whutddk/MK64F-platform/doc/designDoc/1-1-MK-LQFP144/mmexport1516165831264.bmp

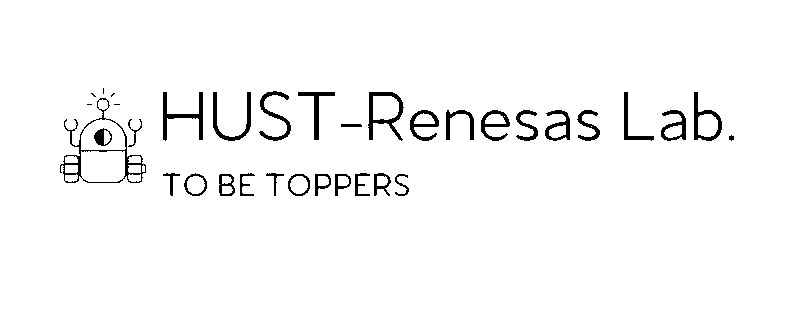
doc/designDoc/1-1-MK-LQFP144/mmexport1516165831264.bmp
