whutddk/MK64F-platform/outputFile/pre-release-version/0-4-Cmsis-dap32F103.pdf

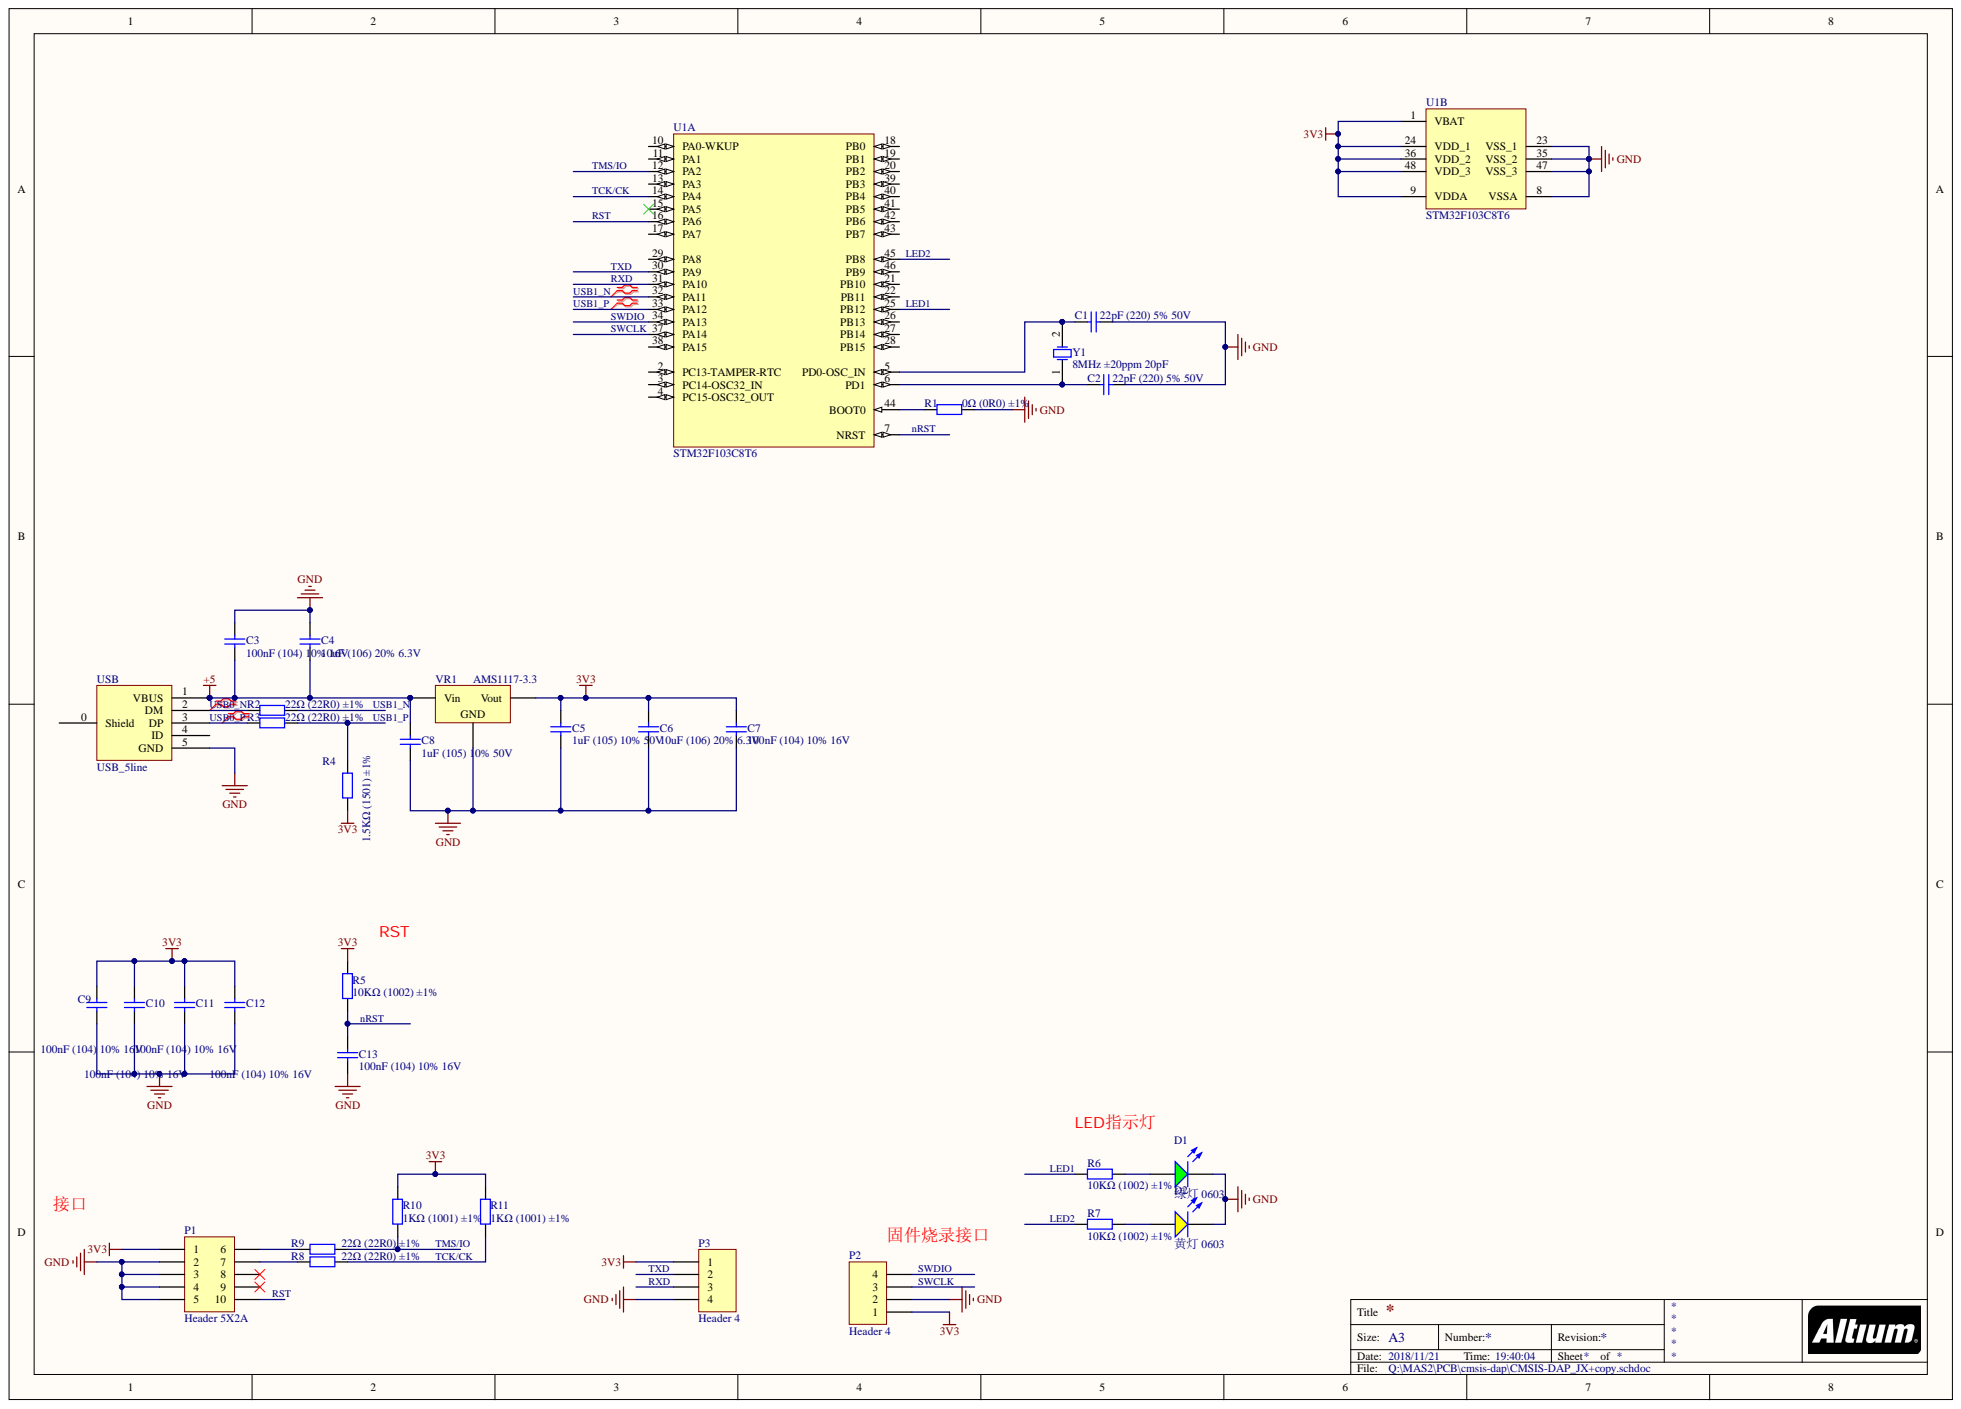
[picture p39: page 1]

* Title | * * * * *

Size: A3 | Number: * | Revision: *
Date: 2018/11/21 Time: 19:40:04 | | Sheet * of *

Q:\MAS2\PCB\cmsis-dap\CMSIS-DAP_JX+copy.schdoc

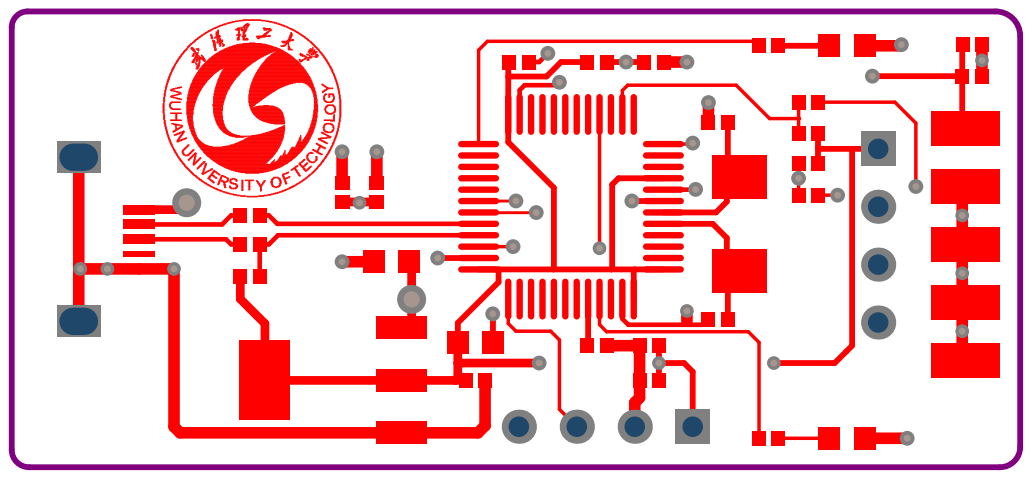
[picture p40: page 2]

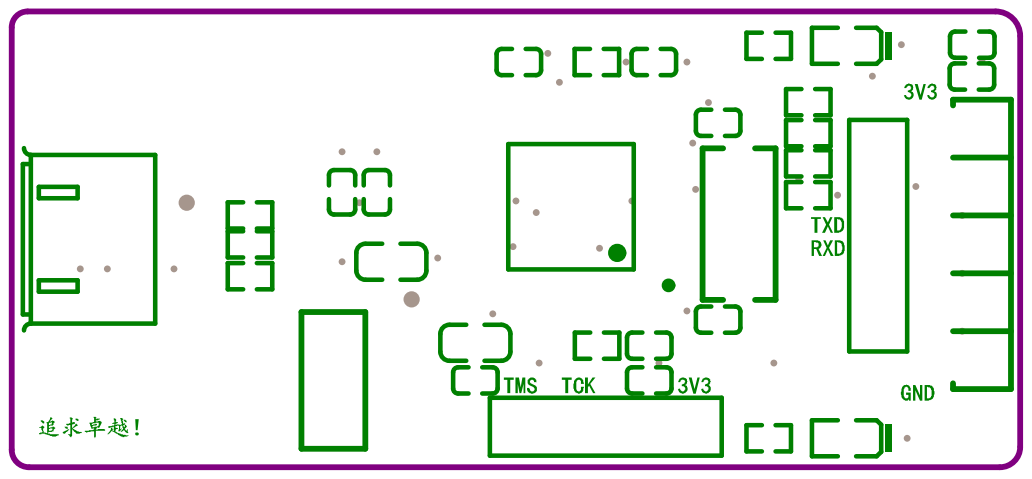
[picture p41: page 3]

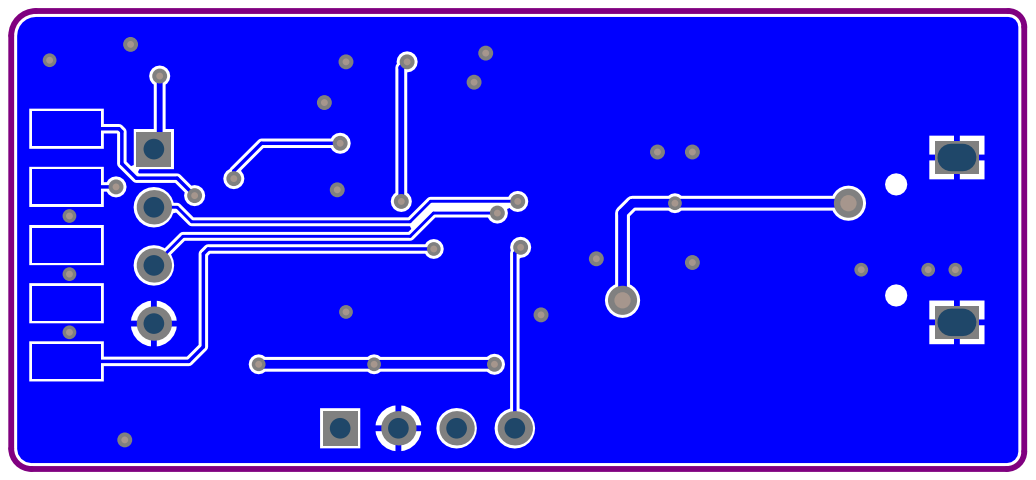
[picture p42: page 4]

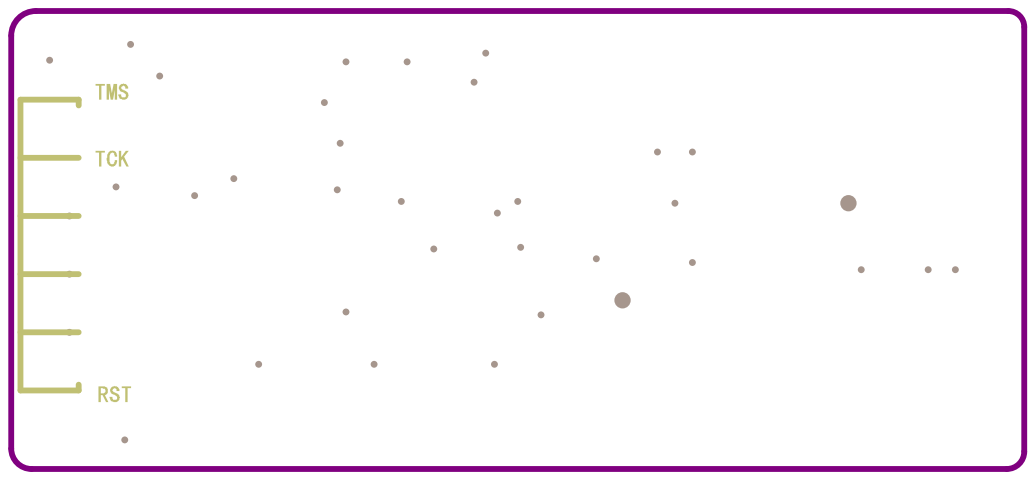
[picture p43: page 5]
