whutddk/MK64F-platform/doc/referDoc/STM32/XNUCLEO.pdf

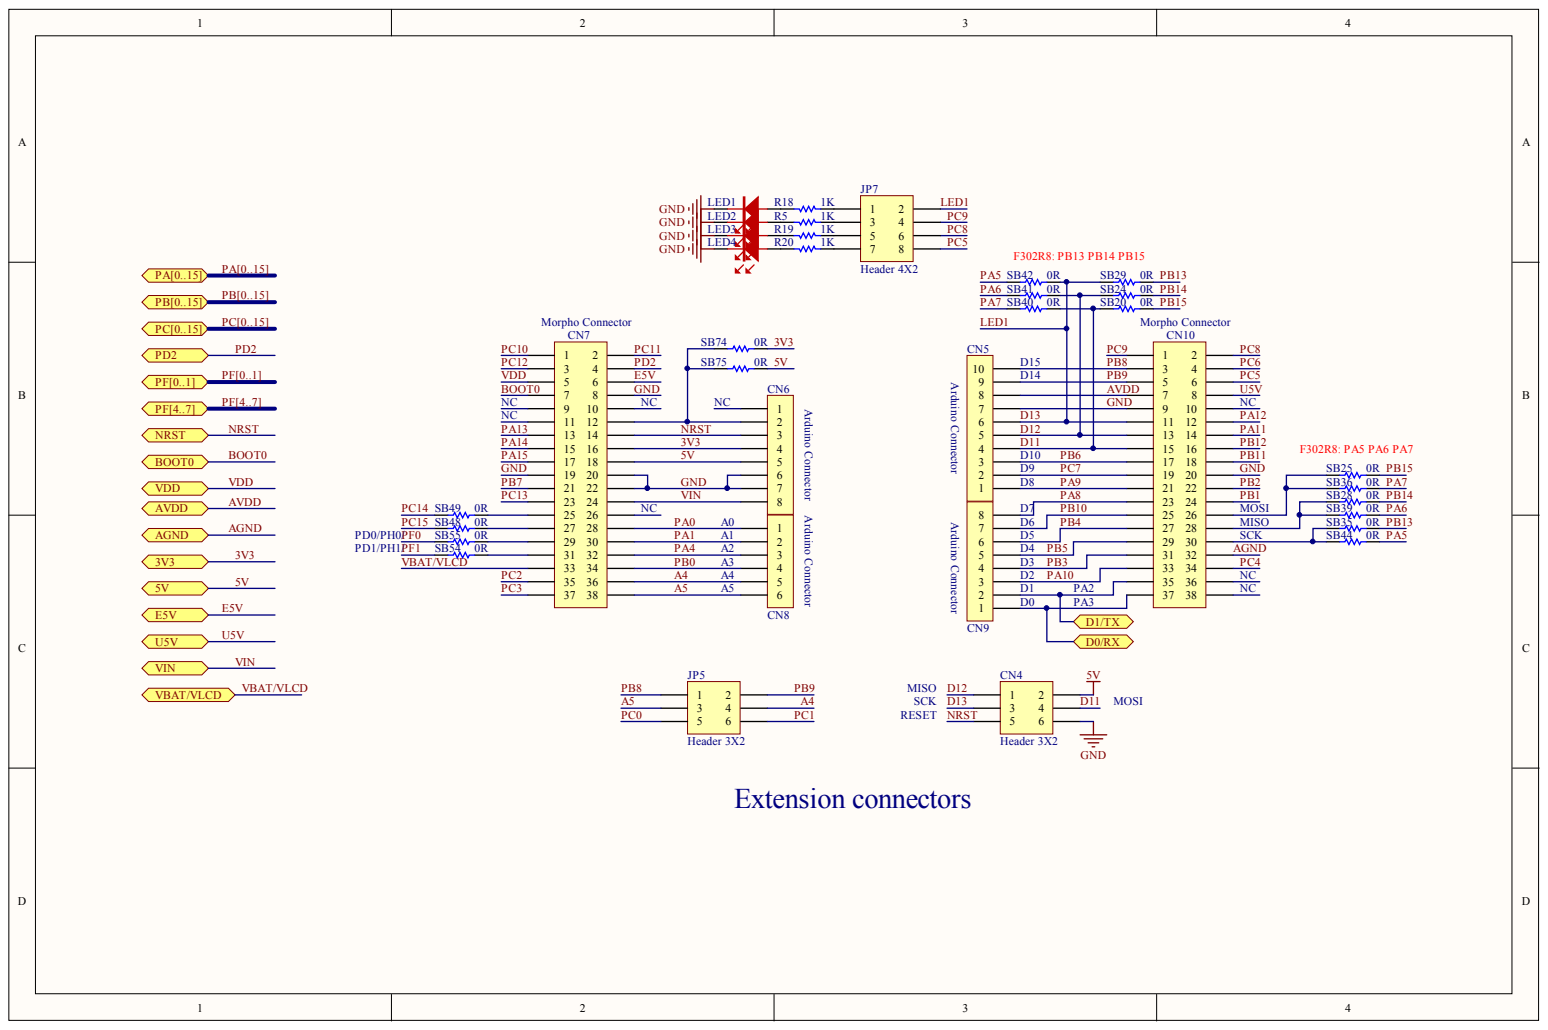
[picture p44: page 1]

Arduino Connector

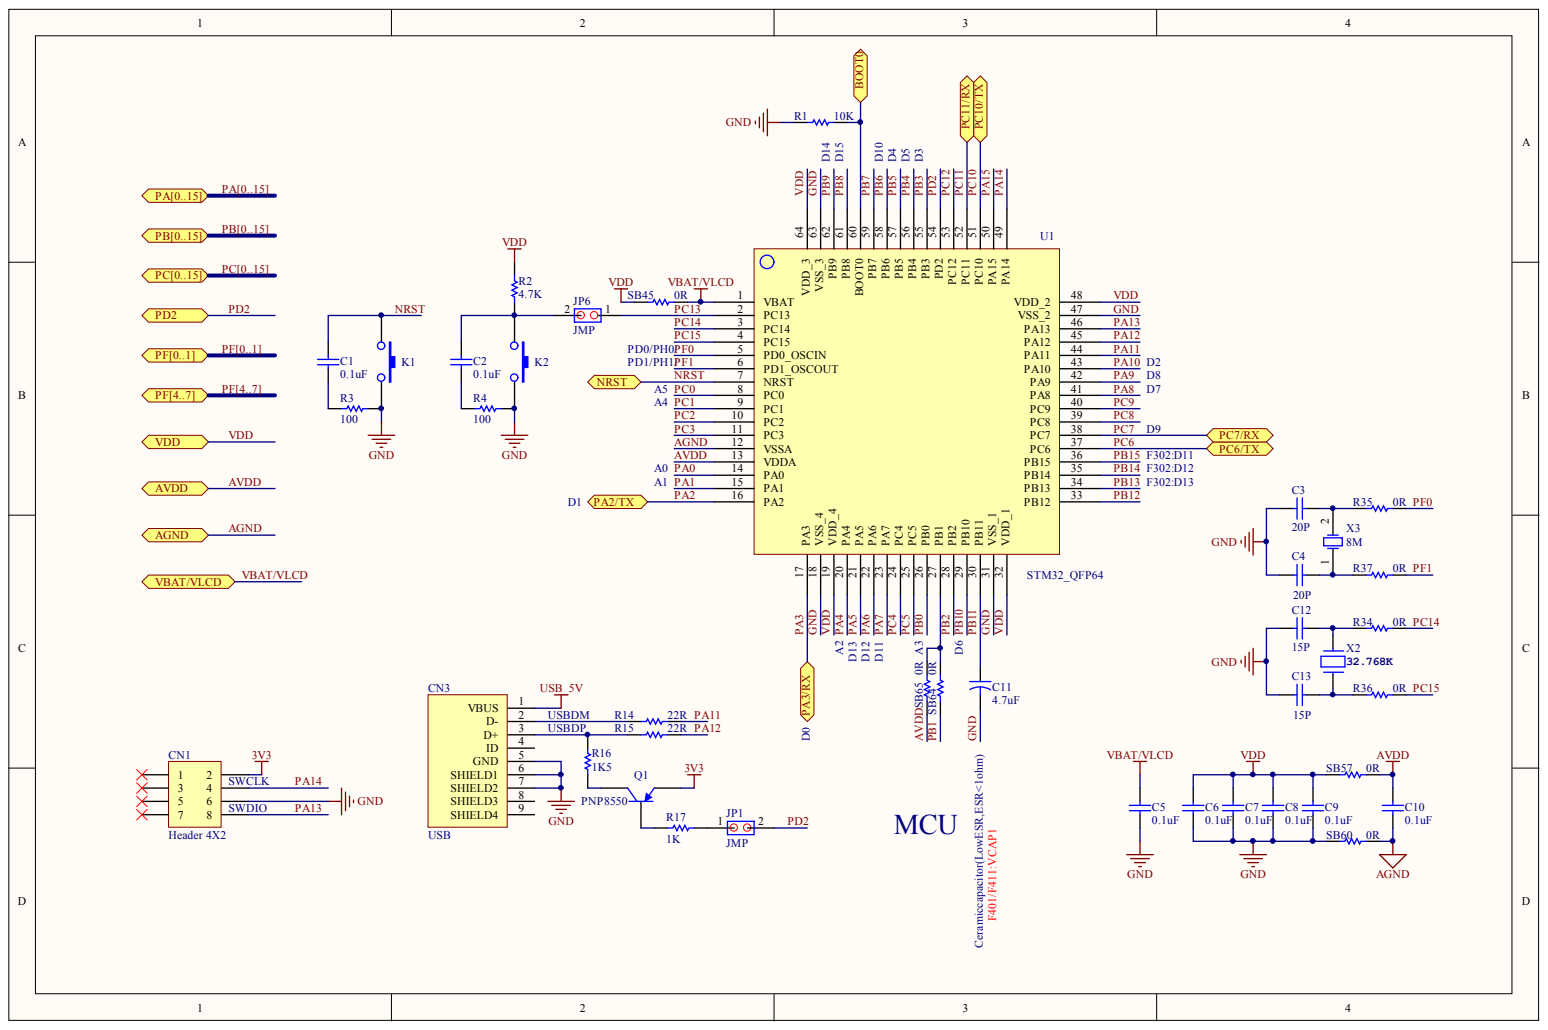
[picture p45: page 2]

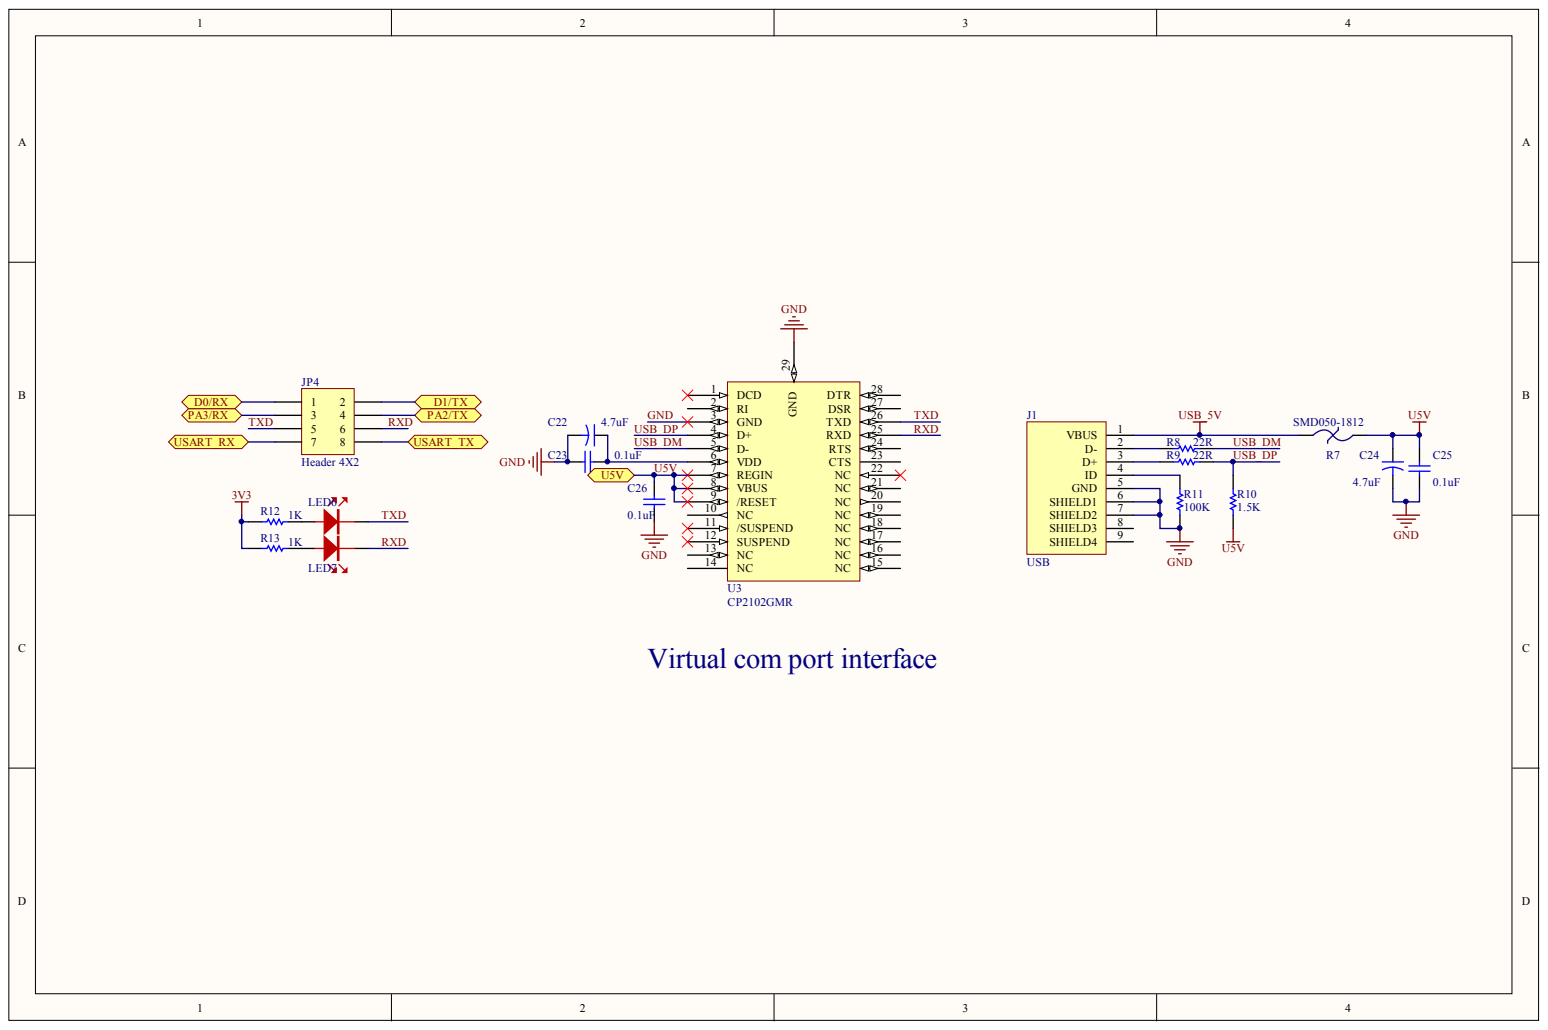
[picture p46: page 3]

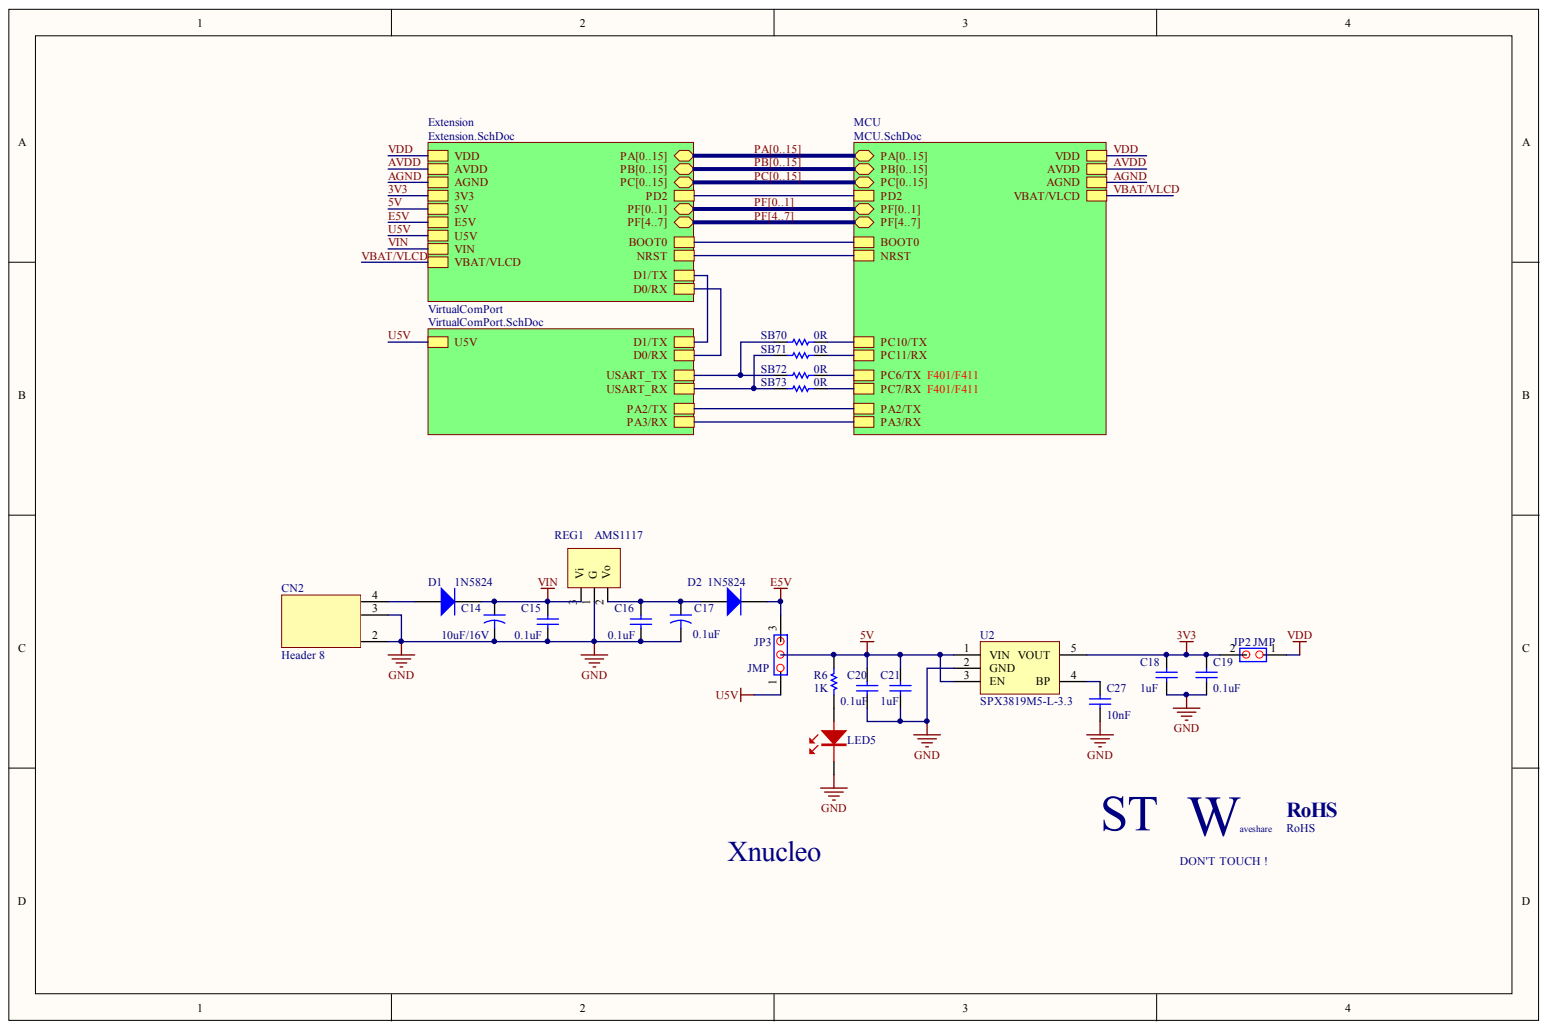
[picture p47: page 4]
