whutddk/MK64F-platform/doc/referDoc/MAPS-K64/07.MAPS-Dock.pdf

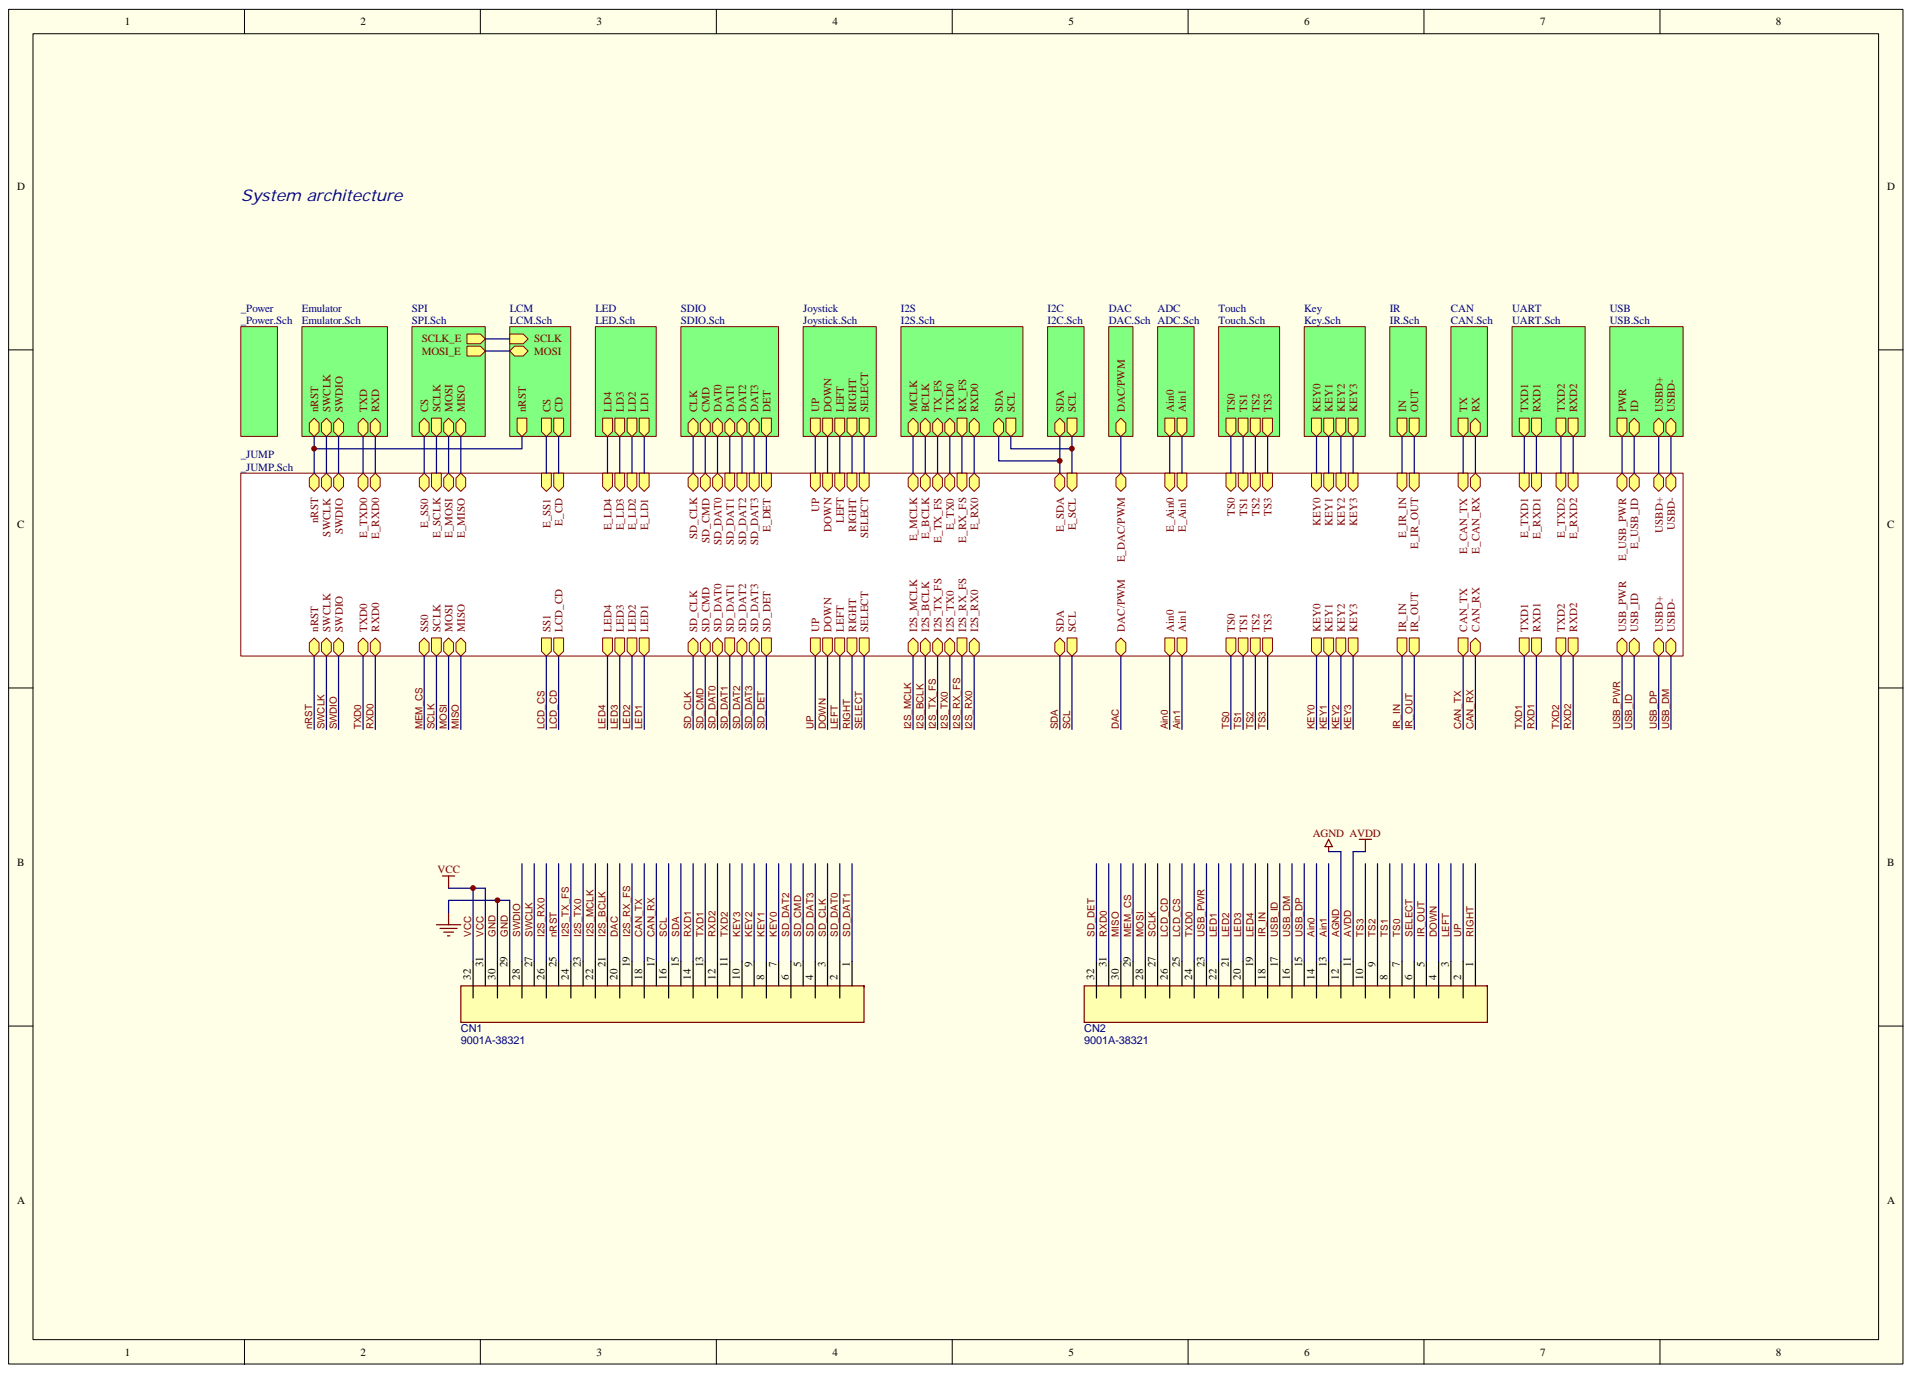
[picture p48: page 1]
SWCLK; SWDIO; TXD0; RXD0; MEM_CS; SCLK; MOSI; MISO; LCD_CS; LCD_CD; SD_CLK; SD_CMD; SD_DAT0; SD_DET; DOWN; LEFT; RIGHT; SELECT; I2S_MCLK; I2S_BCLK; DAC; IR_OUT; CAN_TX; CAN_RX; TXD1; RXD1; TXD2; RXD2; USB_PWR; USB_DP; USB_DM; E_MCLK; E_BCLK; E_TXD1 E_RXD1; E_TXD2; E_RXD2; E_MISO; E_SCLK E_MOSI; E_Ain1; E_CAN_TX; E_CAN_RX; E_IR_OUT; SD_DAT1; E_SDA E_SCL; E_DAC/PWM; E_TXD0; E_RXD0; E_USB_PWR; USBD+; USBD-; KEY2; SCLK MOSI; LED3; I2S_MCLK I2S_BCLK; SDA SCL; DAC/PWM; Ain1; KEY1; nRST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

USB USB.Sch

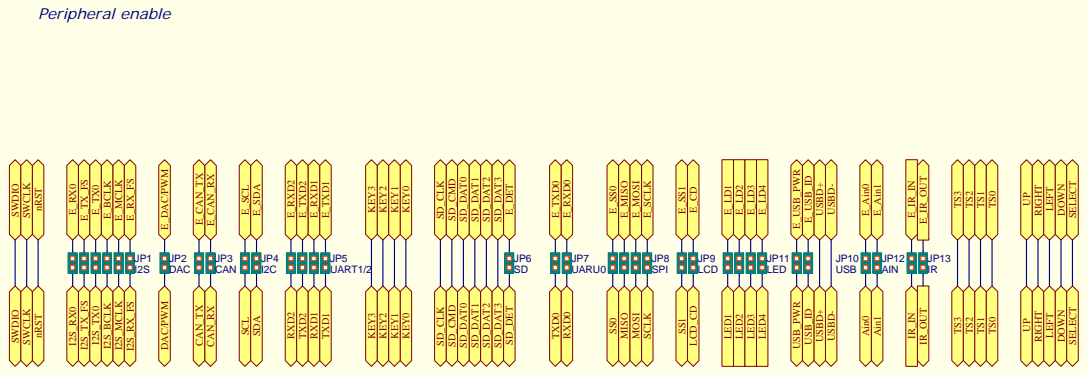
[picture p49: page 2]

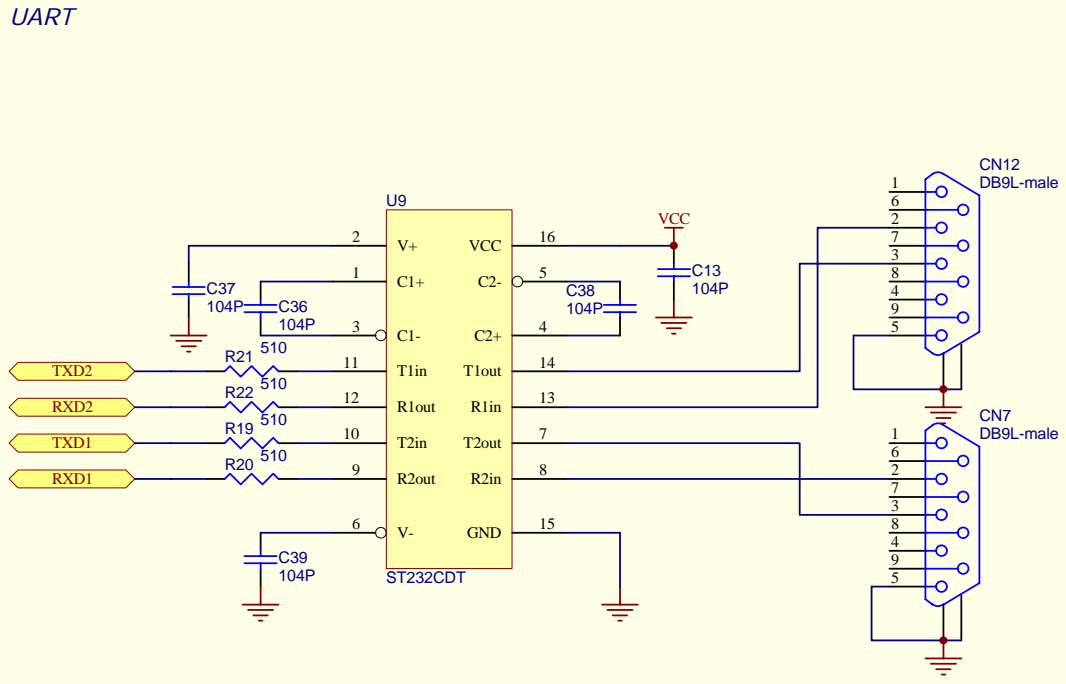
[picture p50: page 3]

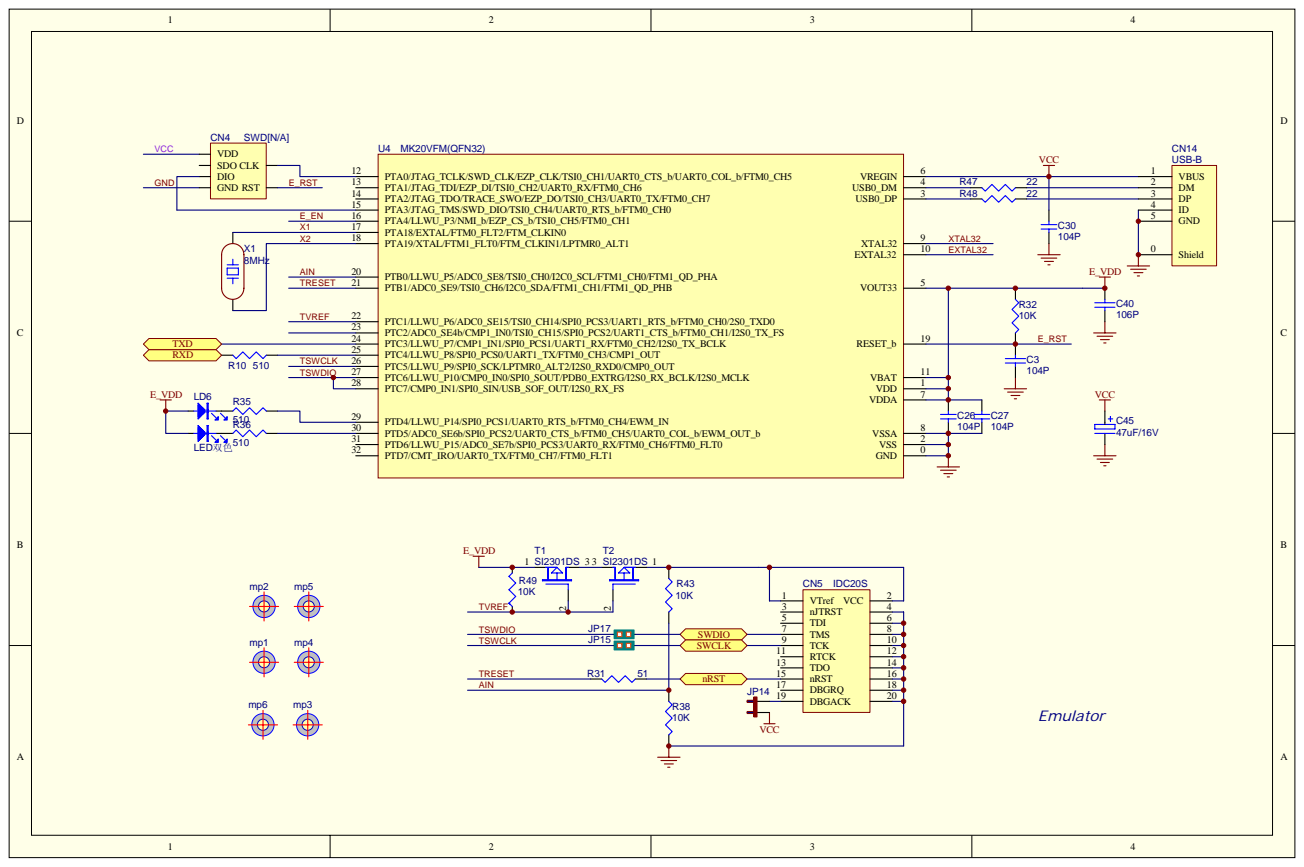
[picture p51: page 4]

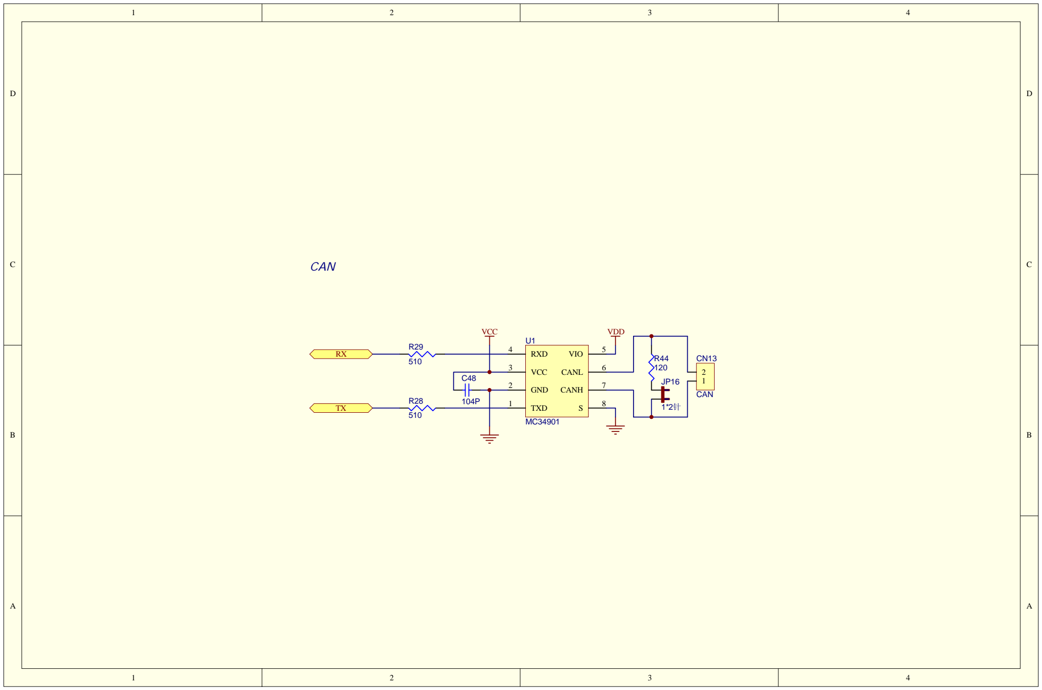
[picture p52: figure]
TXD 1; GND 2; VCC 3; RXD 4; VIO; CANL; CANH; CAN; VCC; VDD
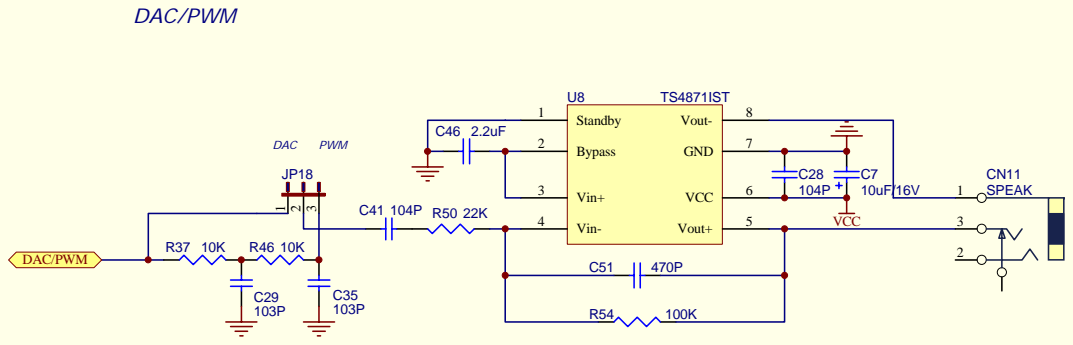
[picture p53: page 6]

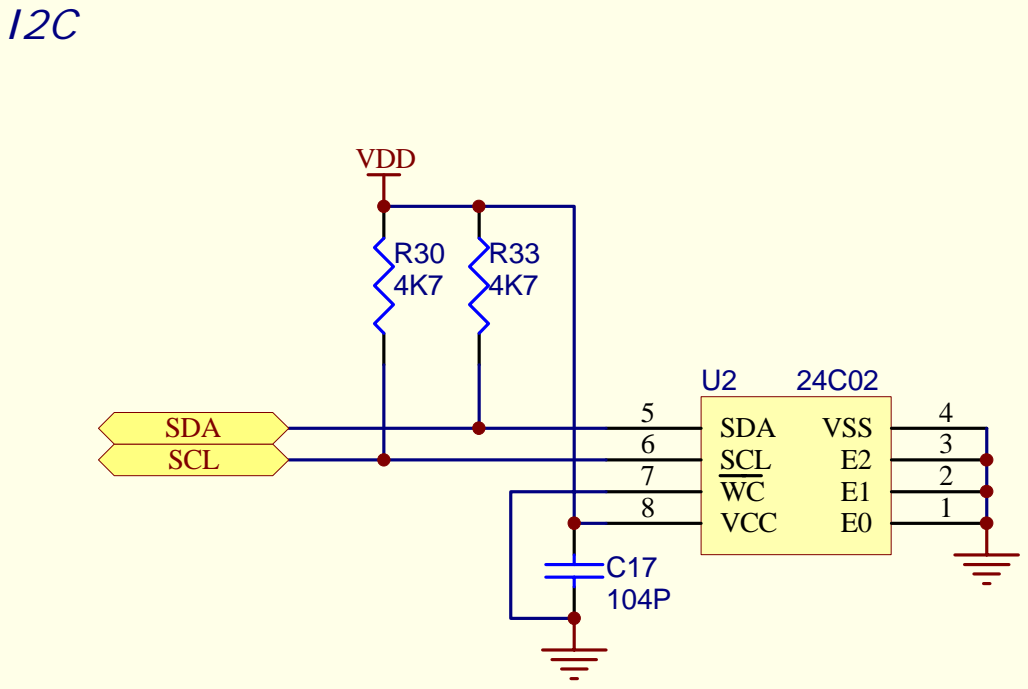
[picture p54: page 7]
3 VSS; 4 SDA 5; SCL 6; VCC 8; VDD; SCL; SDA

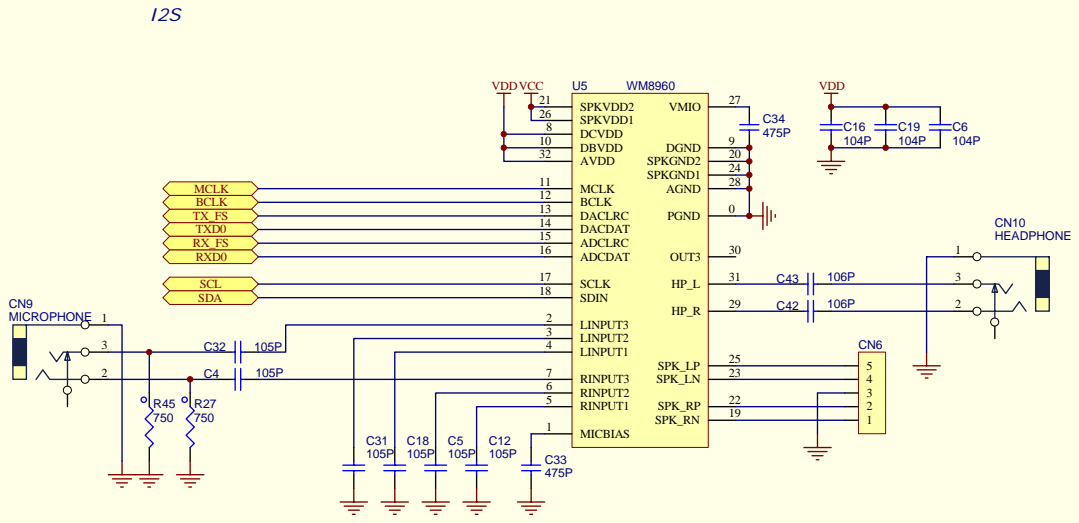
[picture p55: page 8]

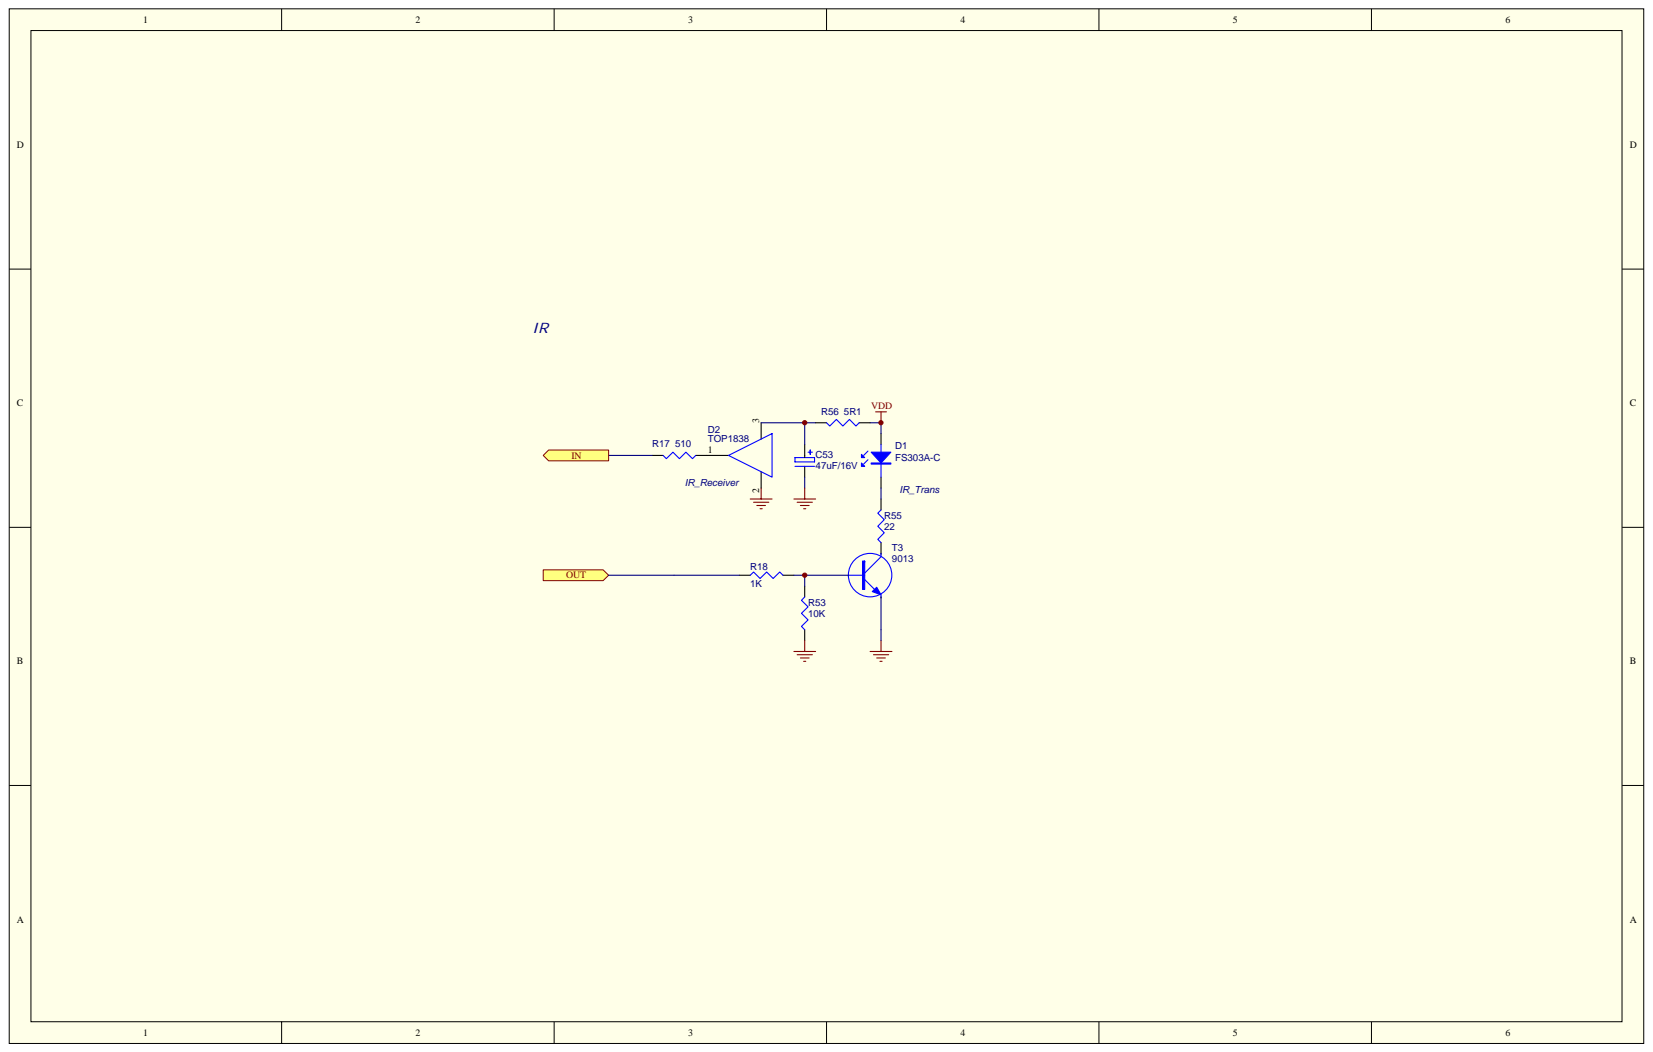
[picture p56: page 9]

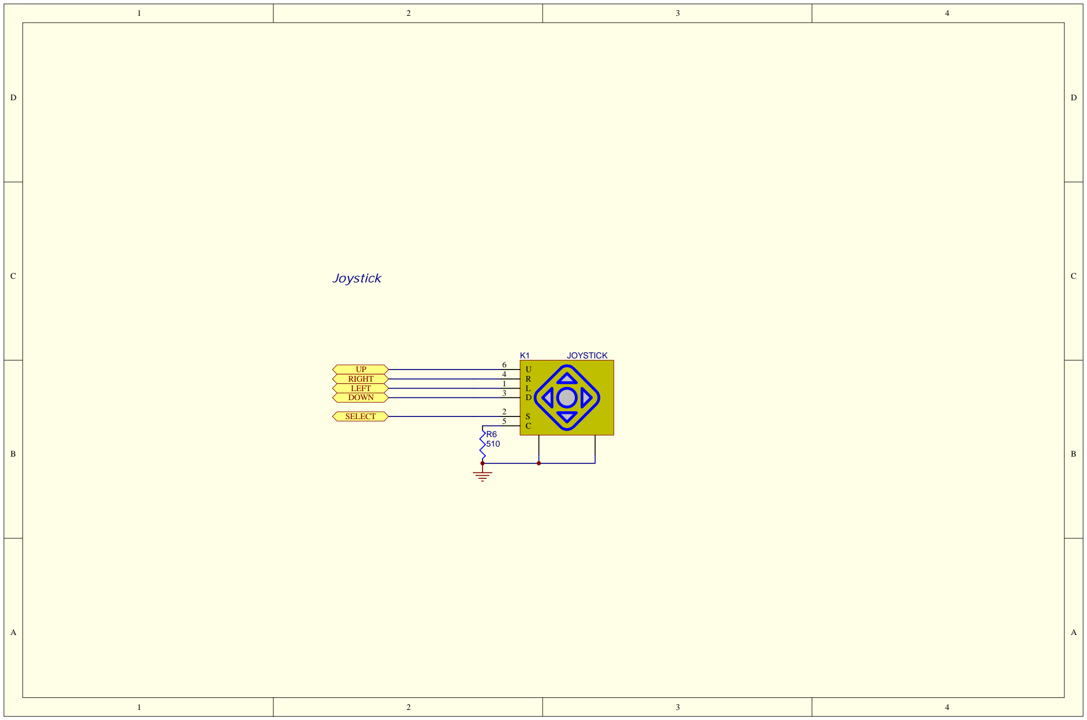
[picture p57: figure]
UP RIGHT LEFT DOWN; SELECT; JOYSTICK; Joystick
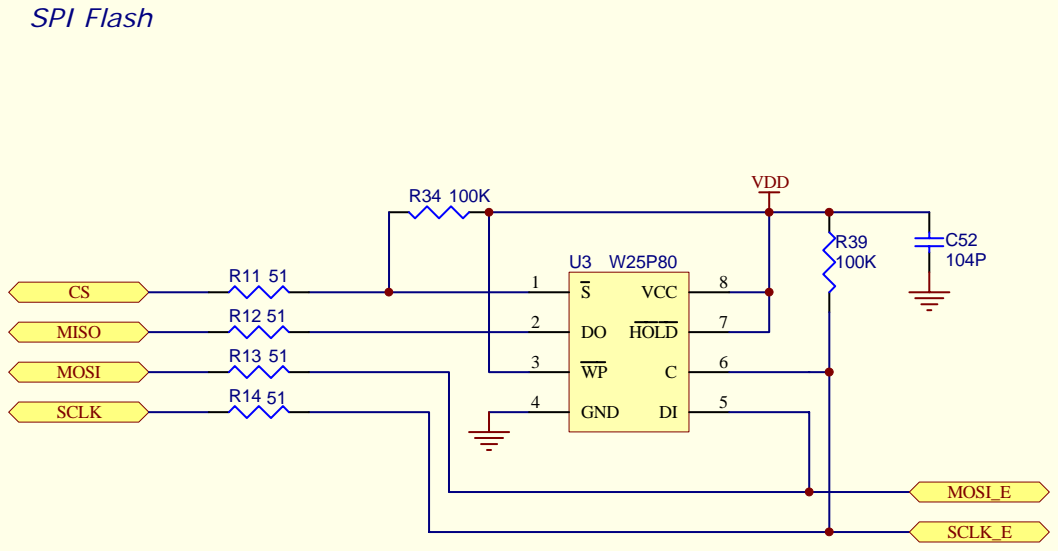
[picture p58: page 11]

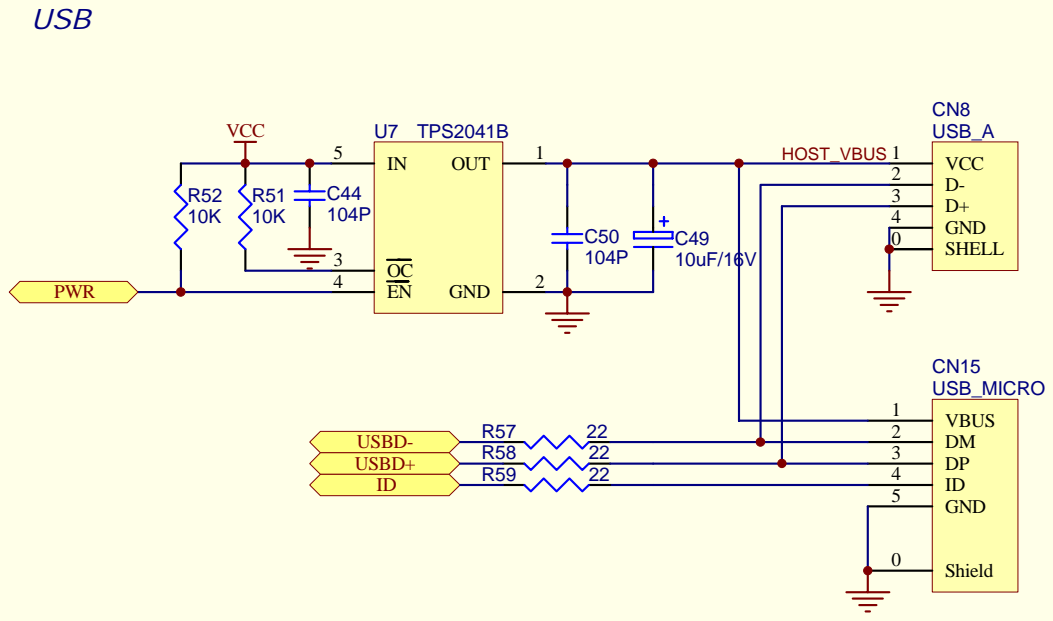
[picture p59: page 12]

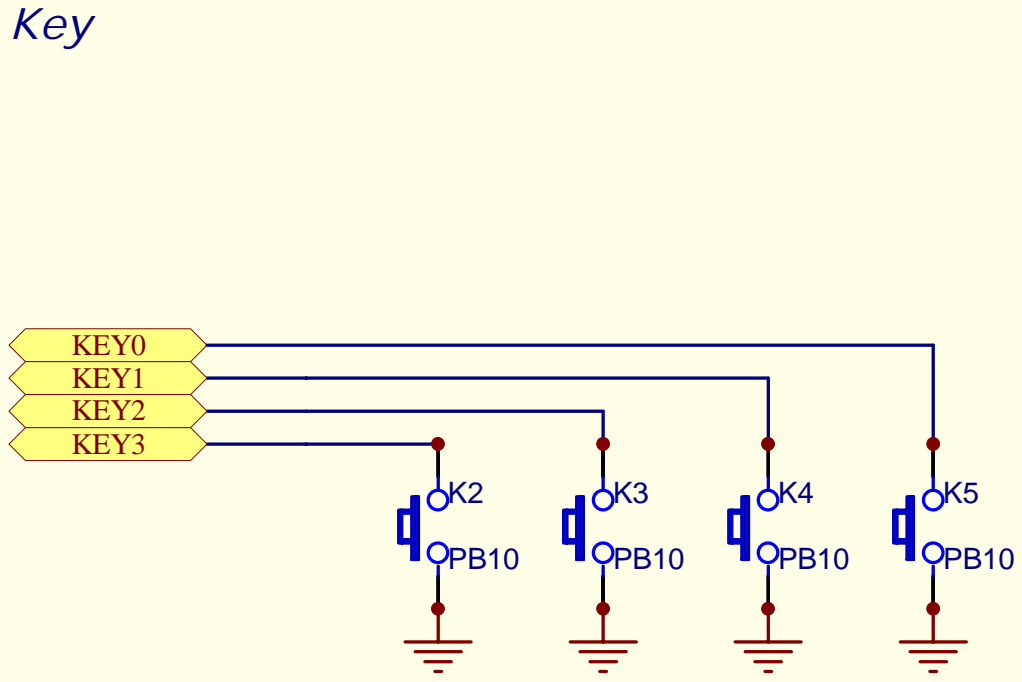
[picture p60: page 13]
KEY0; KEY1 KEY2 KEY3; Key

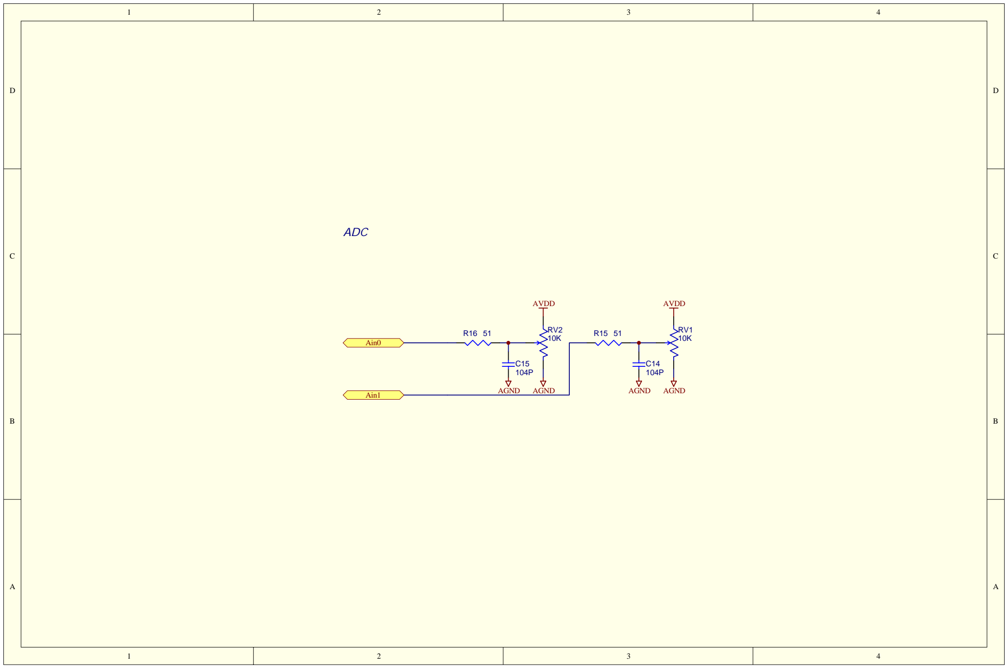
[picture p61: figure]
Ain0; AVDD; AGND; AGND Ain1; ADC
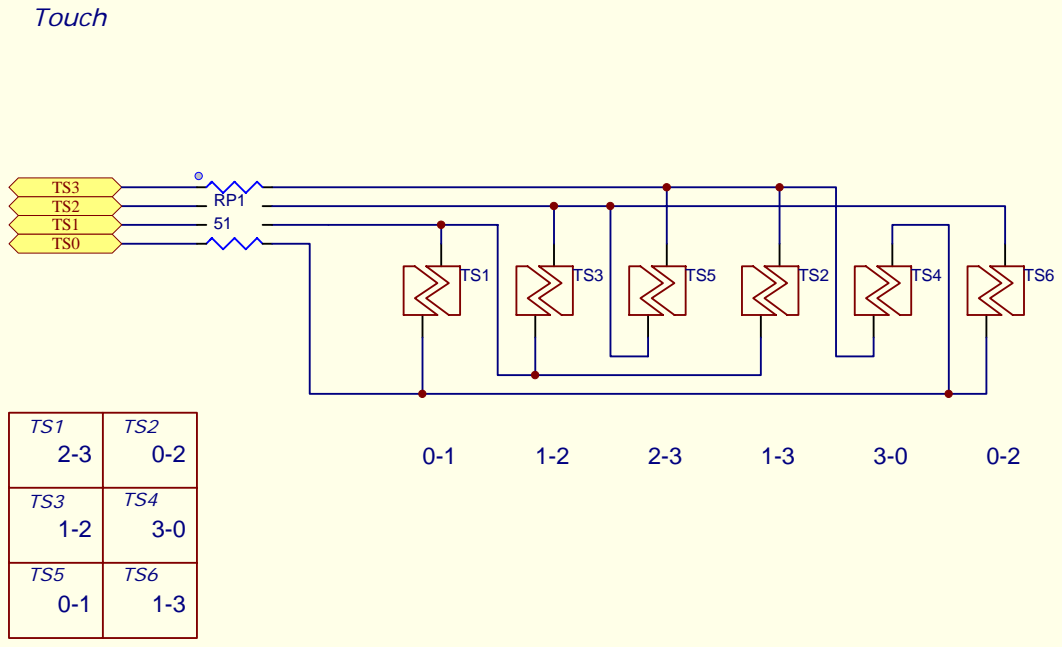
[picture p62: page 15]
Touch

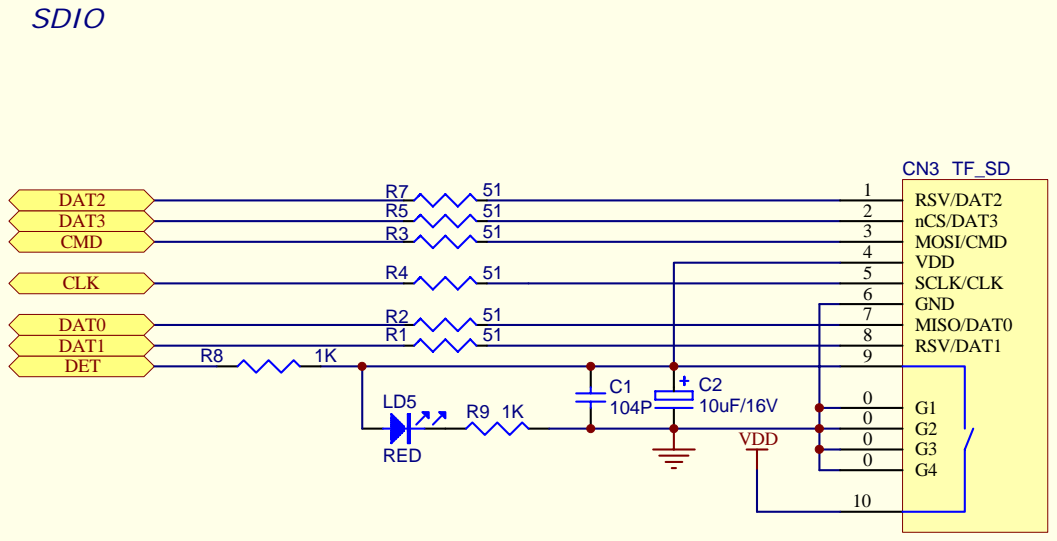
[picture p63: page 16]

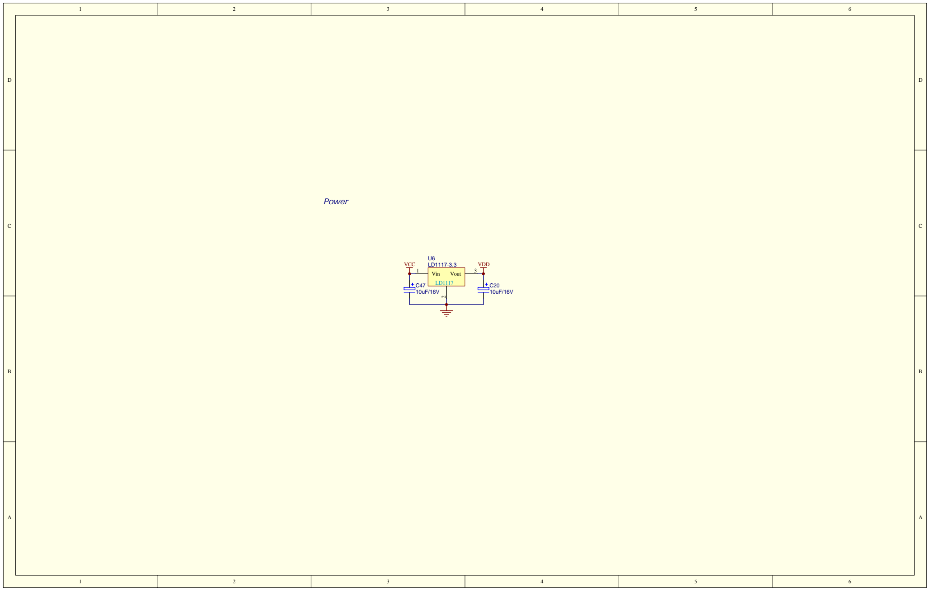
[picture p64: figure]
VDD; Vout; 3 Vin 1; VCC; Power
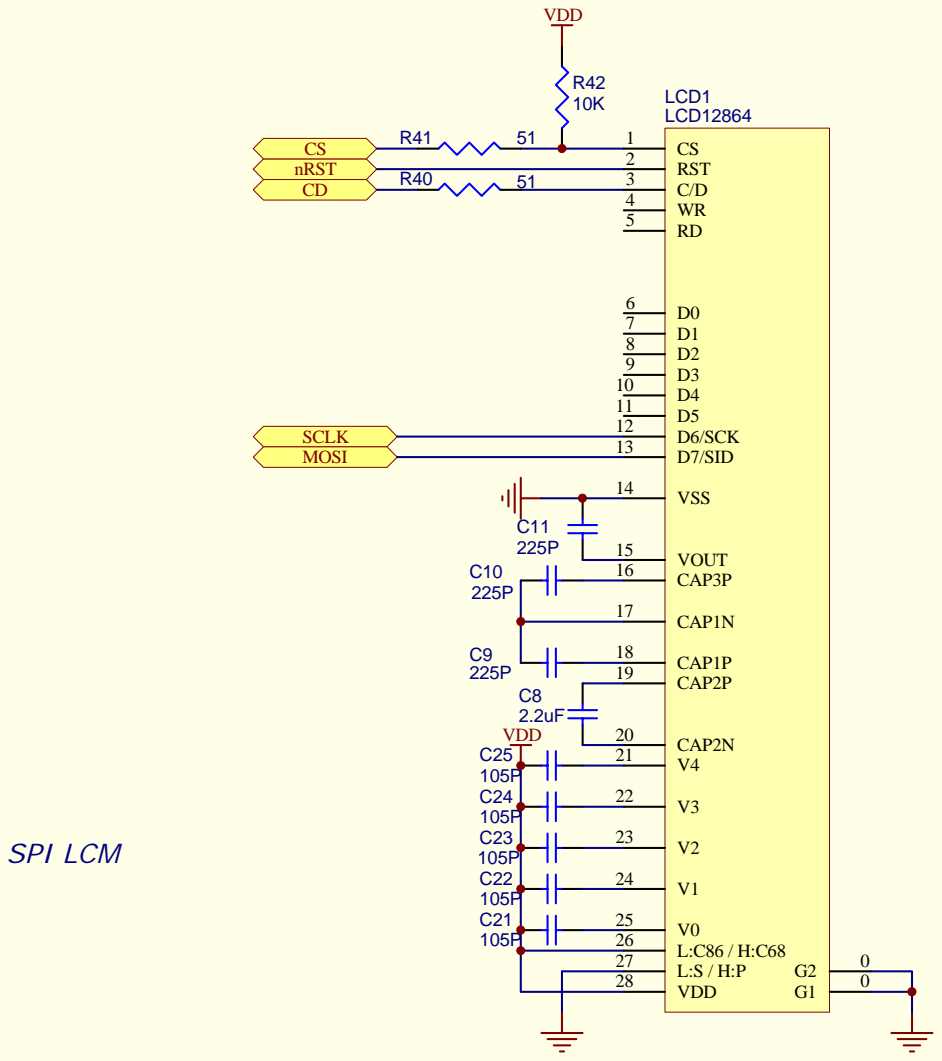
[picture p65: page 18]

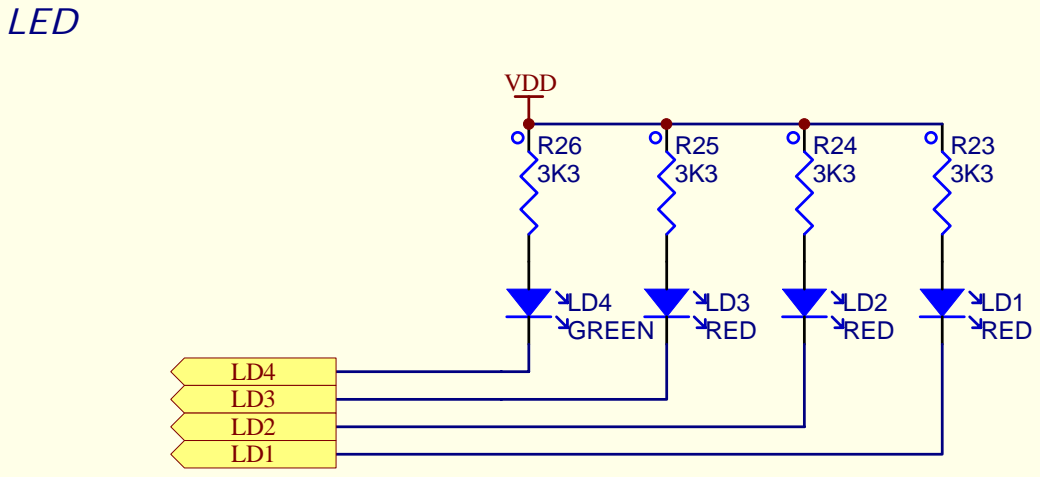
[picture p66: page 19]
LD3 RED; LD4 GREEN; LD1 RED; LD2 RED; VDD; LED
