whutddk/MK64F-platform/PCB/pre-release-version/abort-version/1.6.1/flexplatV1.PDF

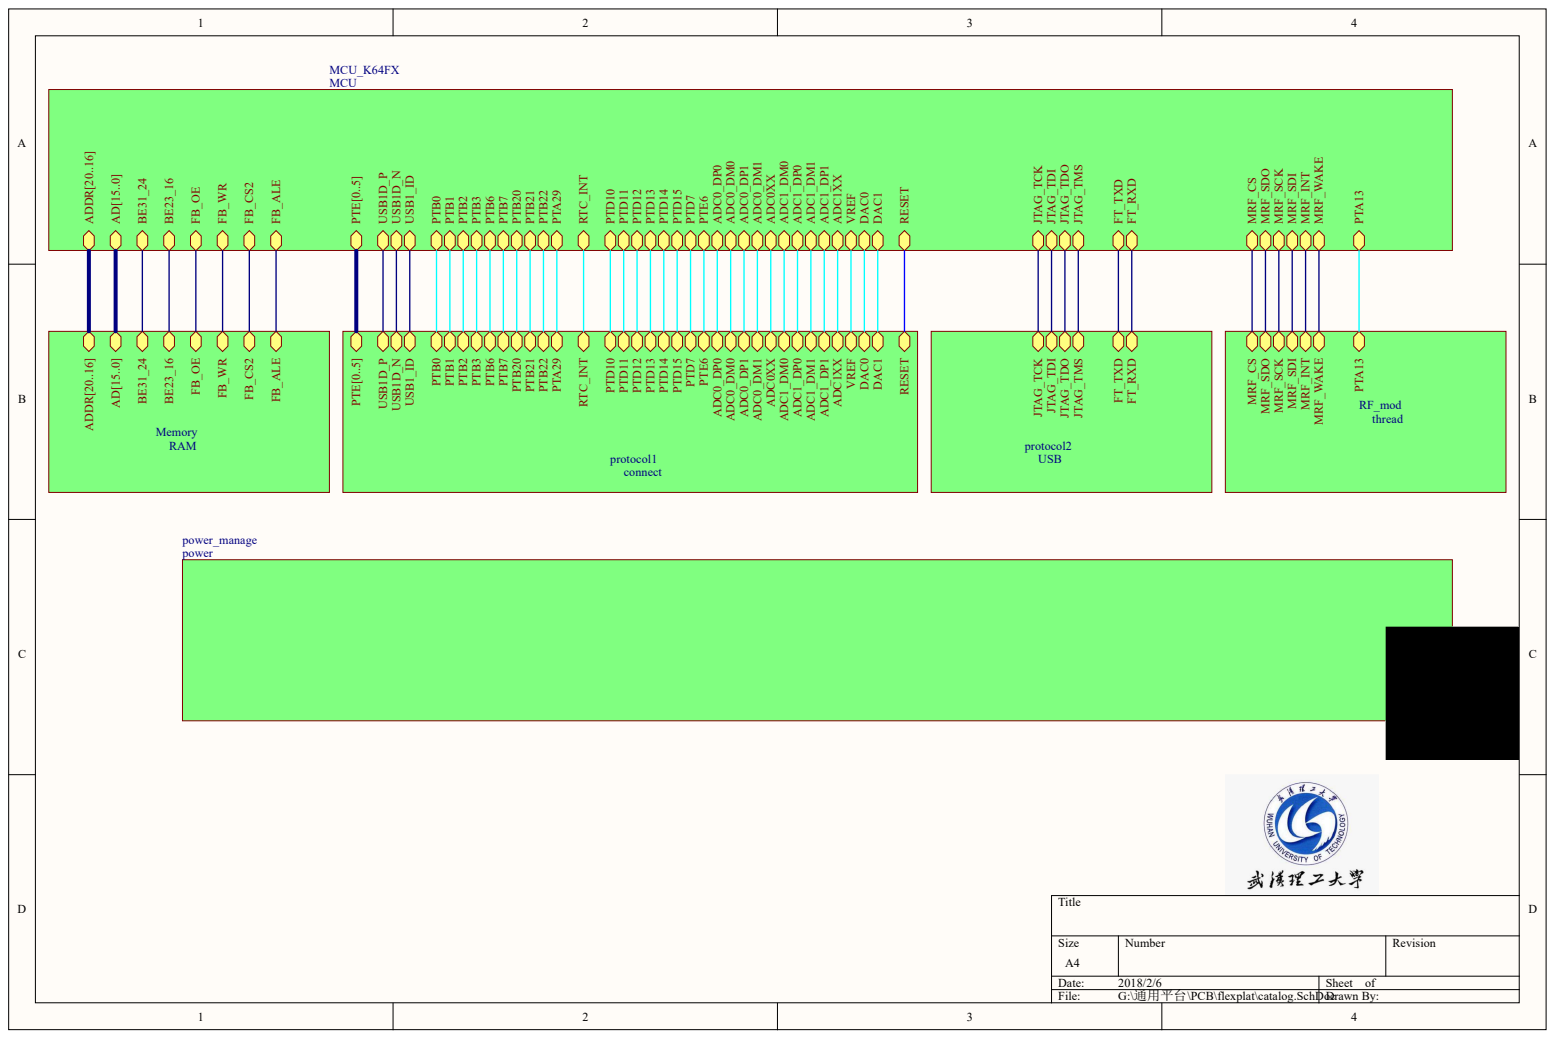
[picture p67: page 1]

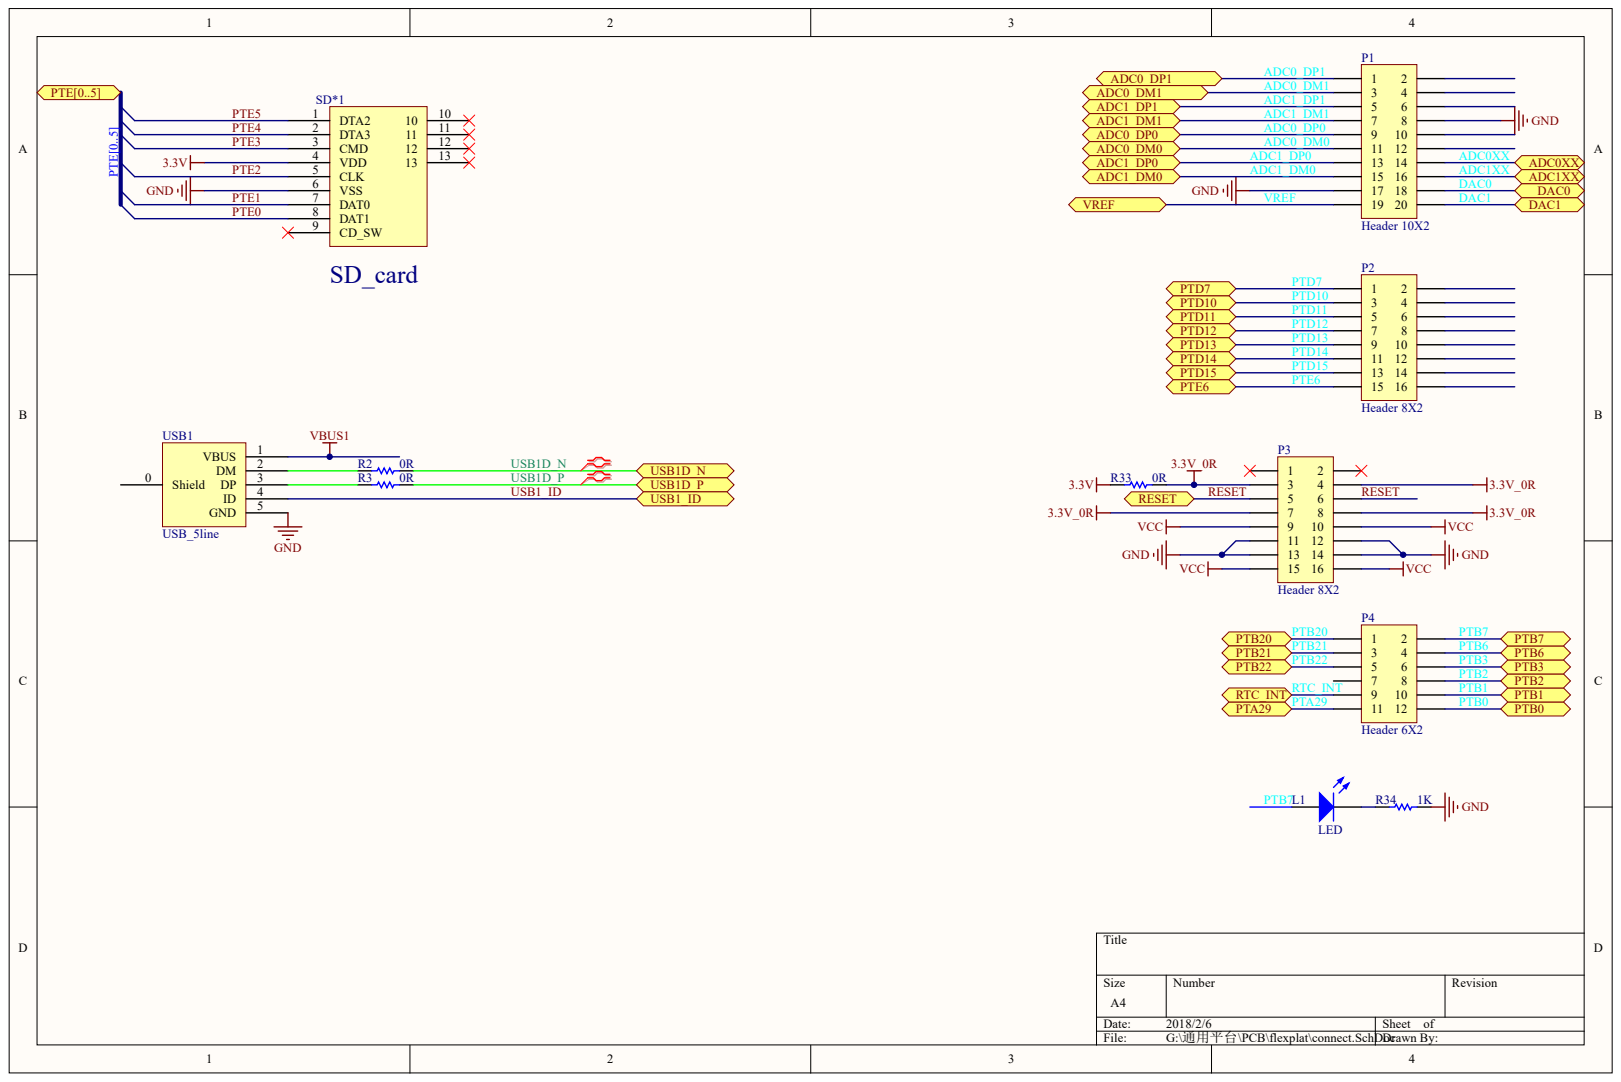
[picture p68: page 2]

PCB\flexplat\connect.SchDoc Drawn By:

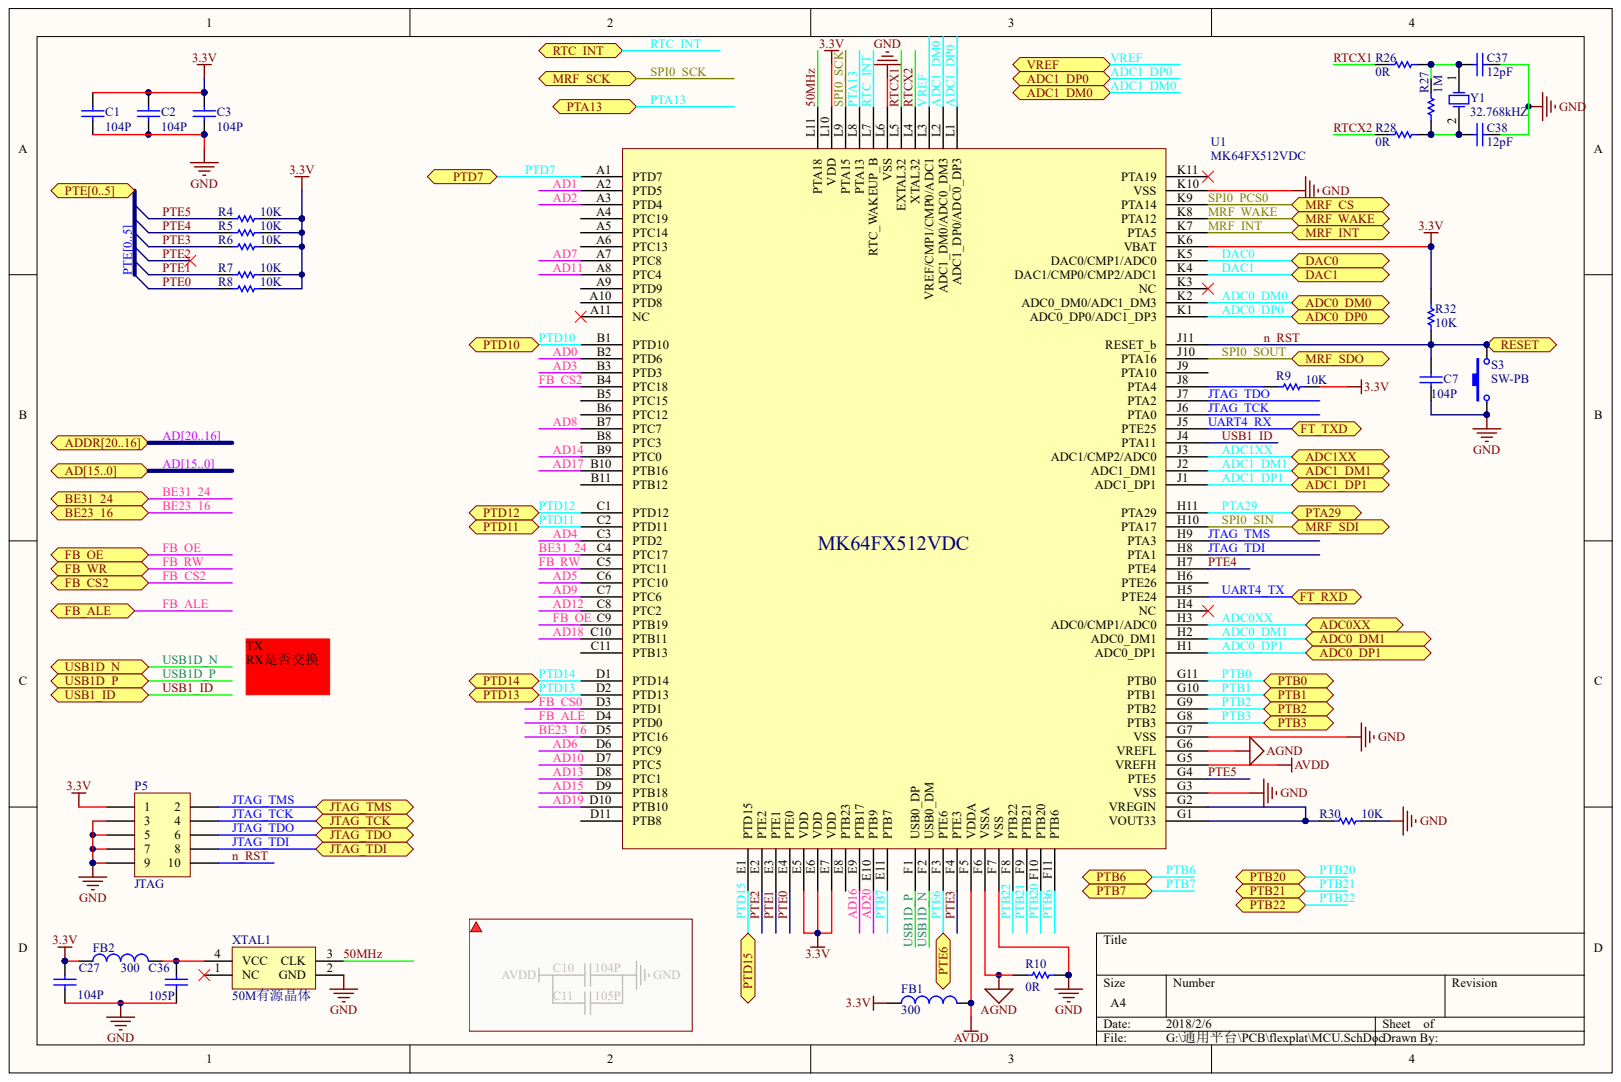
[picture p69: page 3]

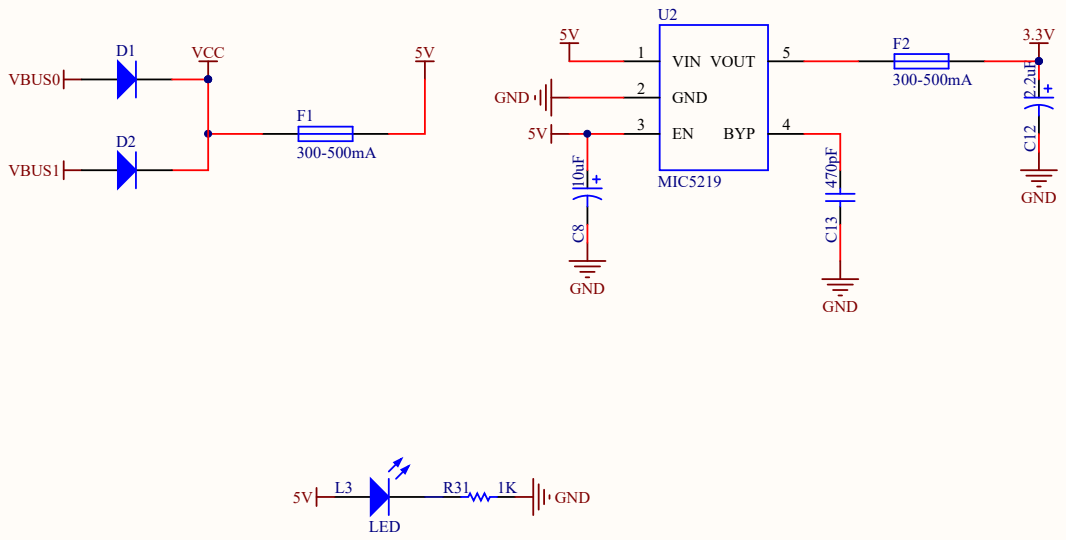
[picture p70: page 4]

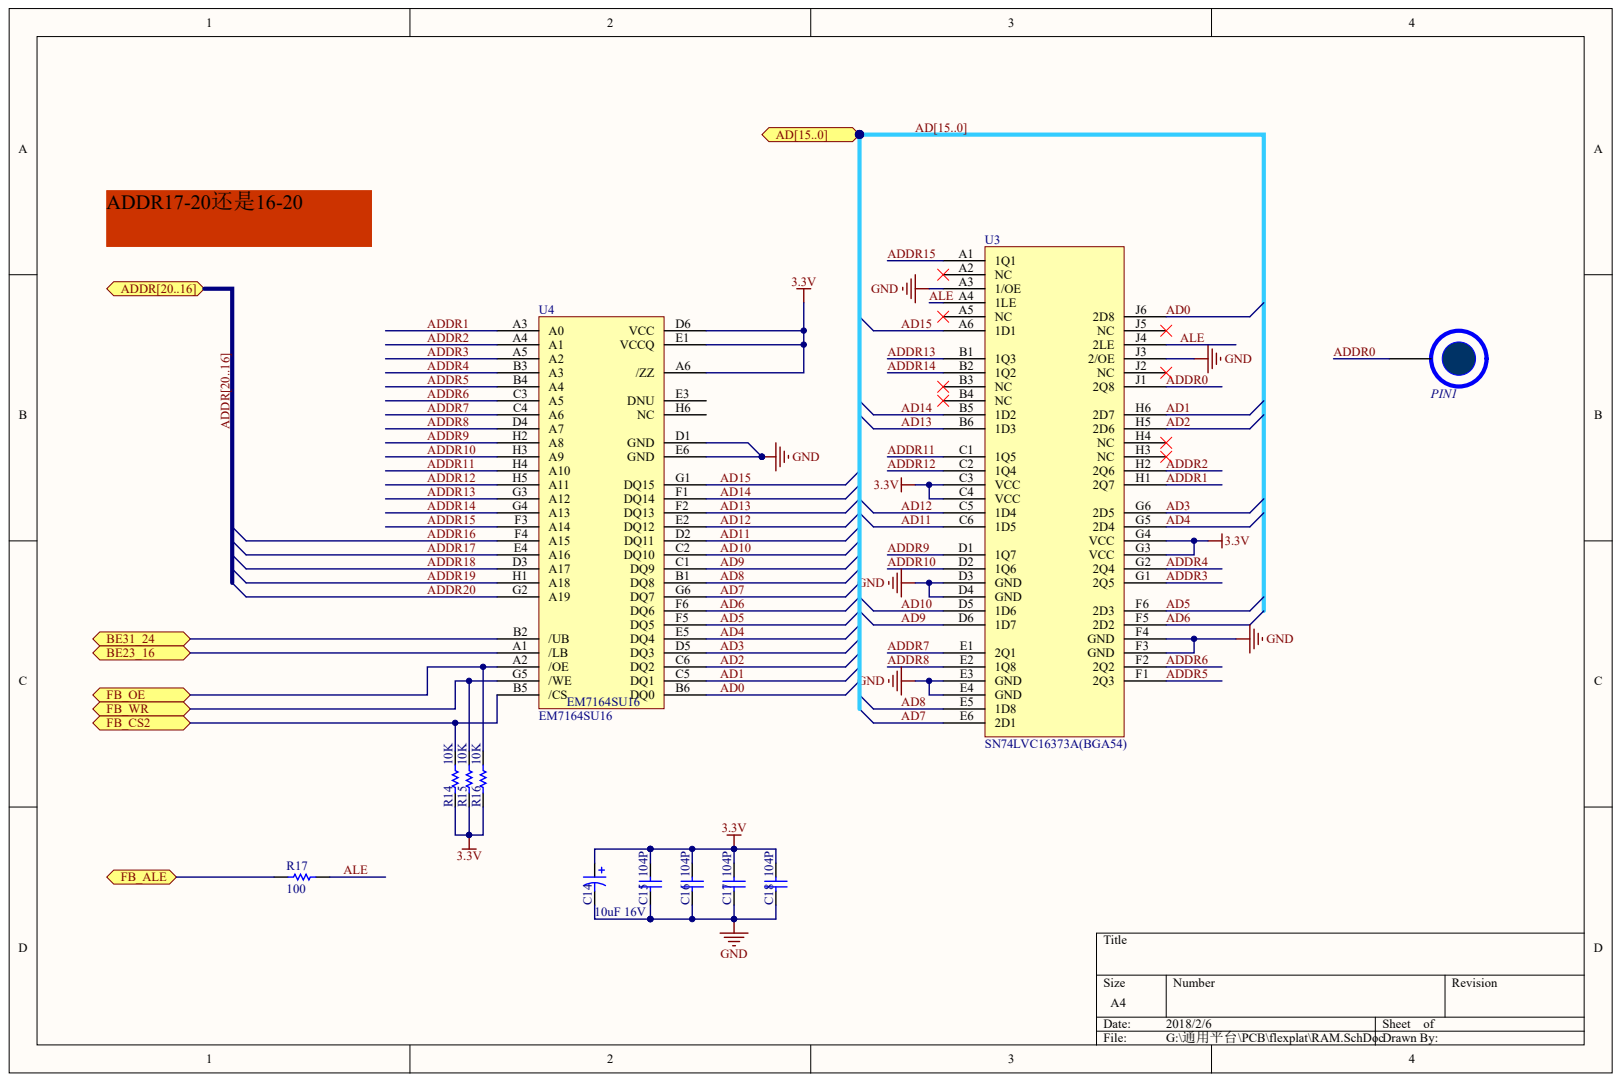
[picture p71: page 5]

PCB\flexplat\RAM.SchDocDrawn By:

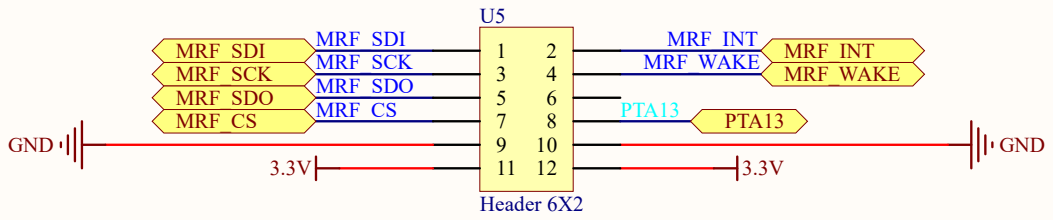
[picture p72: page 6]

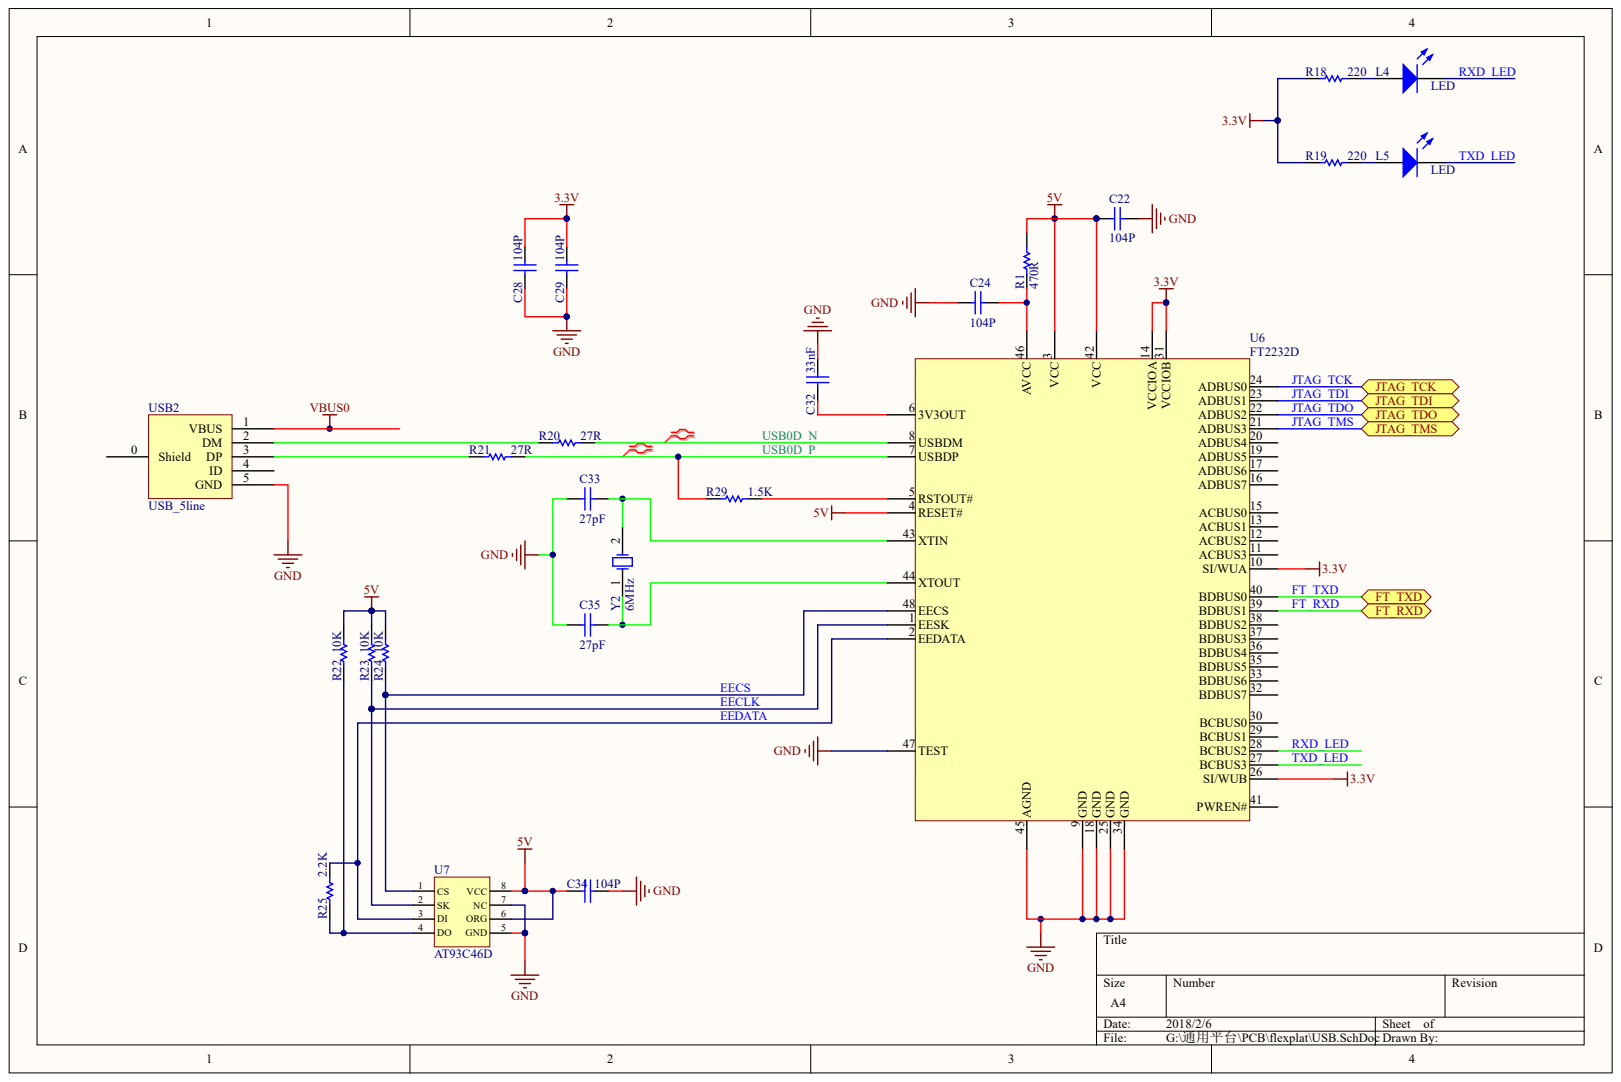
[picture p73: page 7]

EECS 48

EEDATA 2

EECLK
EEDATA

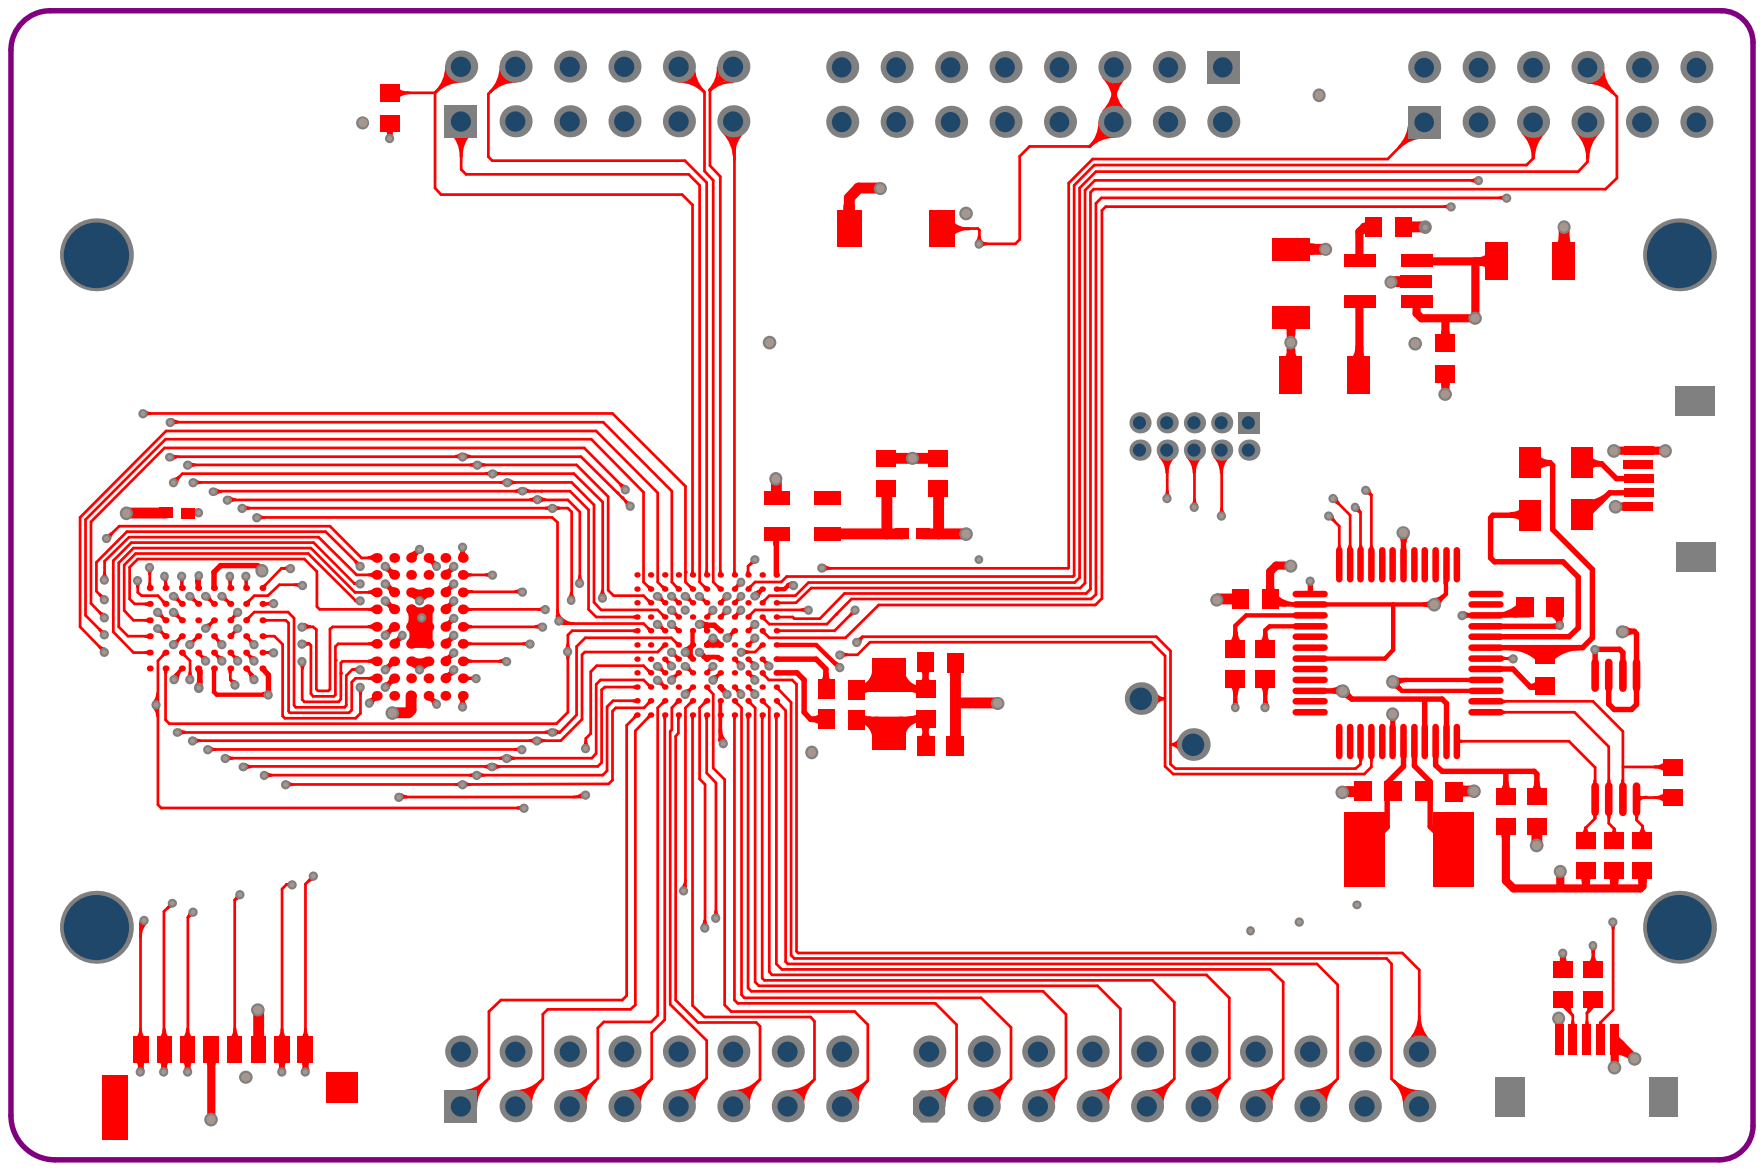
[picture p74: page 8]

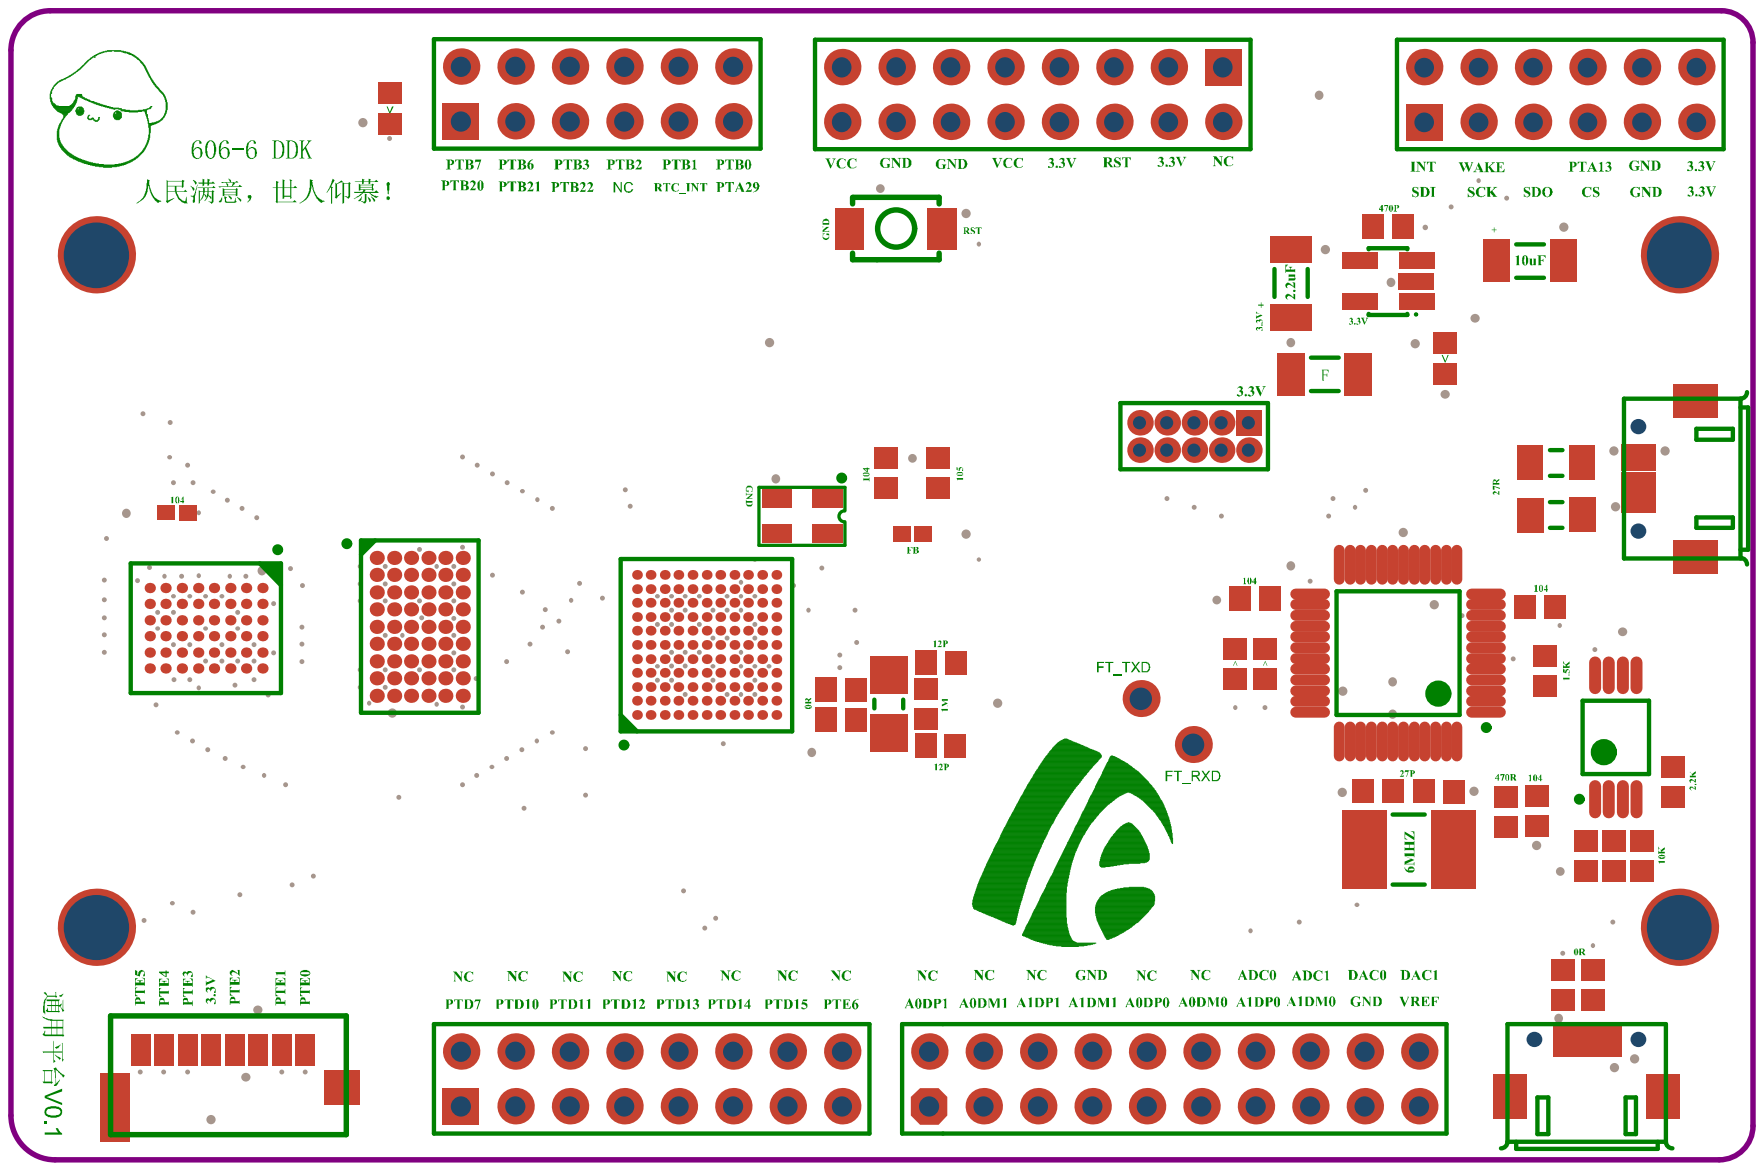
[picture p75: page 9]

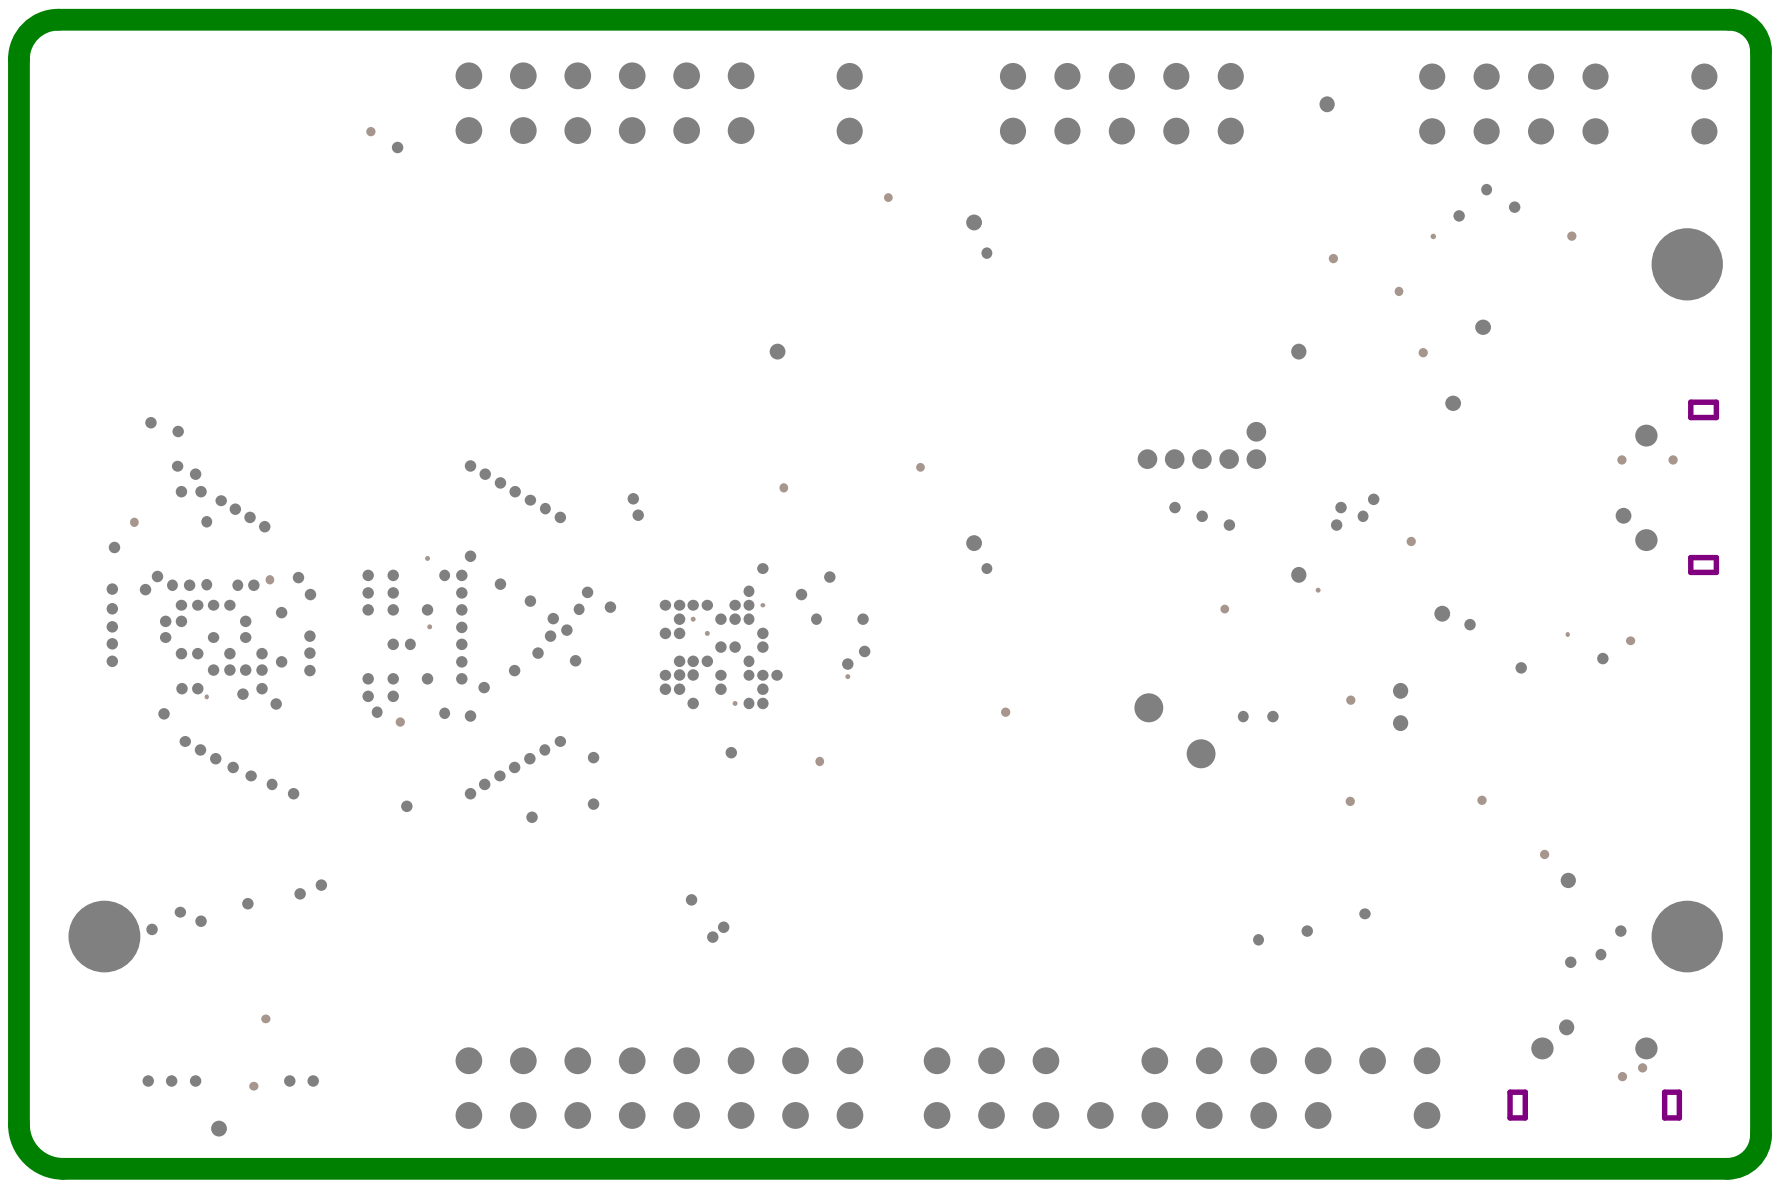
[picture p76: page 10]

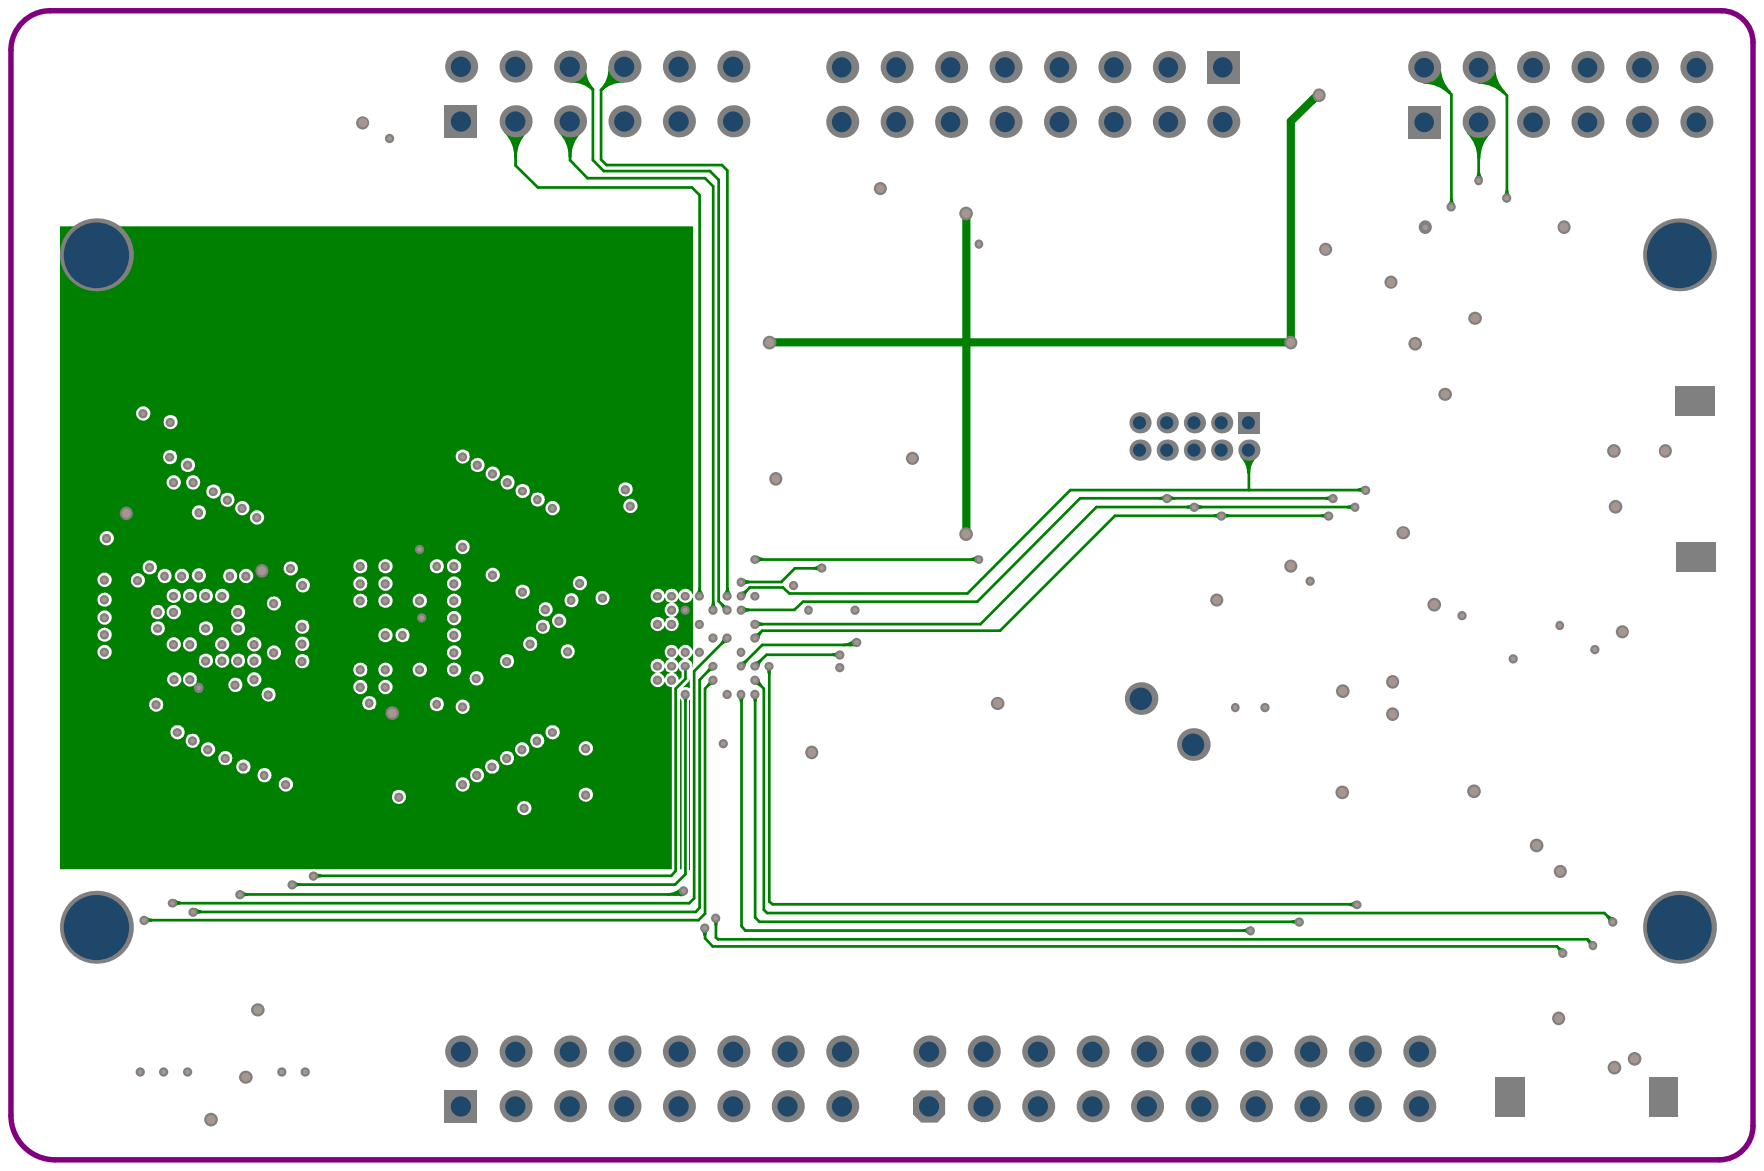
[picture p77: page 11]

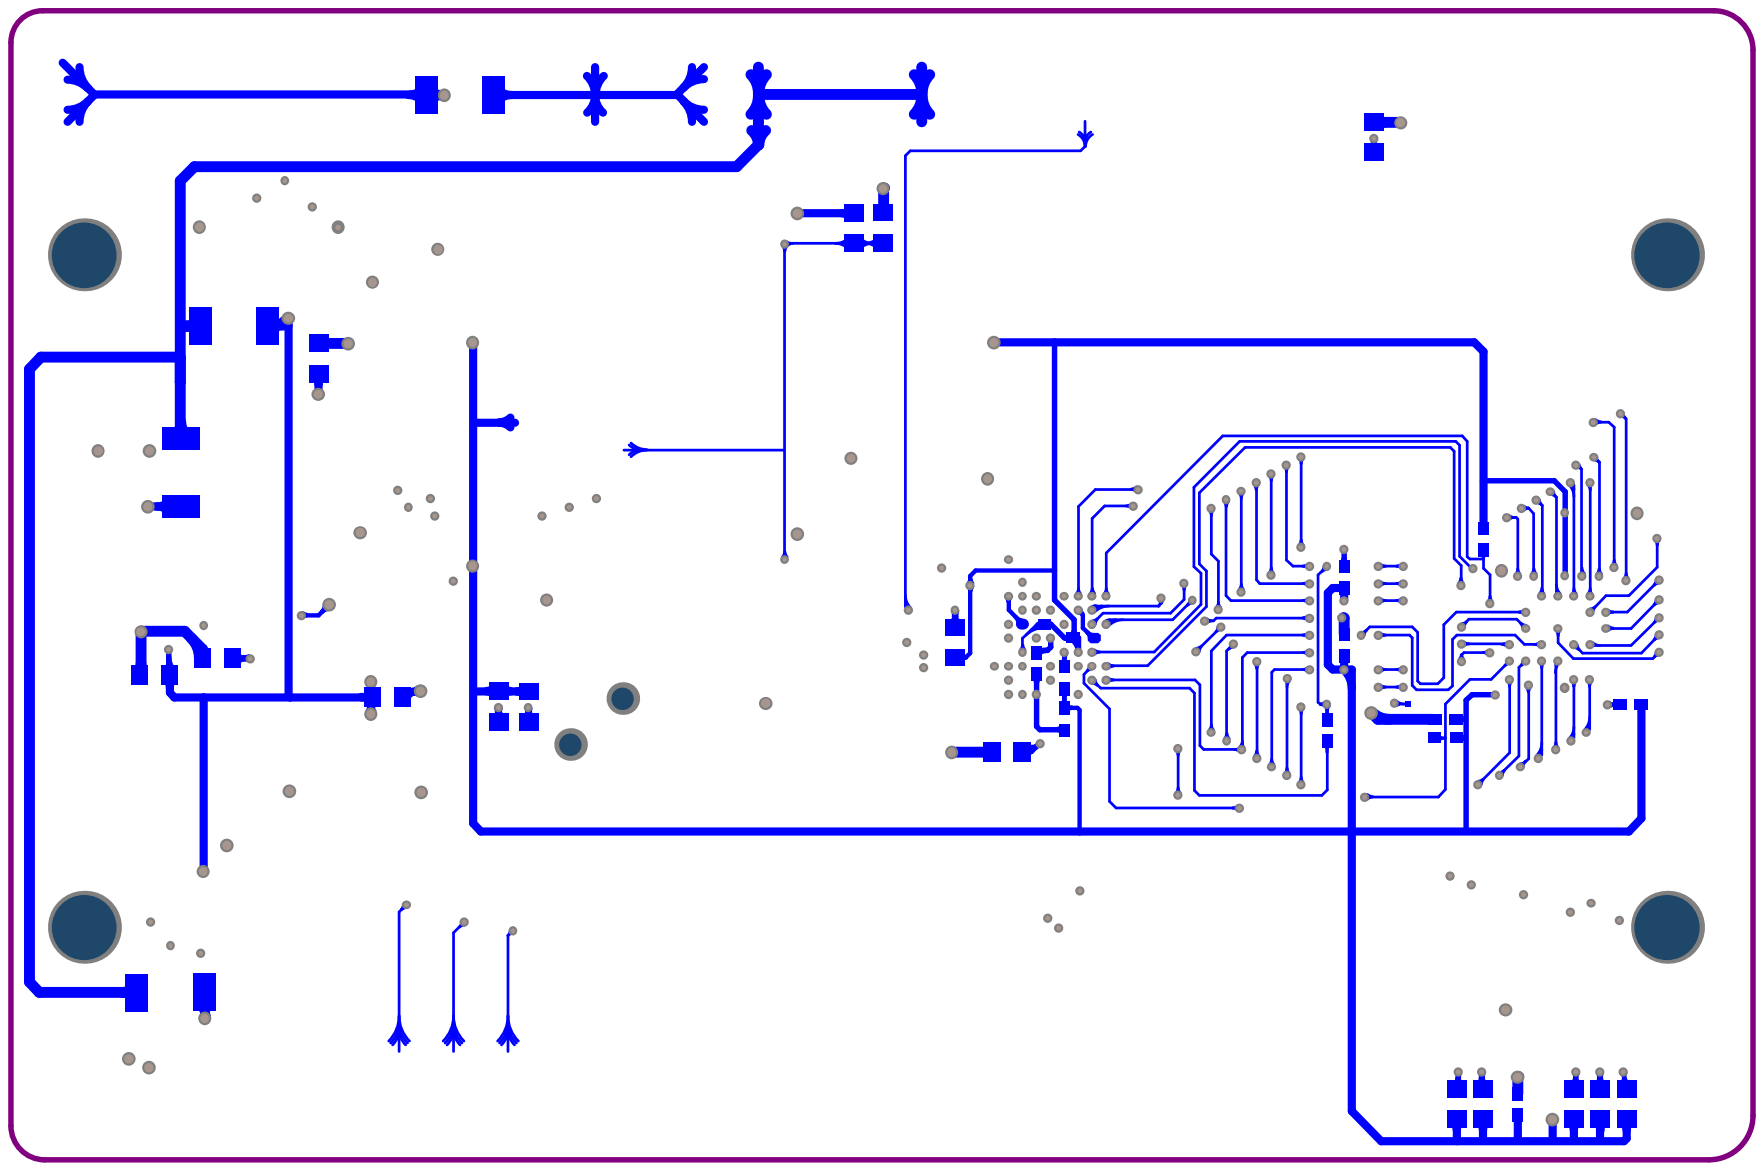
[picture p78: page 12]

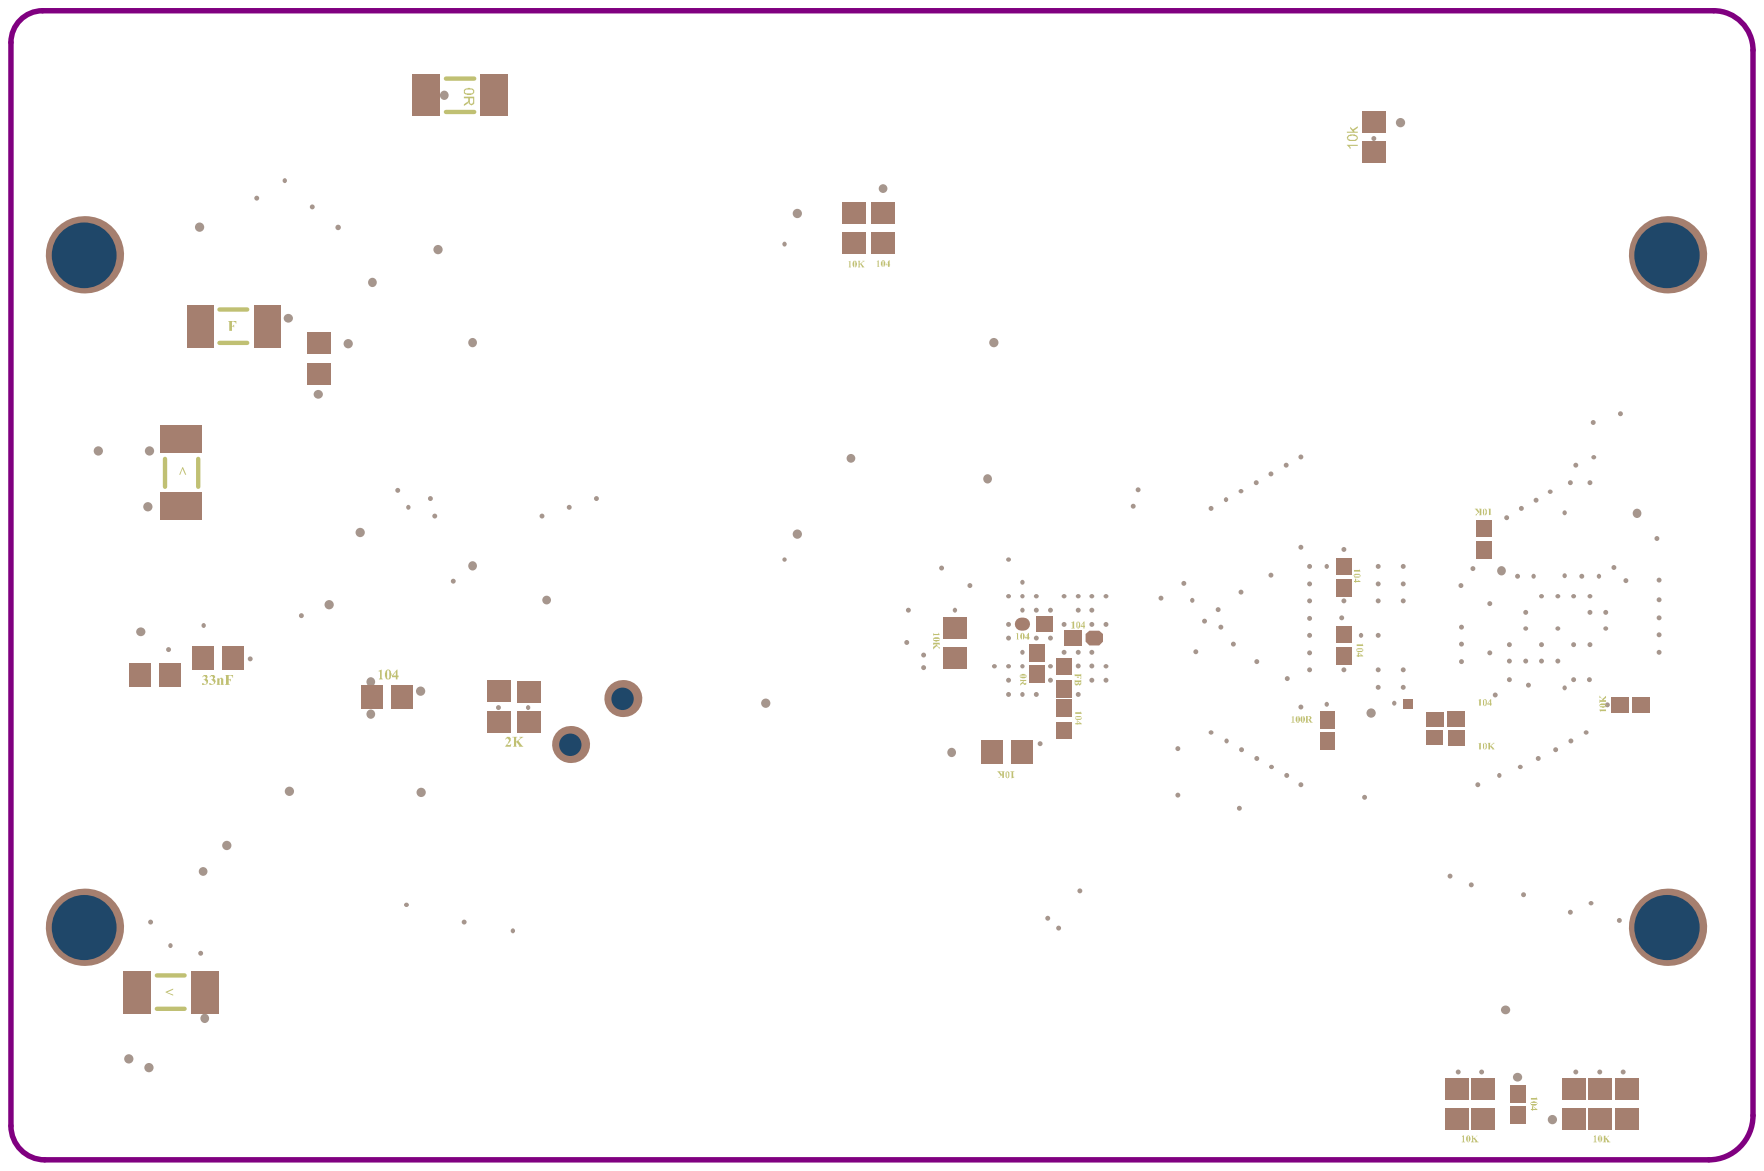
[picture p79: page 13]
