whutddk/MK64F-platform/doc/referDoc/K64-tower/tower-mem/Freescale Tower/TWR-MEM (PWB RevB)/SPF-26248_B.pdf

# Table of Contents

# CF & CPLD

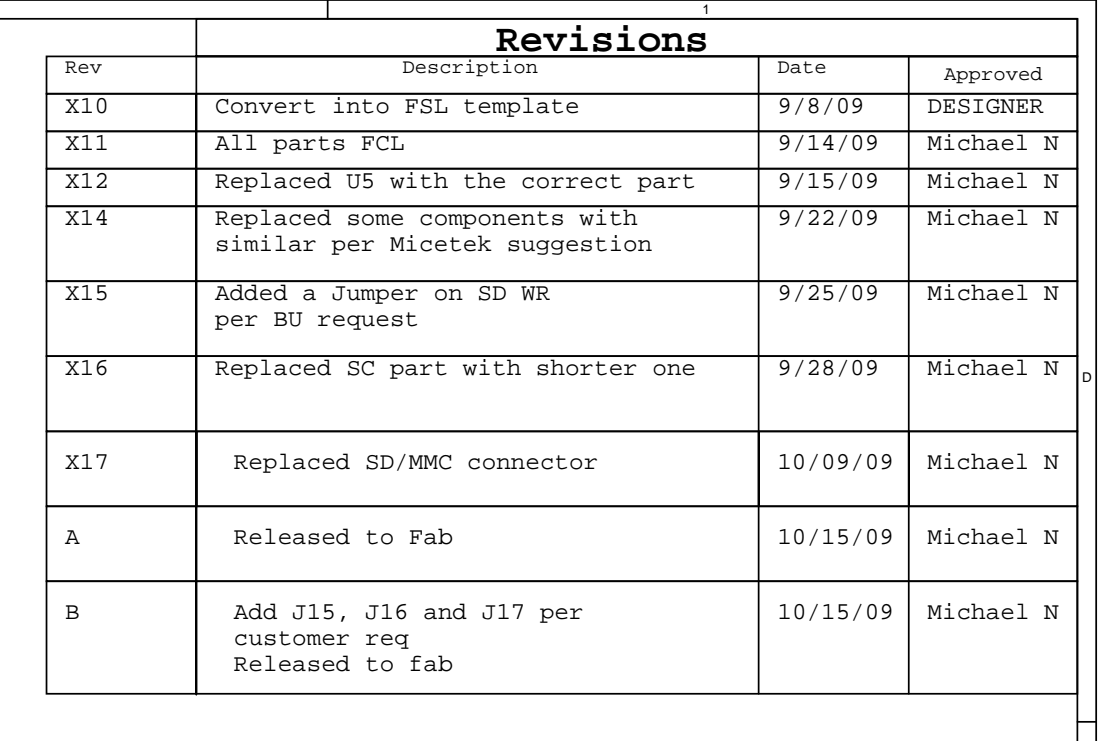
[picture p80: page 1]
Notes; Revisions; Rev; Description; Convert into FSL template; Approved DESIGNER; Date 9/8/09; MRAM, SD & SFLASH; All parts FCL; Michael N 9/14/09; OPTIONAL PORT; Replaced U5 with the correct part; Michael N 9/15/09; Date:; Sheet; ICAP Classification:; FCP:; FIUO:; PUBI:; Wednesday, January 20, 2010

X14 | Replaced some components with similar per Micetek suggestion | 9/22/09 | Michael N

X15 | Added a Jumper on SD WR per BU request | 9/25/09 | Michael N

X16 | Replaced SC part with shorter one | | Michael N 9/28/09

X17 | Replaced SD/MMC connector | 10/09/09 | Michael N

A | Released to Fab | 10/15/09 | Michael N

B | Add J15, J16 and J17 per customer req Released to fab | 10/15/09 | Michael N

Microcontroller Solutions Group

6501 William Cannon Drive West
Austin, TX 78735-8598

This document contains information proprietary to Freescale Semiconductor and shall not be used for
engineering design, procurement or manufacture in whole or in part without the express written permission
of Freescale Semiconductor.

Designer: Designer: Designer: Rodolfo G Rodolfo G Rodolfo G | Drawing Title: Drawing Title: Drawing Title: TWR-MEM TWR-MEM TWR-MEM

Drawn by: Drawn by: Drawn by: Rodolfo G Rodolfo G Rodolfo G | Page Title: Table of contents Table of contents Table of contents

Approved: Approved: Approved: Michael N Michael N Michael N | Size C | Document Number SCH-26248 PDF: SPF-26248 | Rev B

# 1. Unless Otherwise Specified: All resistors are in ohms, 5%, 1/8 Watt

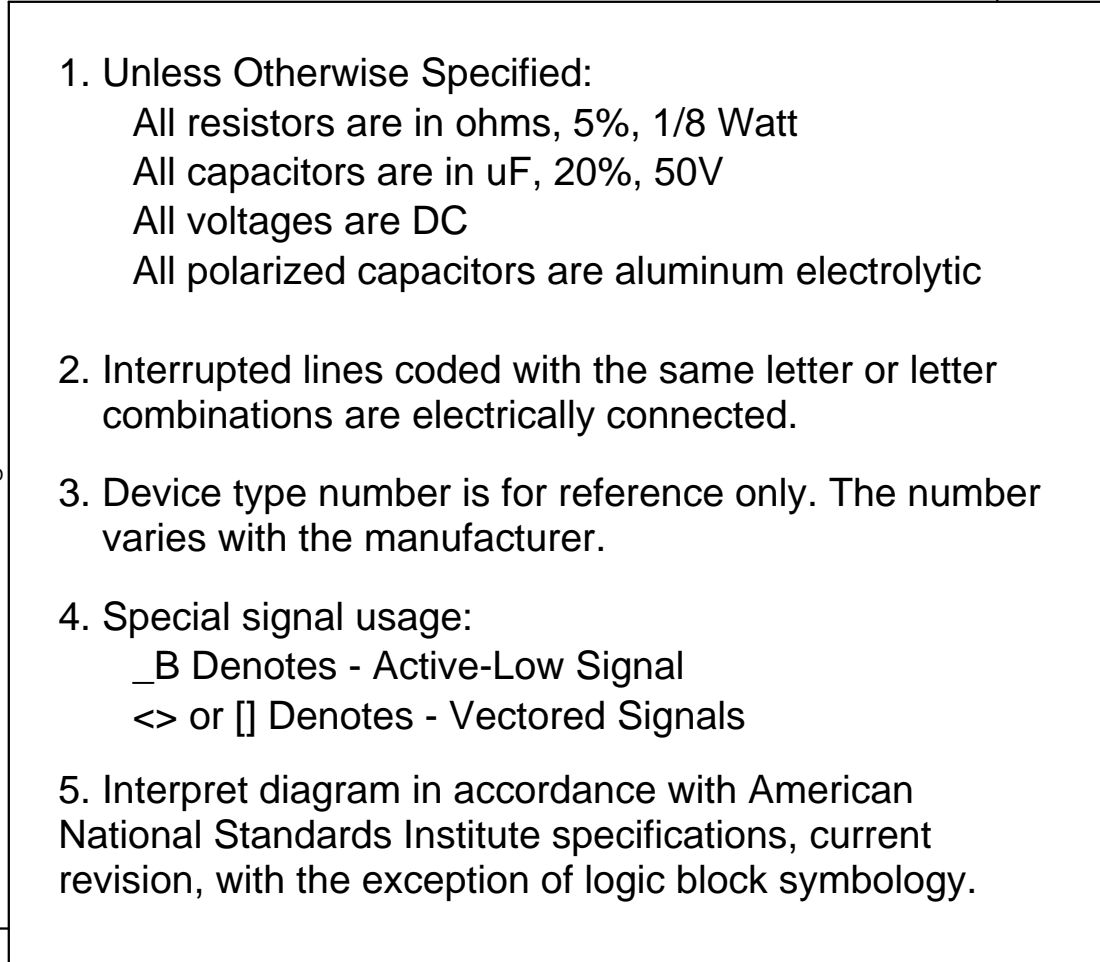
[picture p81: page 2]
Drawing Title:; ICAP Classification:; FCP:; FIUO:; PUBI:; TWR-MEM; NOTES

All capacitors are in uF, 20%, 50V
All voltages are DC
All polarized capacitors are aluminum electrolytic

2. Interrupted lines coded with the same letter or letter
combinations are electrically connected.
3. Device type number is for reference only. The number
varies with the manufacturer.
4. Special signal usage:
_B Denotes - Active-Low Signal
<> or [] Denotes - Vectored Signals
5. Interpret diagram in accordance with American
National Standards Institute specifications, current
revision, with the exception of logic block symbology.

### Default: Shunted

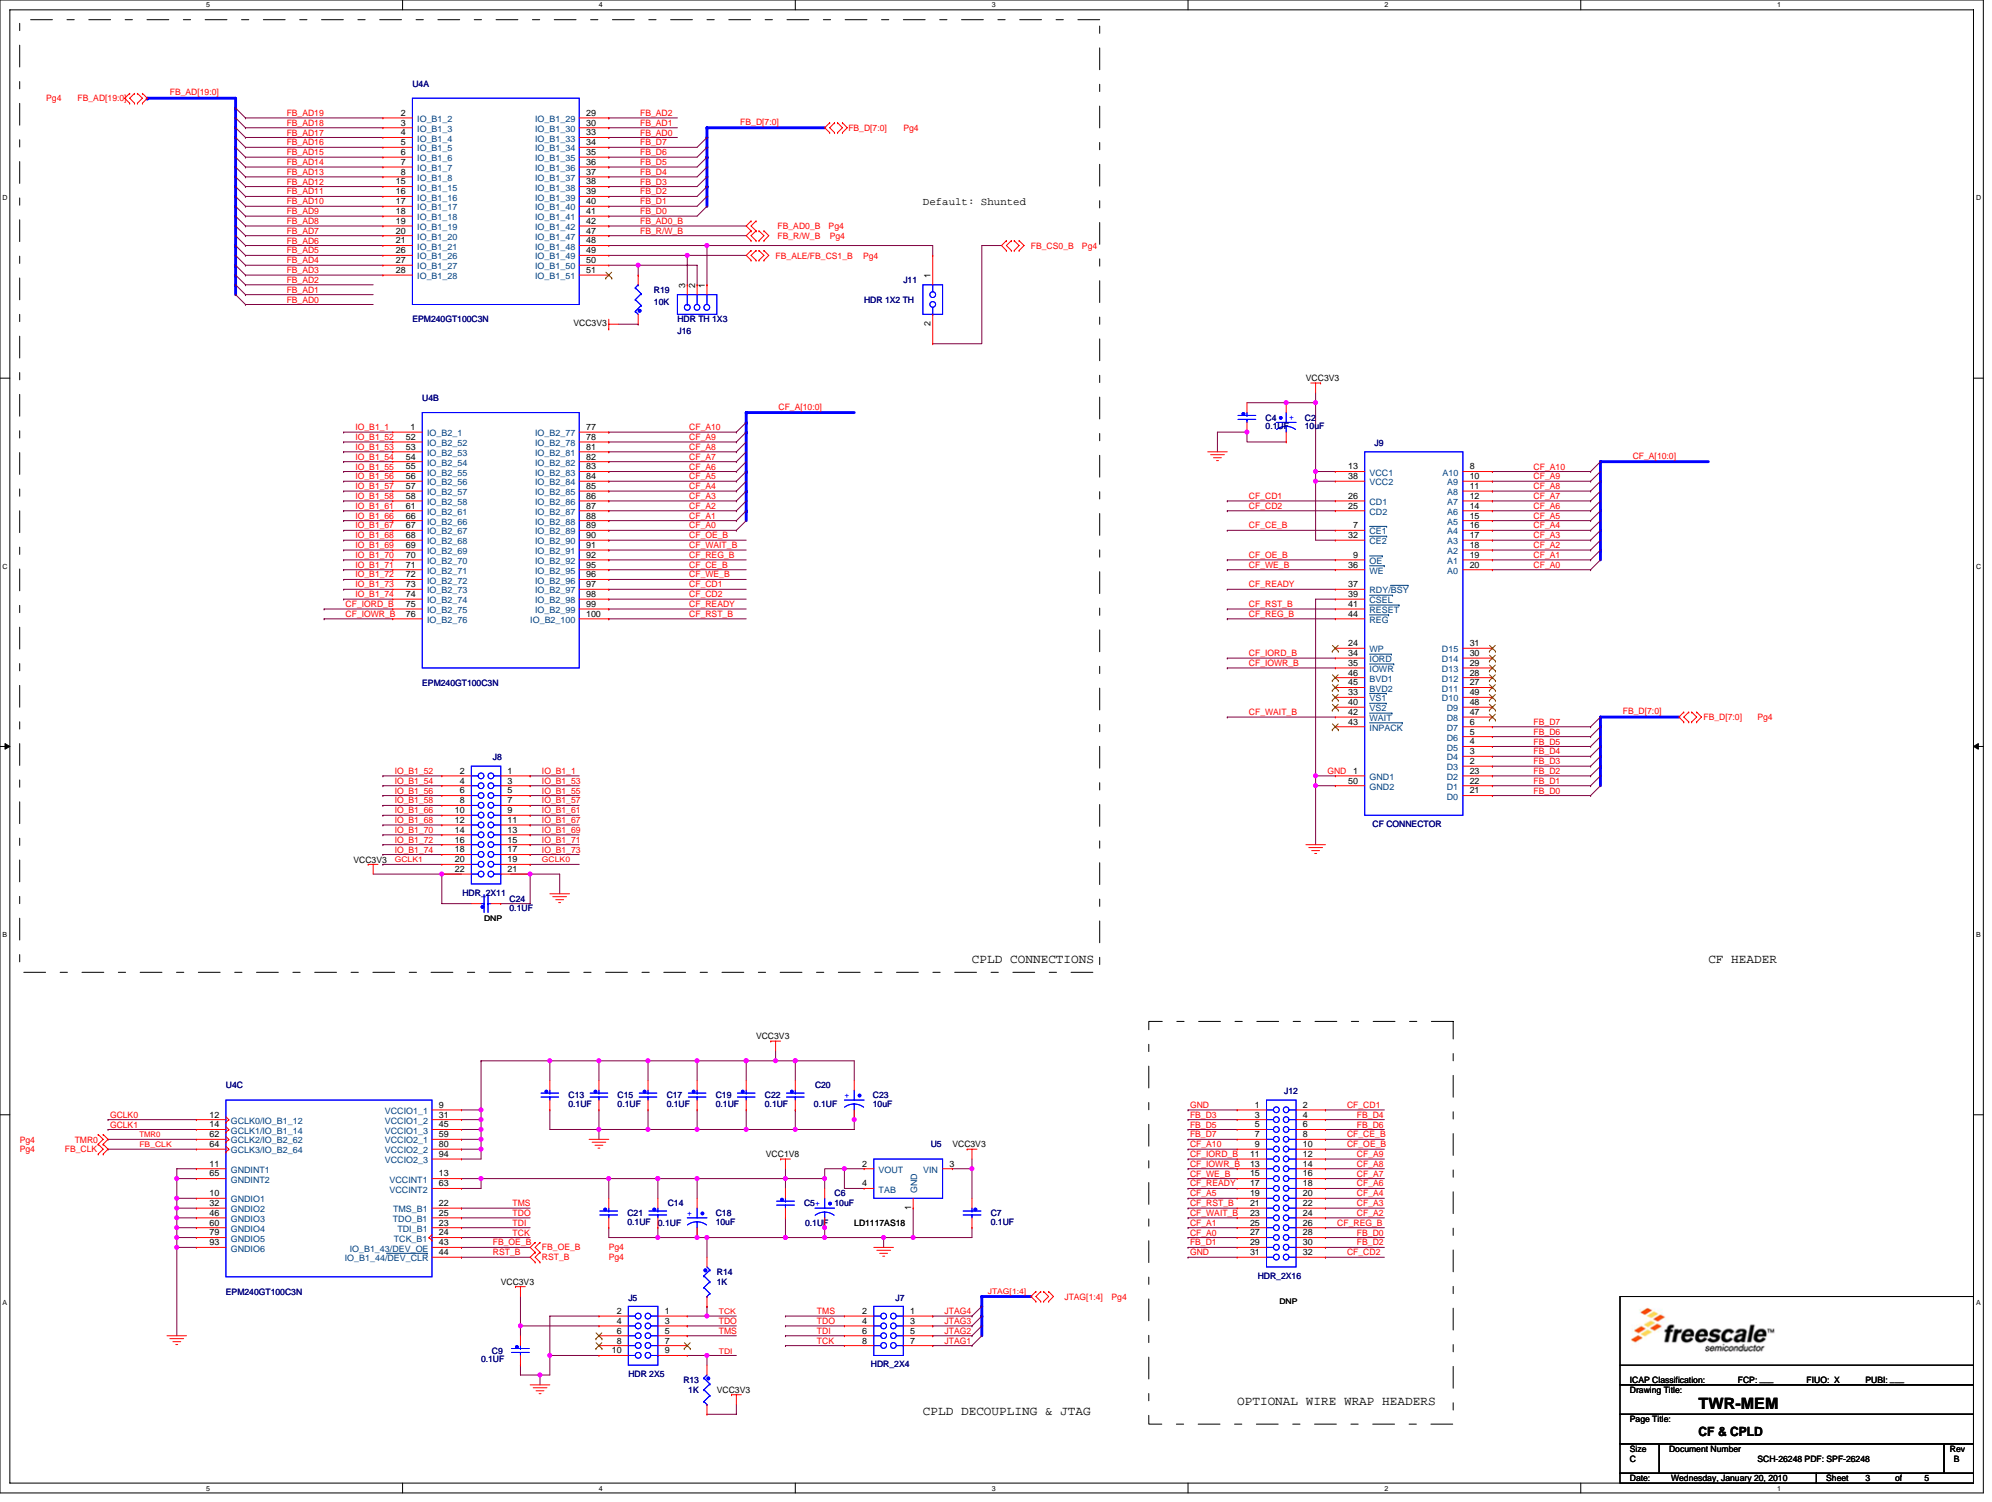
[picture p82: page 3]

OPTIONAL WIRE WRAP HEADERS

### Default: 1,2 Default: Open

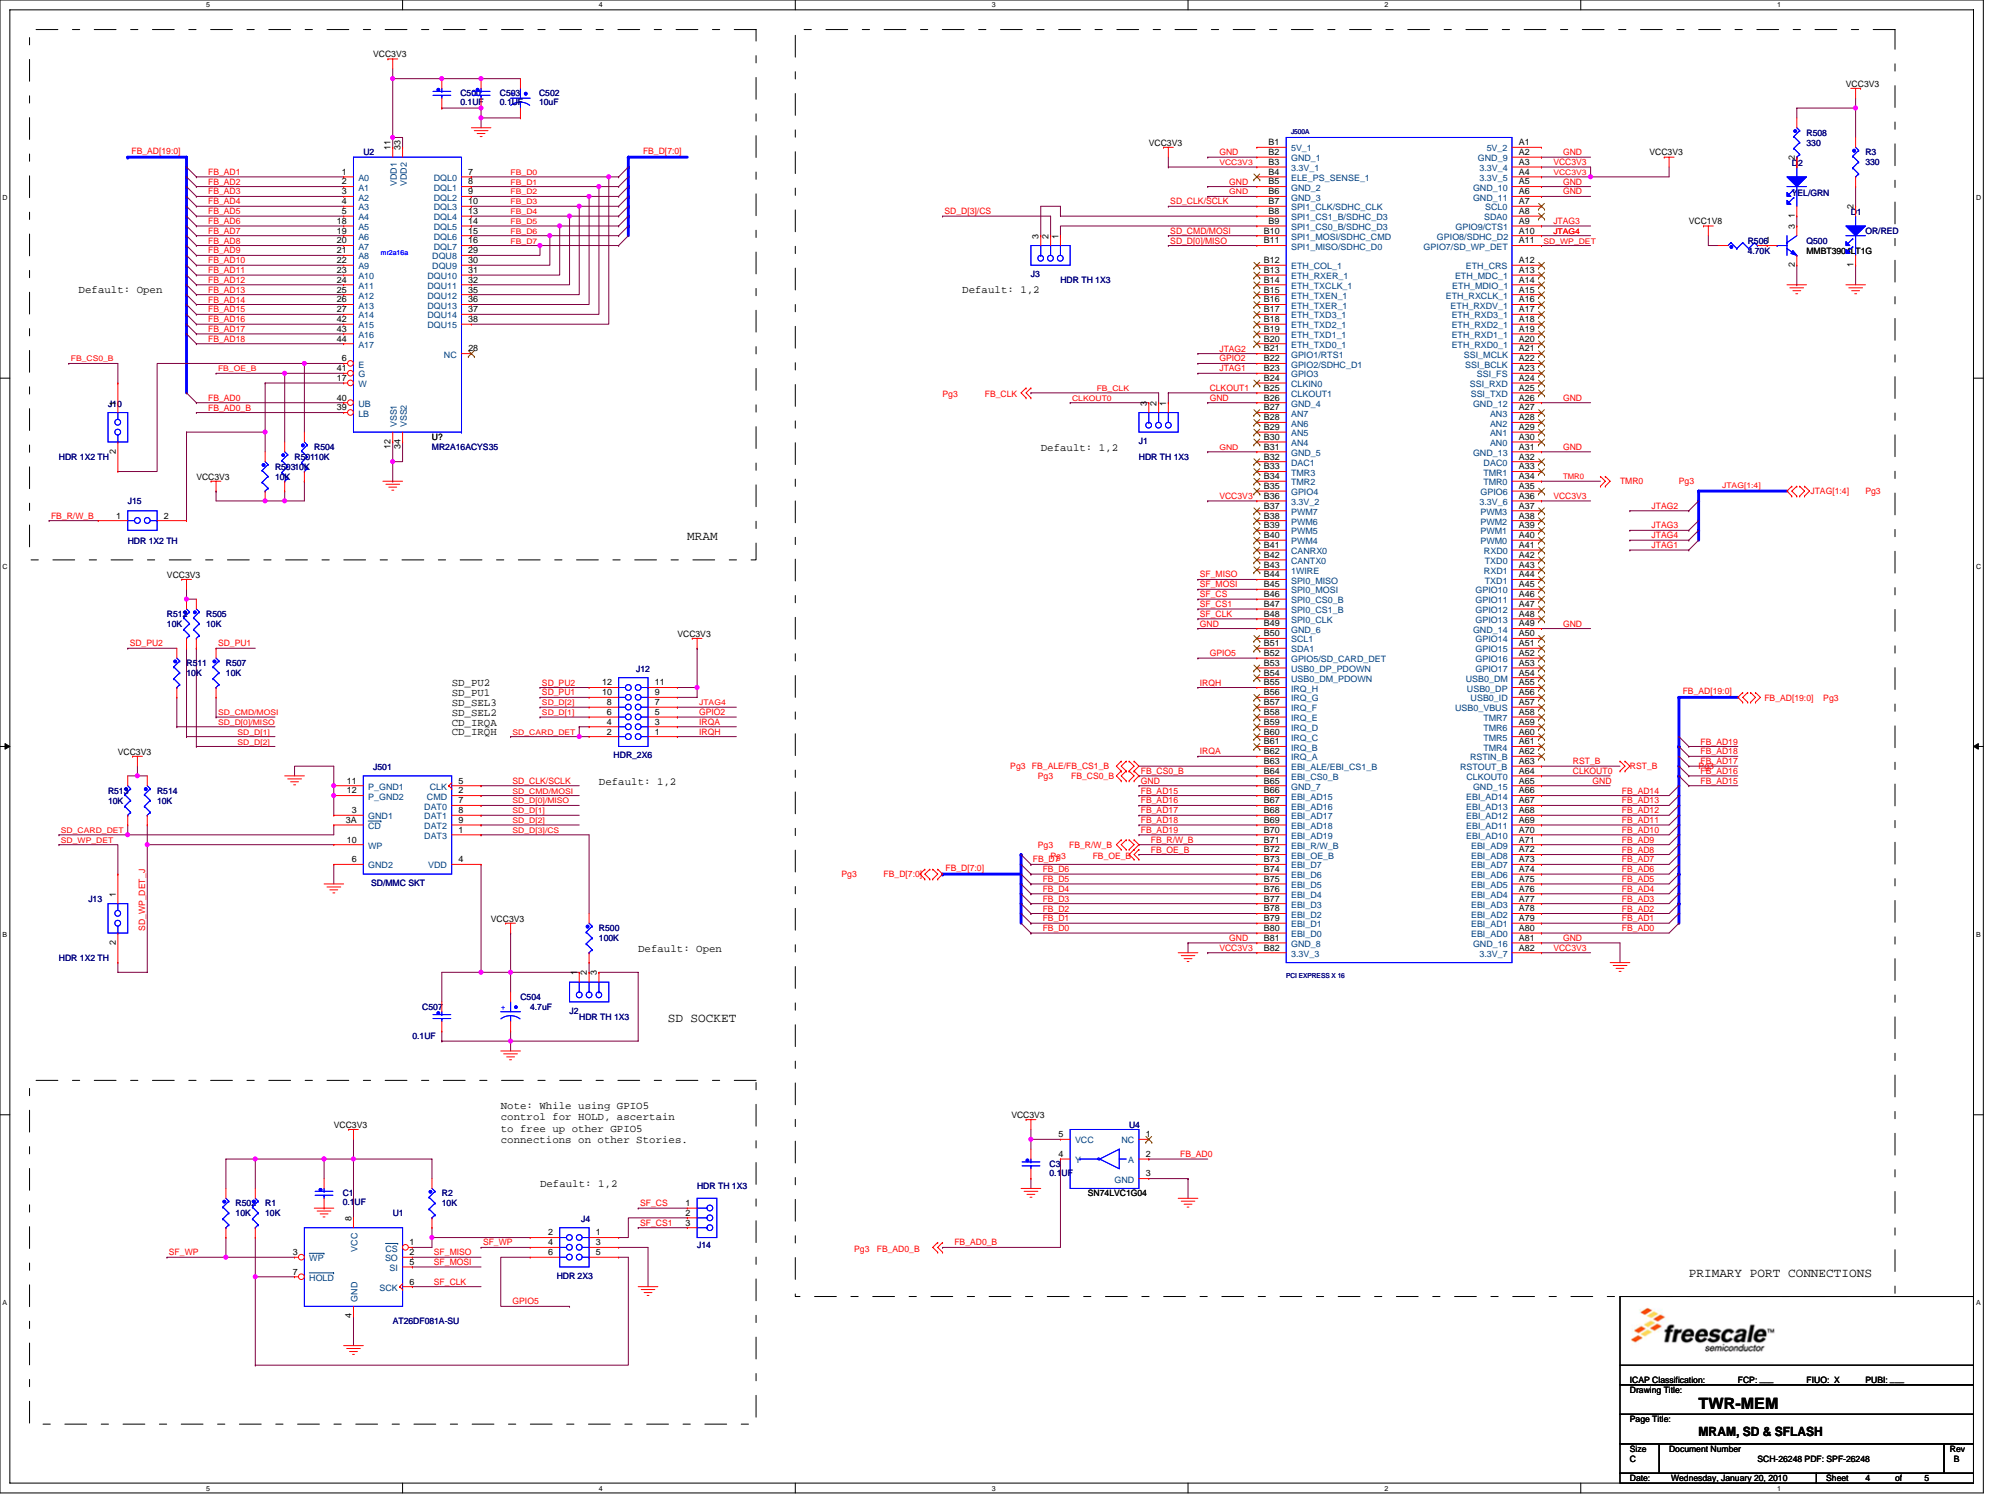
[picture p83: page 4]

Note: While using GPIO5
control for HOLD, ascertain
to free up other GPIO5
connections on other Stories.

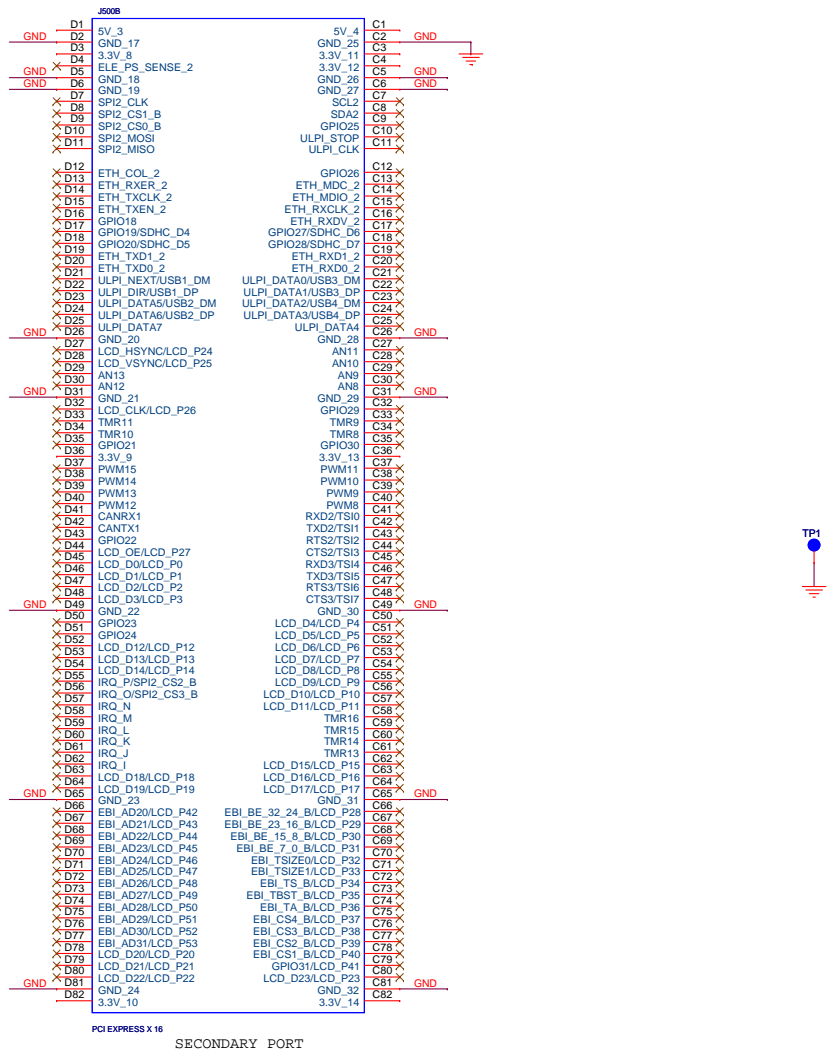
[picture p84: page 5]
