whutddk/MK64F-platform/outputFile/pre-release-version/0-2-FT2232-Jtag.PDF

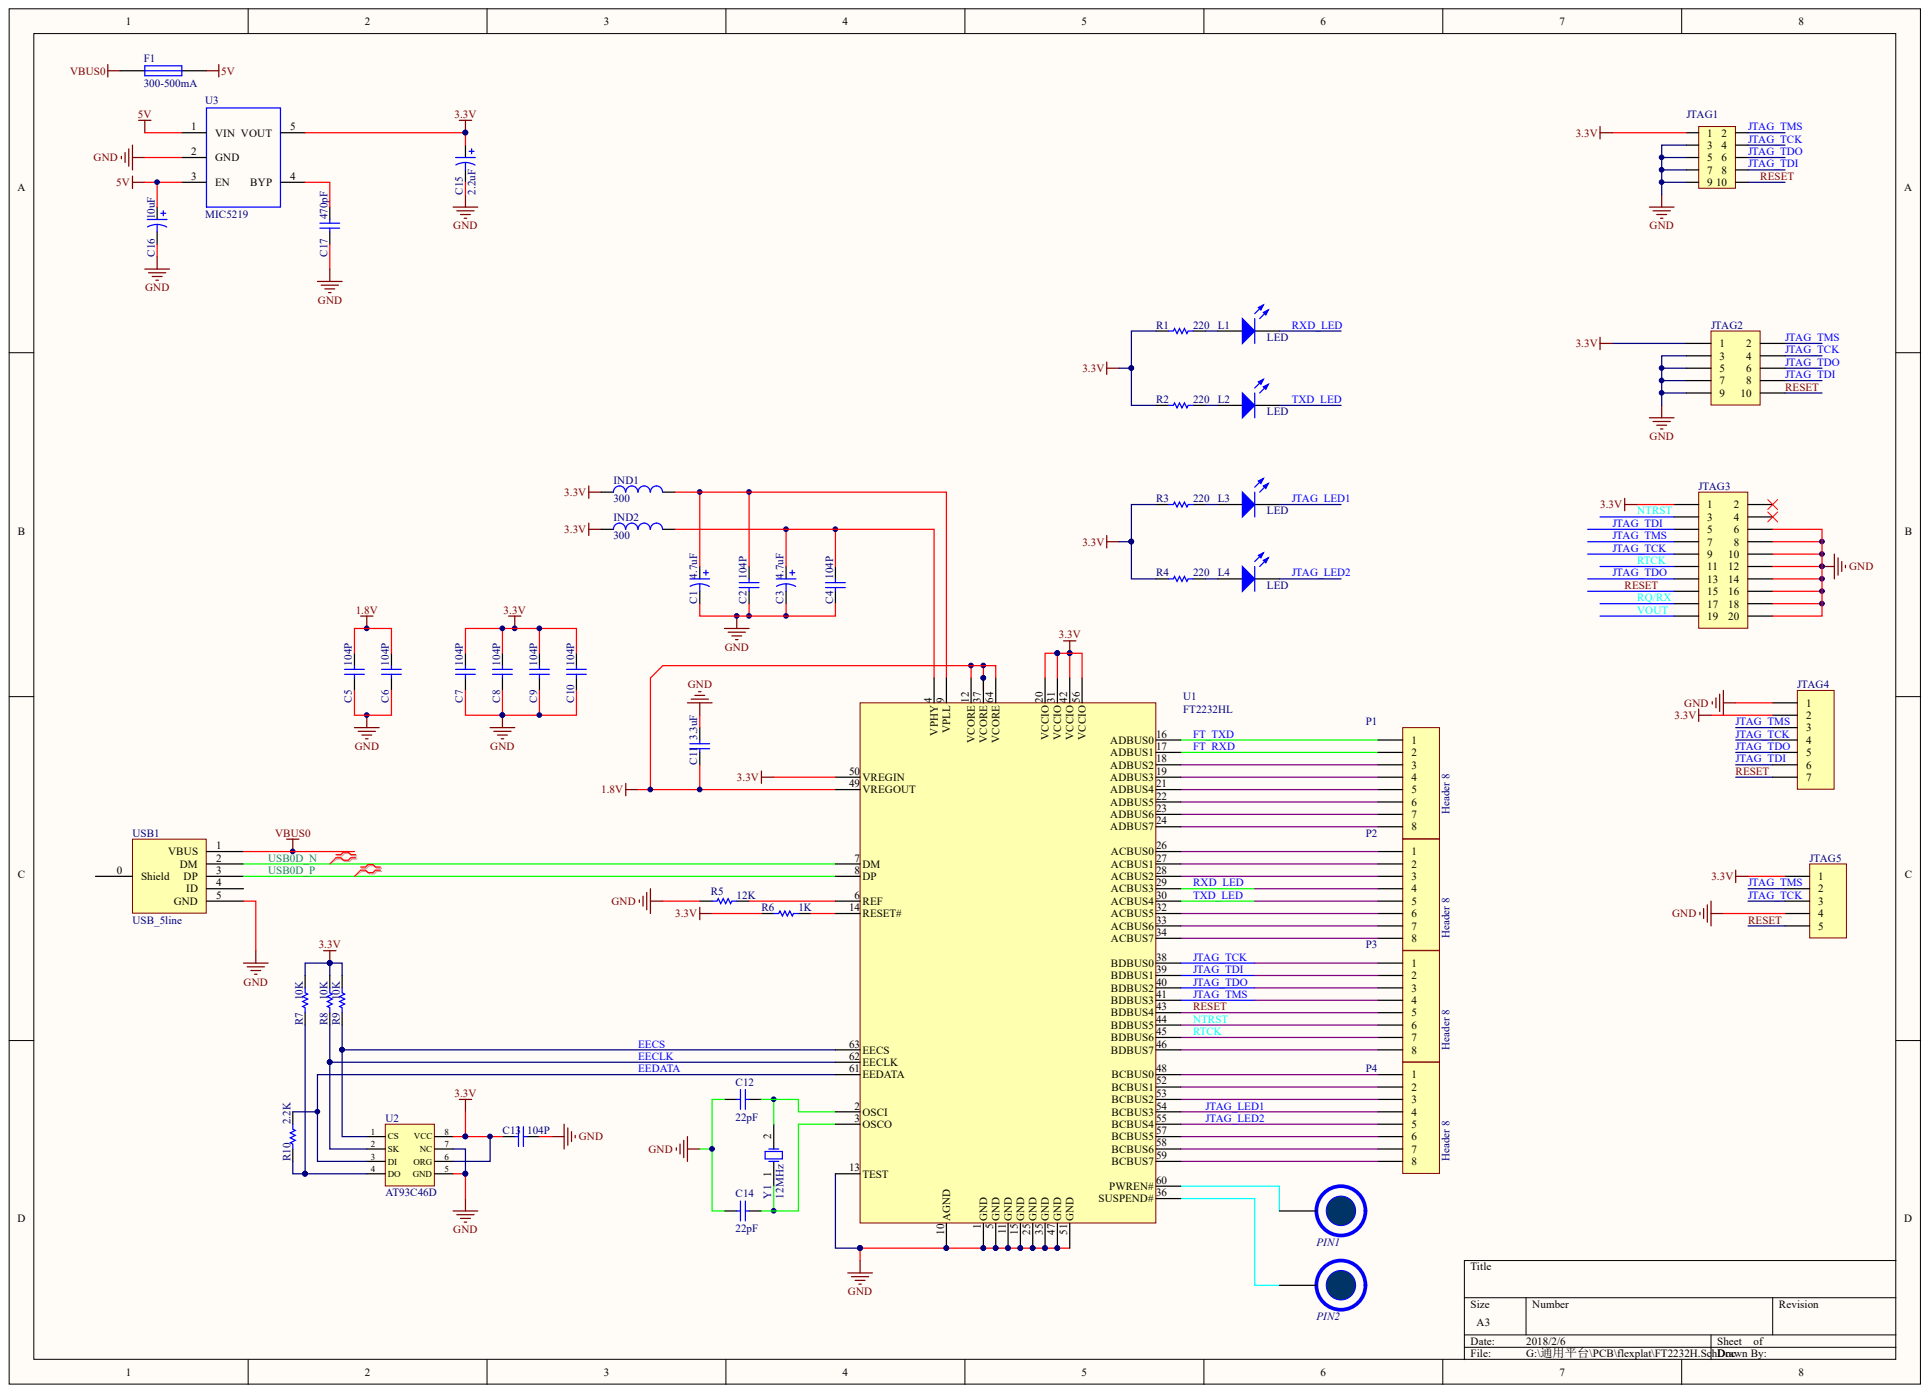
[picture p96: page 1]

OSCI 2
OSCO 3 | JTAG_LED2

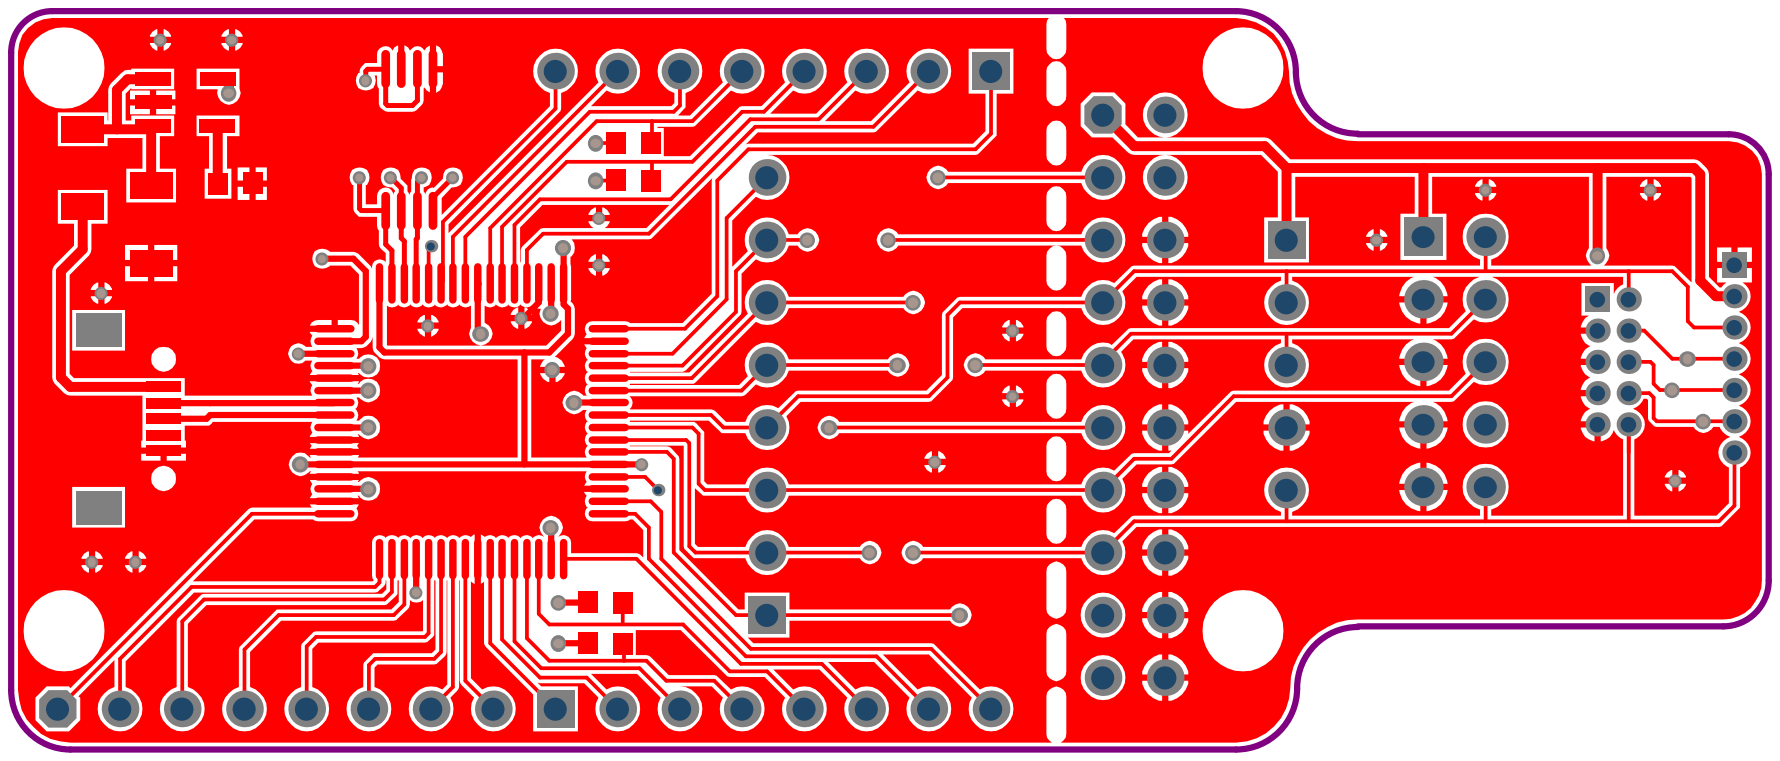
[picture p97: page 2]

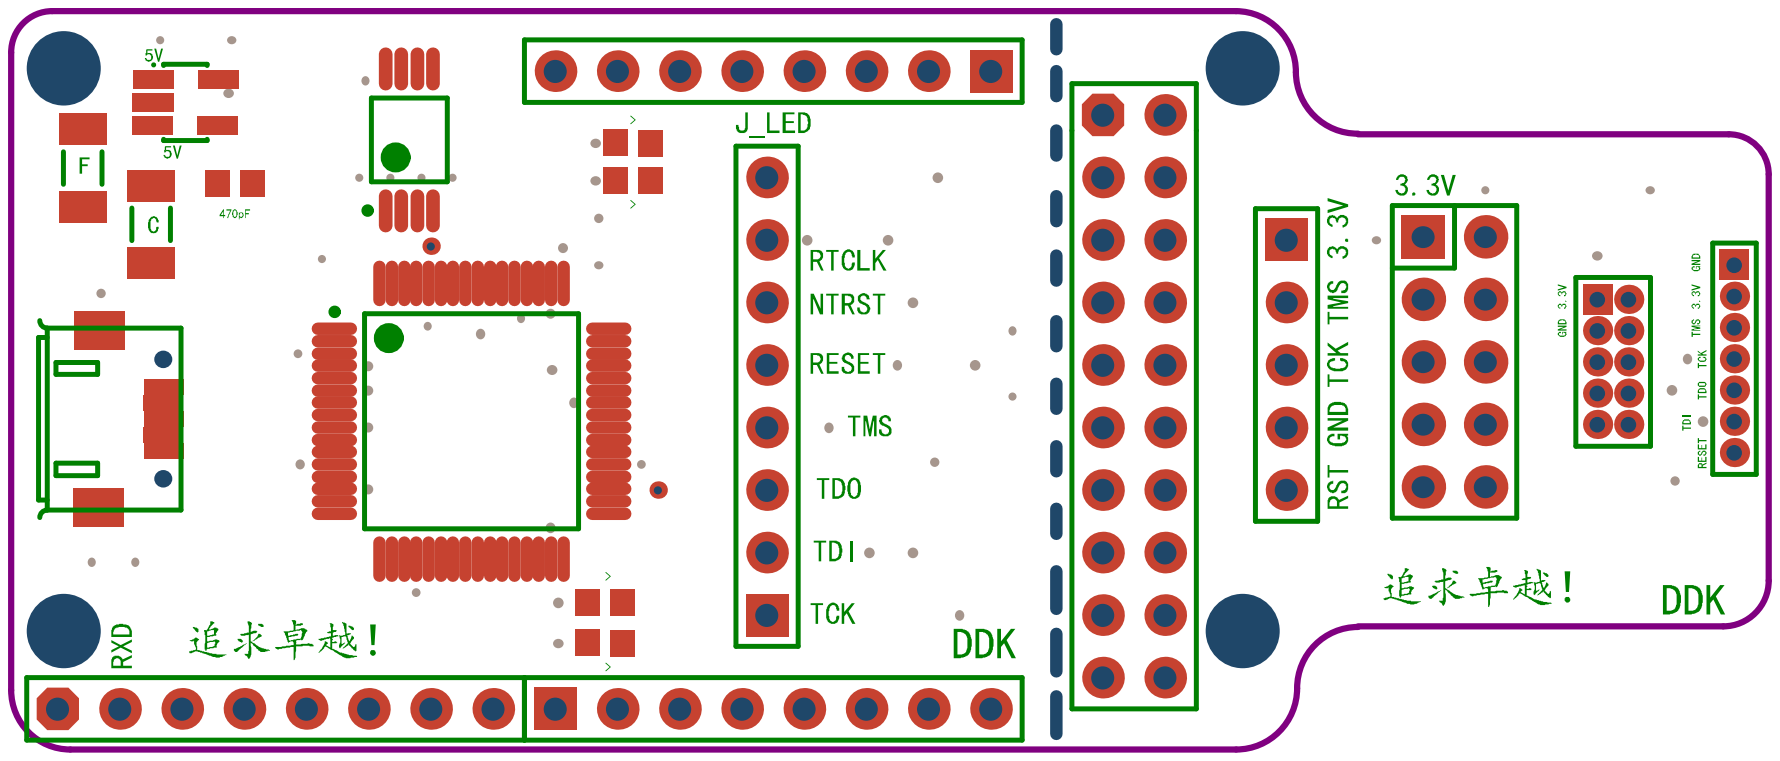
[picture p98: page 3]

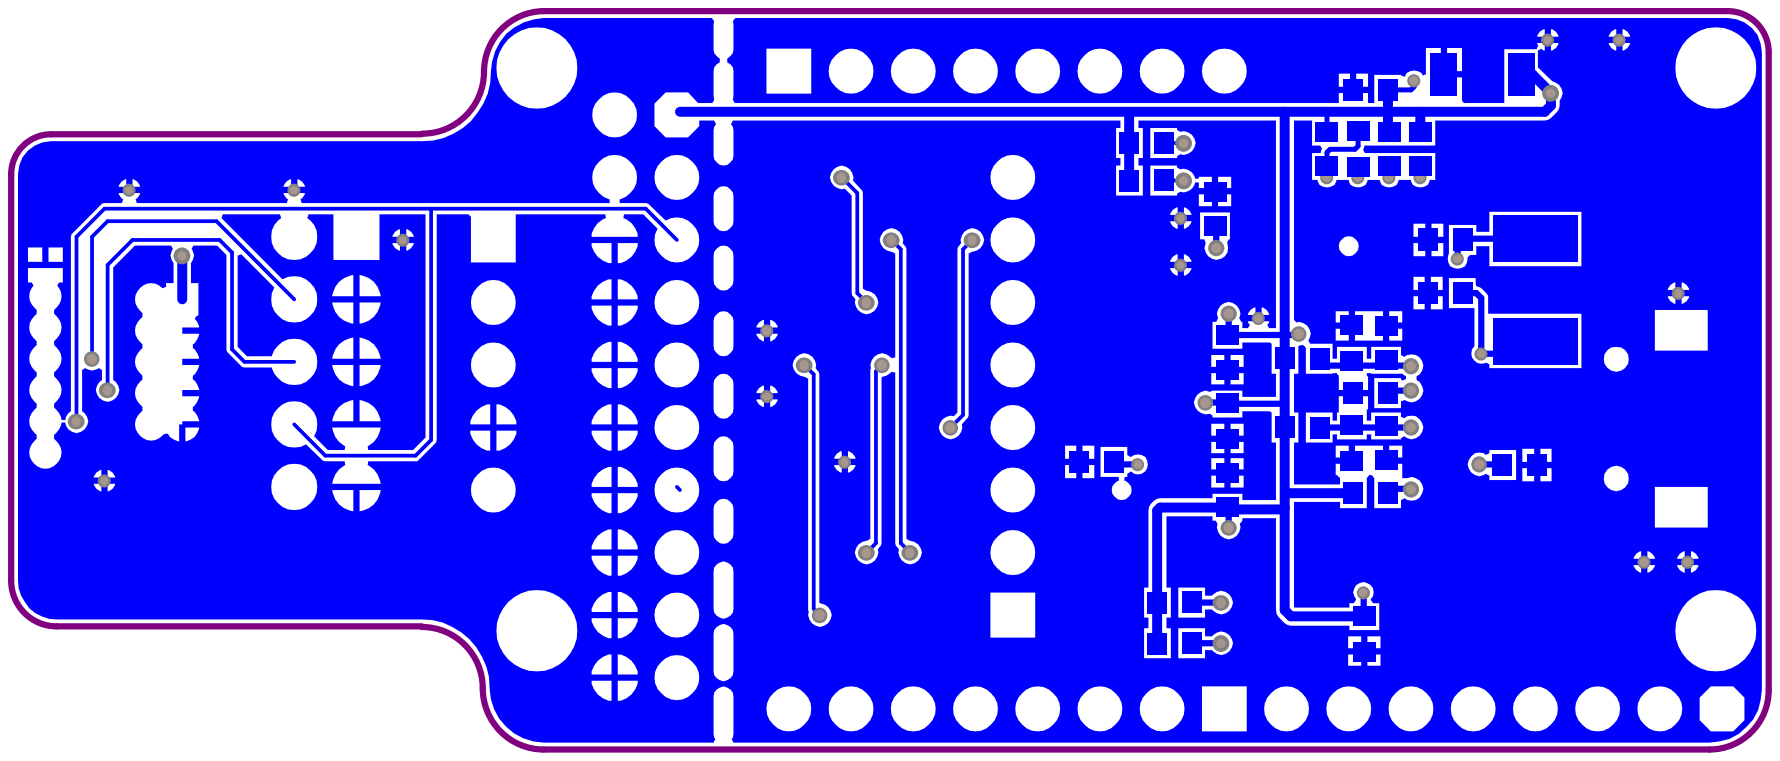
[picture p99: page 4]

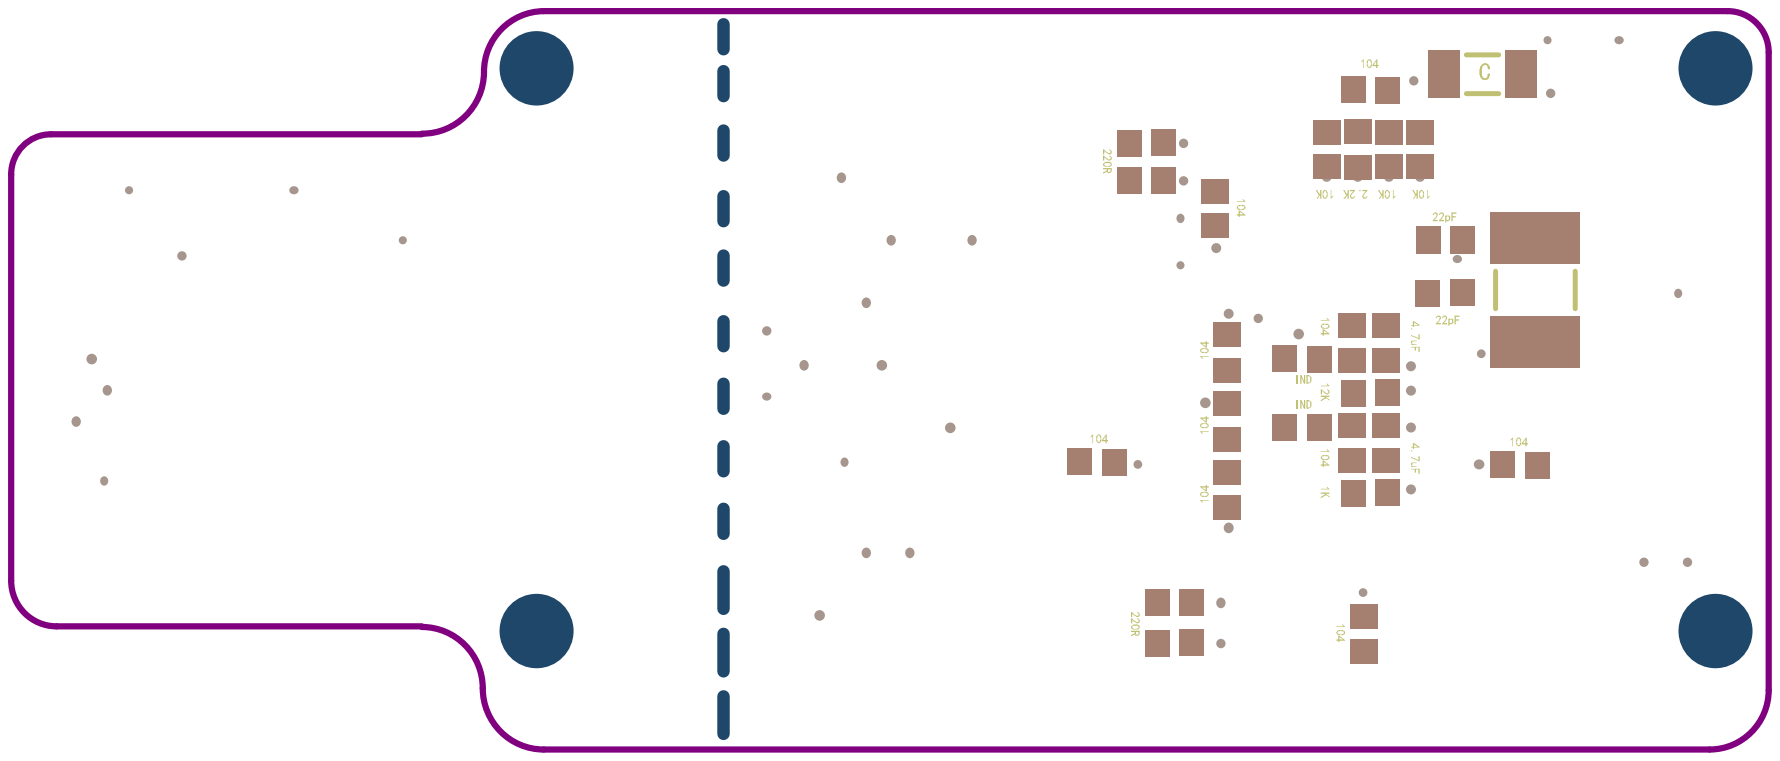
[picture p100: page 5]
