whutddk/MK64F-platform/doc/referDoc/ARM+FPGA/c-mod_c295_sch.pdf

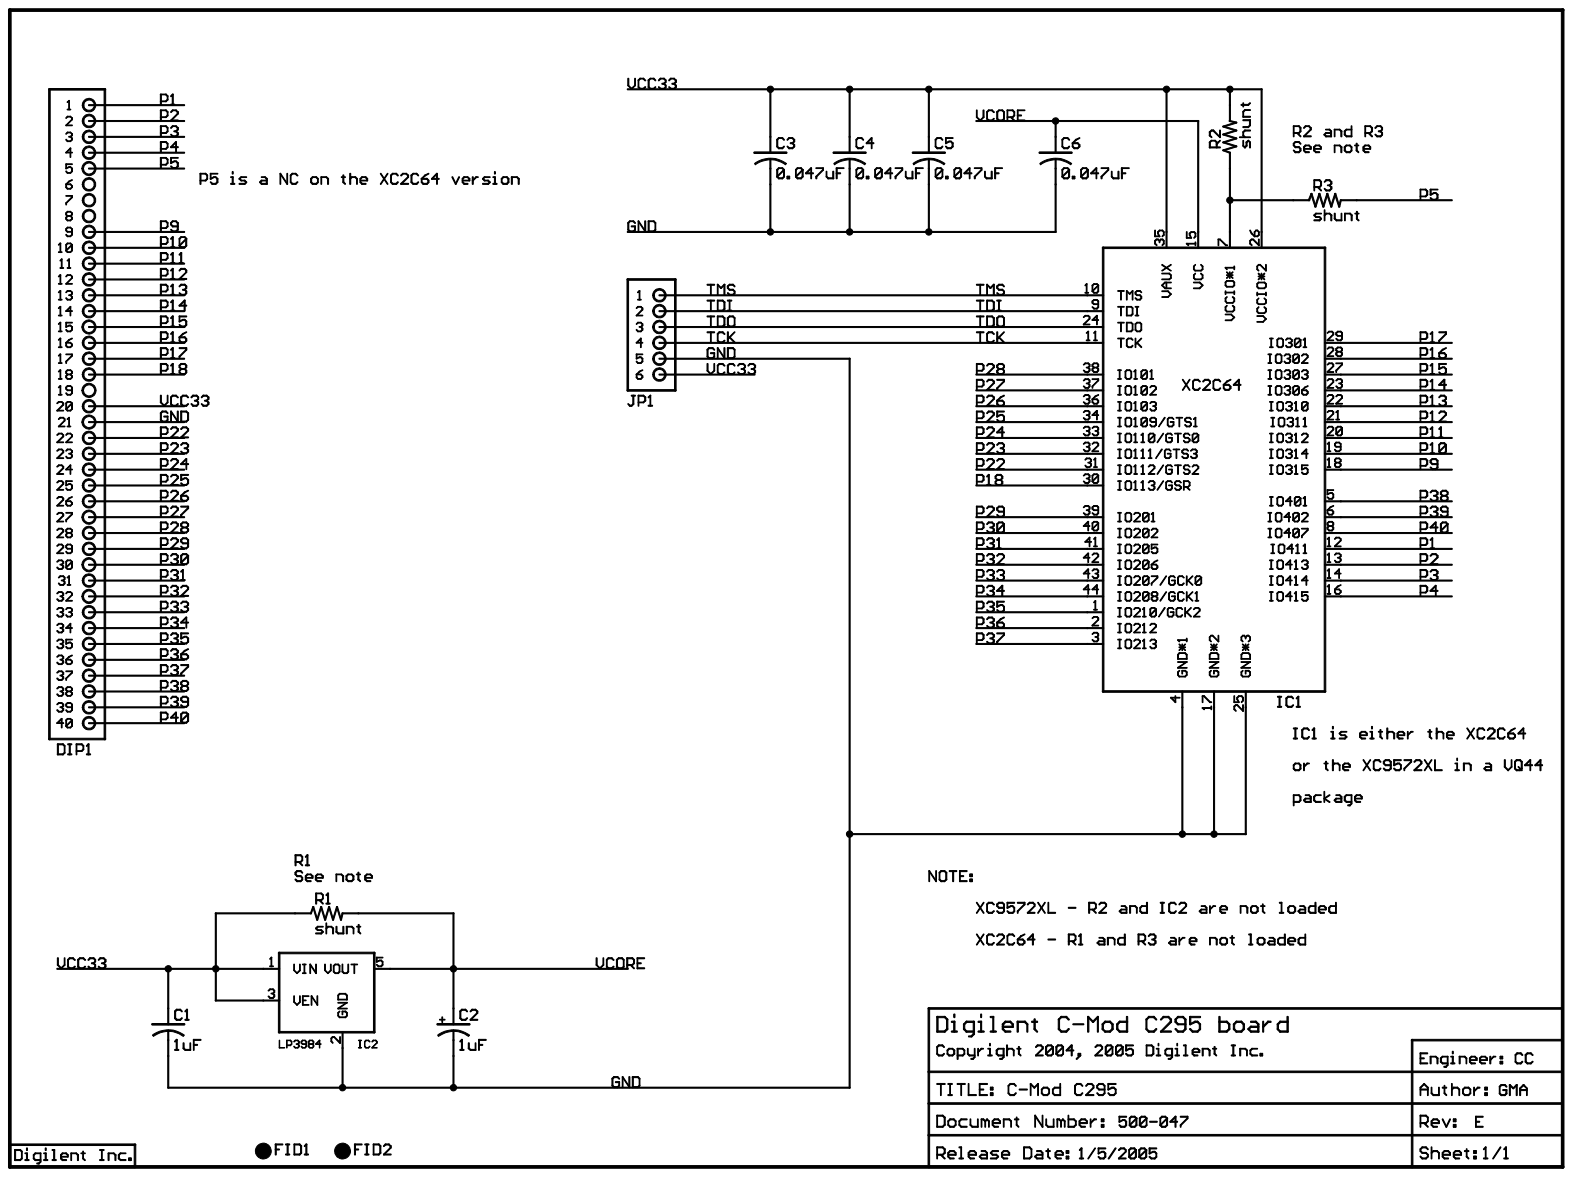
[picture p101: page 1]
