whutddk/MK64F-platform/doc/referDoc/K64-tower/TWRFS.pdf

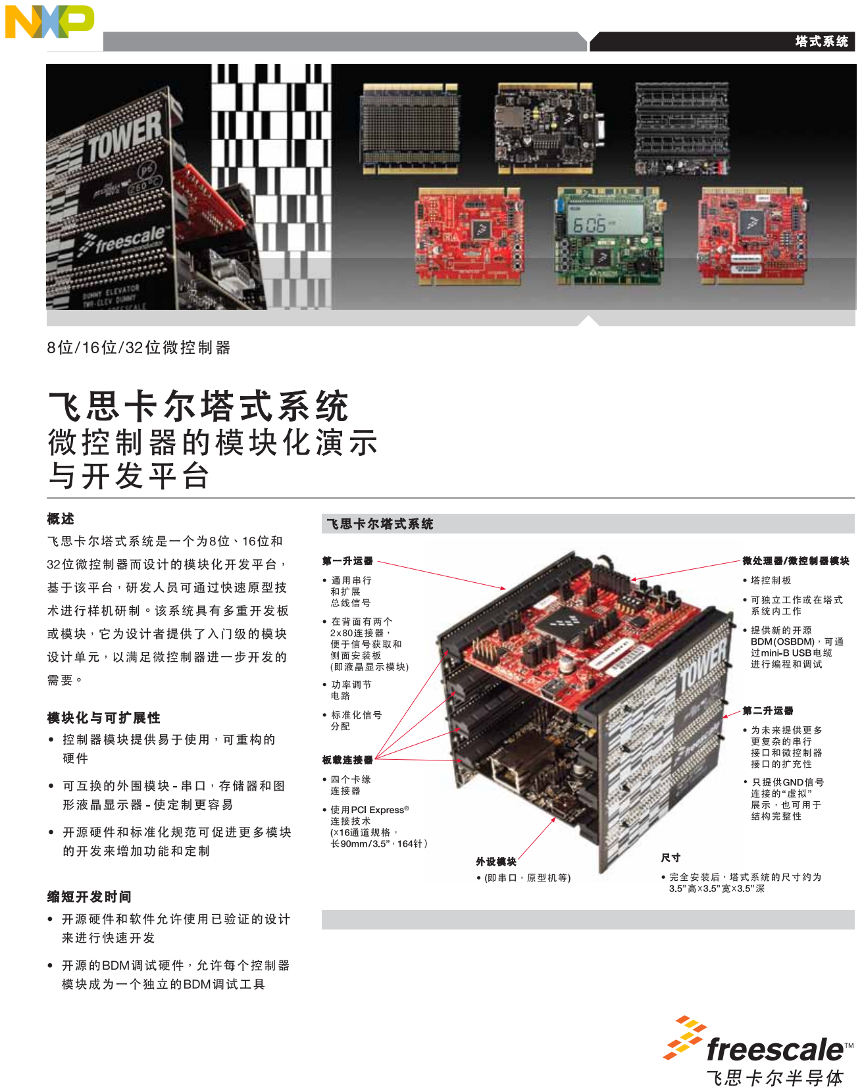
[picture p102: page 1]

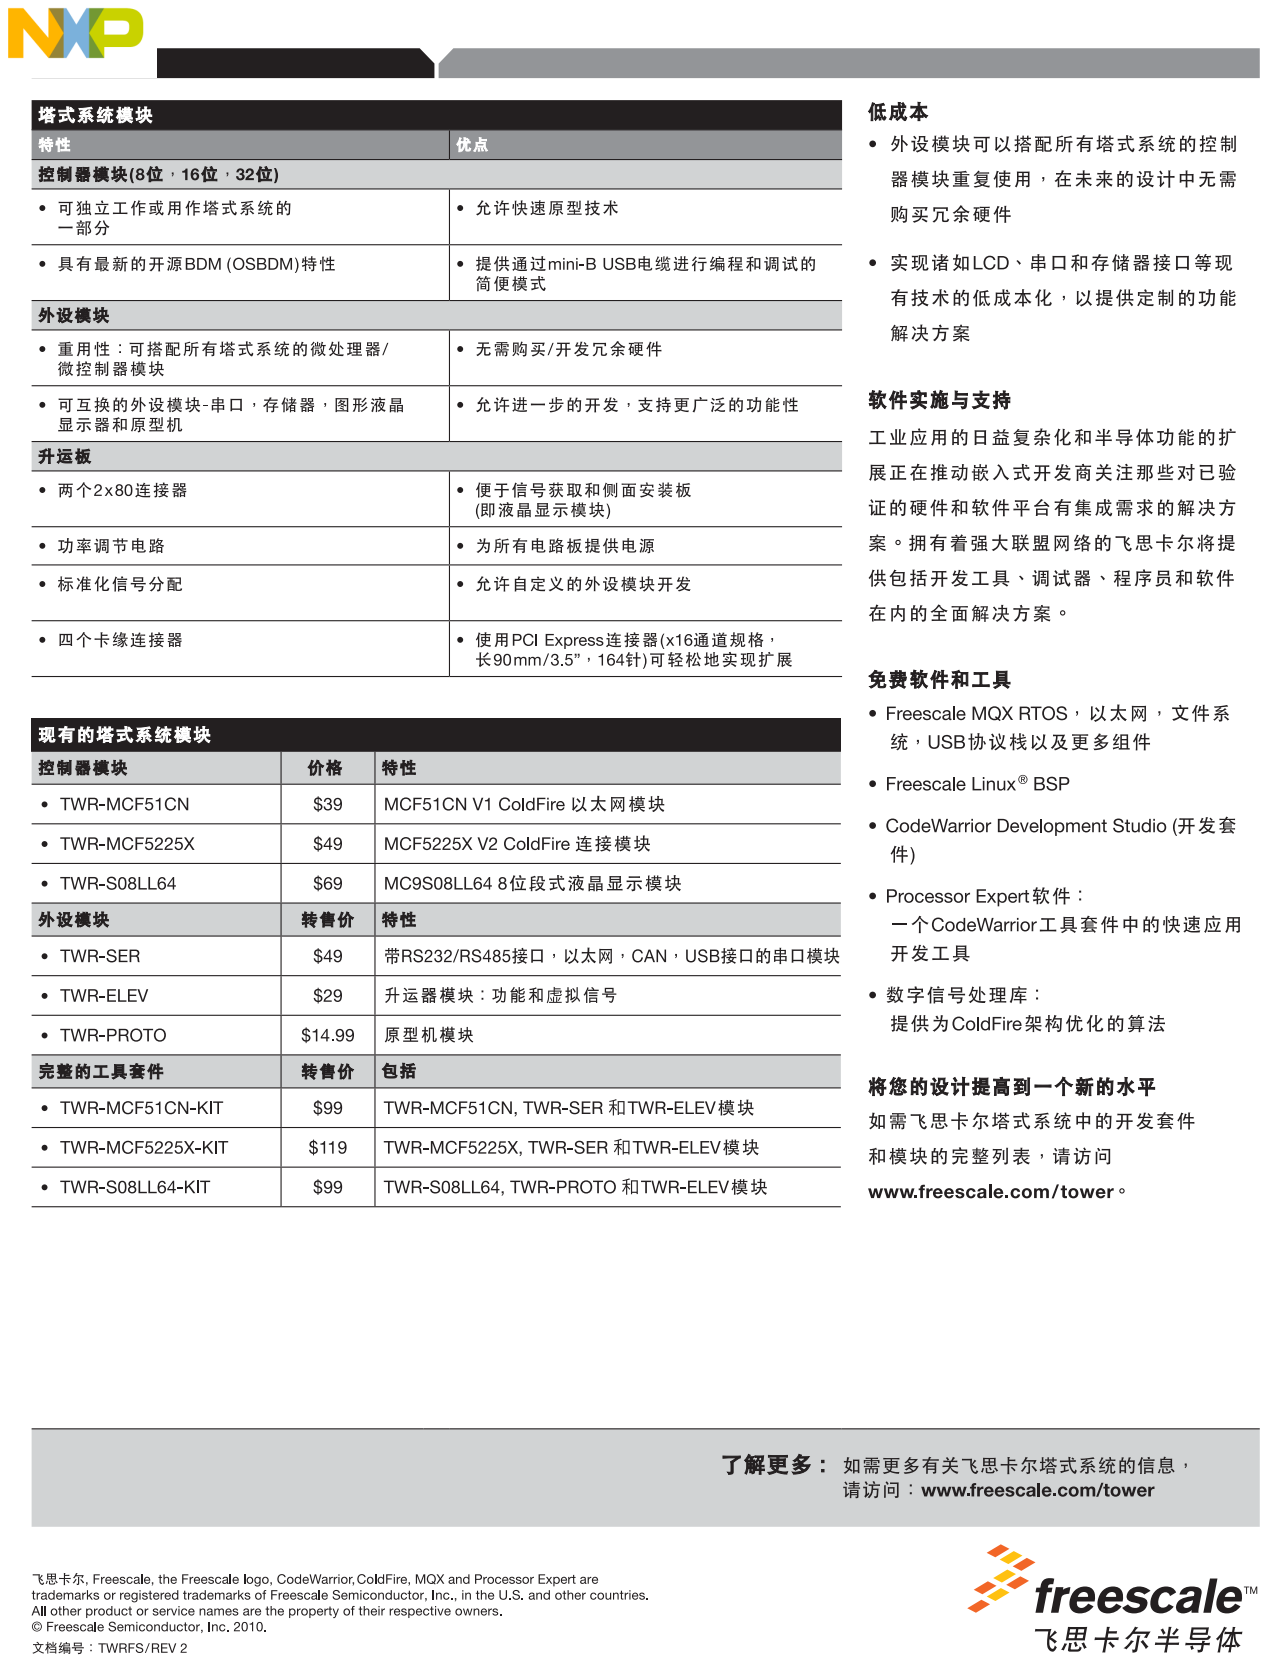
[picture p103: page 2]
