whutddk/MK64F-platform/doc/referDoc/K64-tower/TWR-ELEV Primary (700-26006 RevC)/FAB-26006_F.pdf

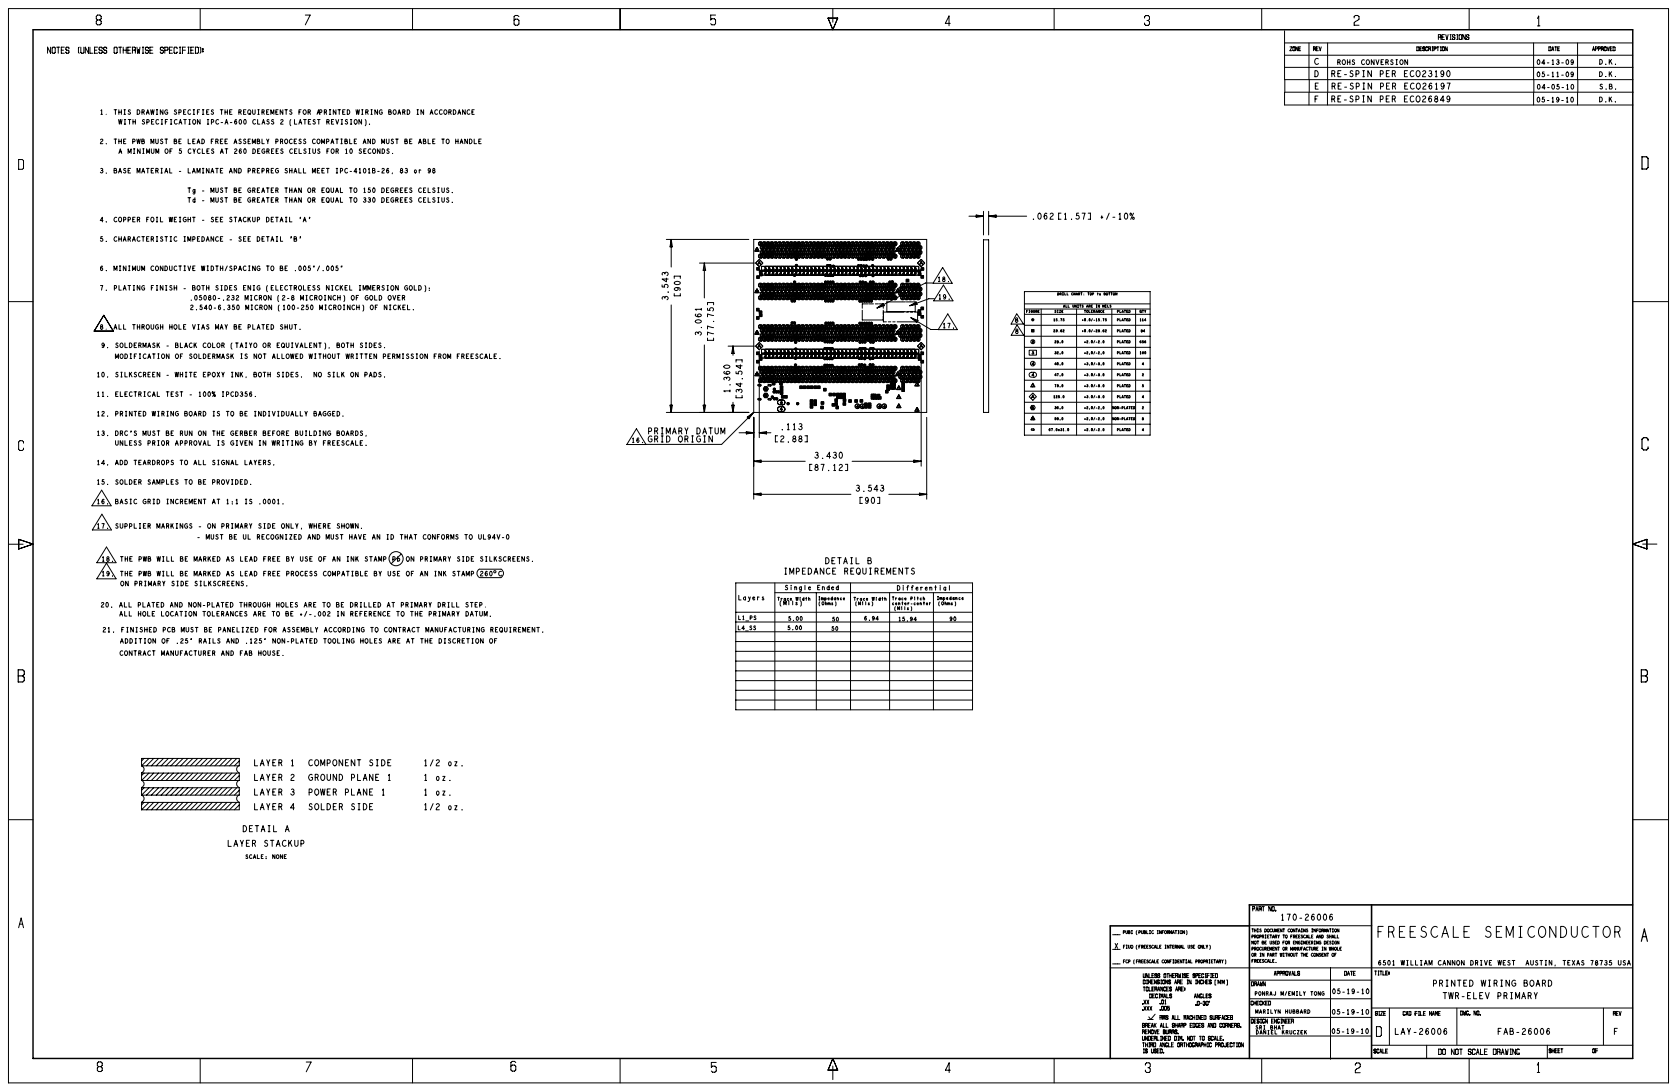
[picture p104: page 1]
