whutddk/MK64F-platform/doc/referDoc/K64-tower/TWR-ELEV Secondary (700-26493 RevA)/FAB-26493_A.pdf

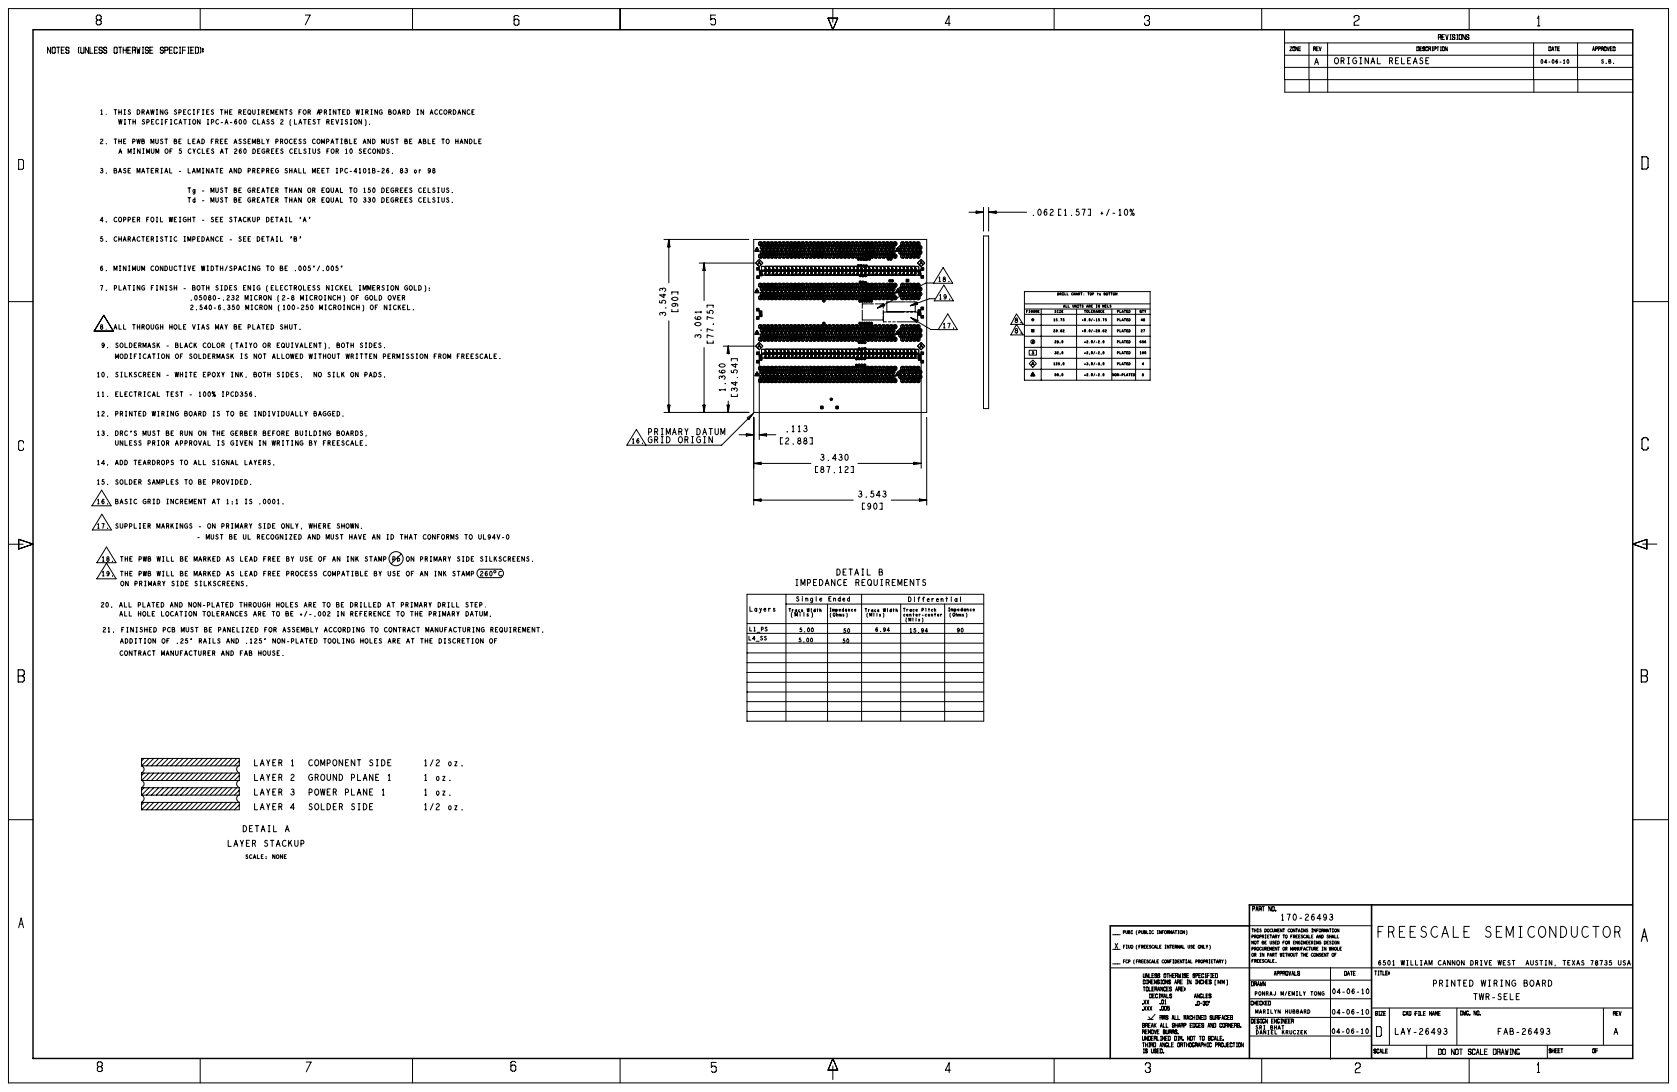
[picture p105: page 1]
