whutddk/MK64F-platform/PCB/pre-release-version/abort-version/1.6.1/connect.PDF

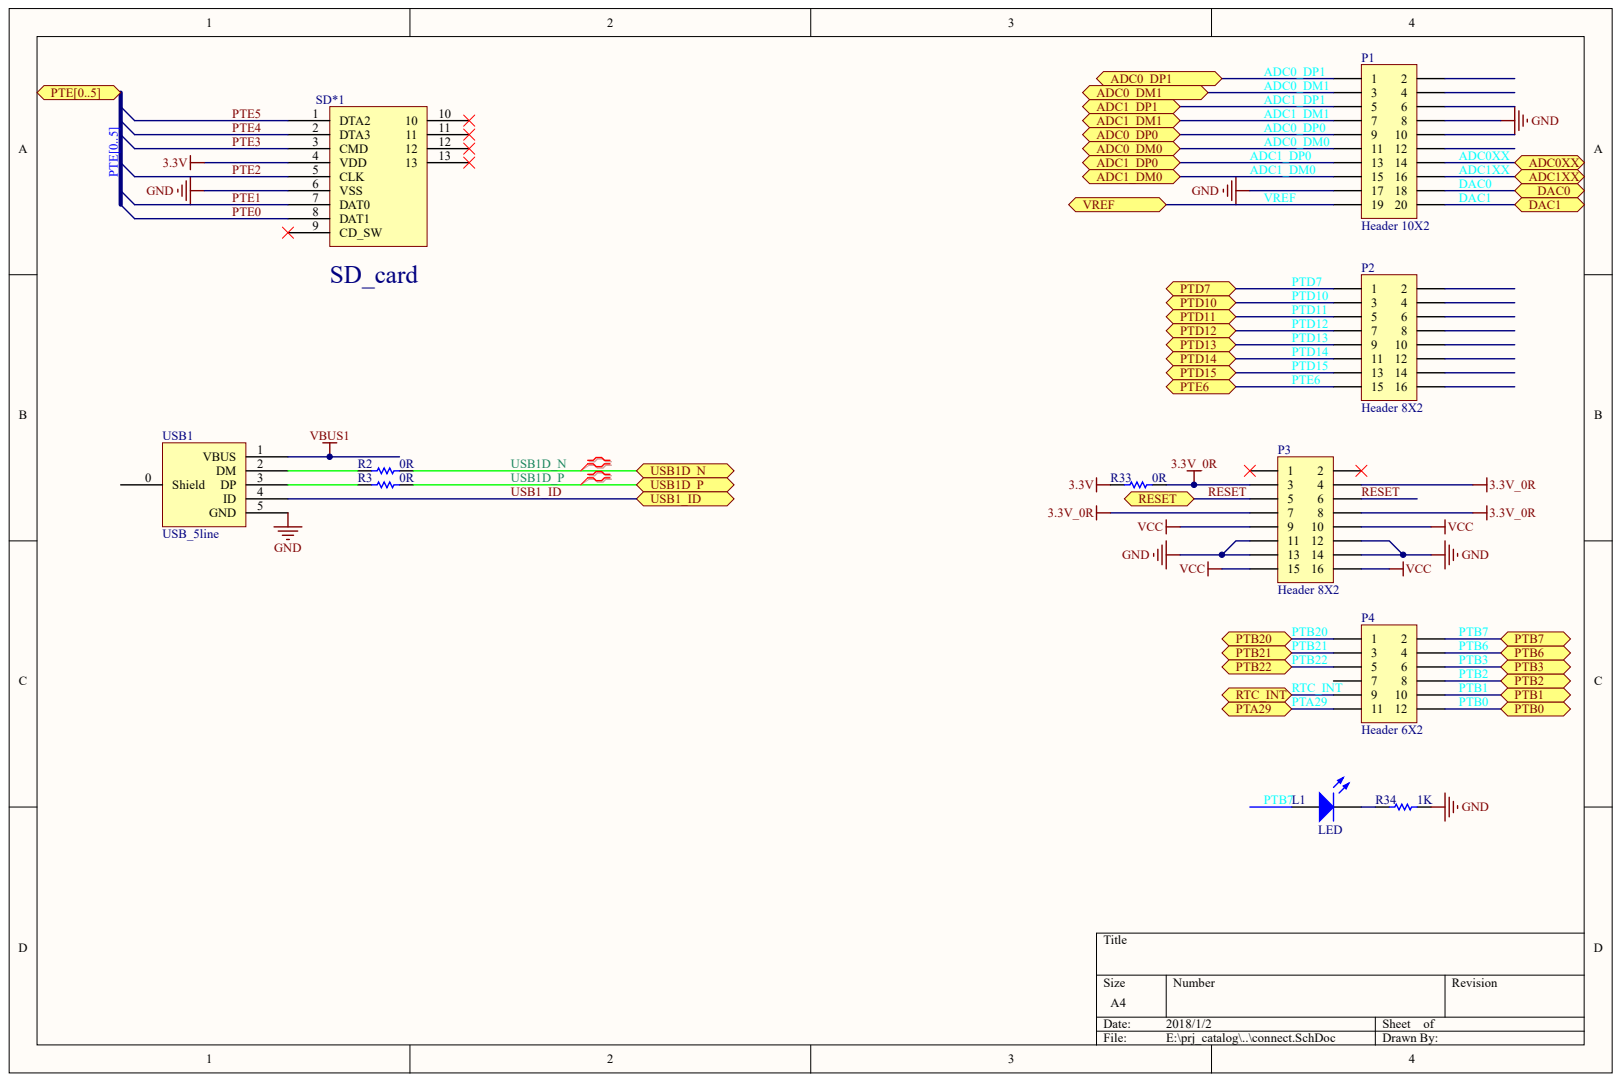
[picture p106: page 1]
