whutddk/MK64F-platform/PCB/pre-release-version/abort-version/1.6.1/MCU.PDF

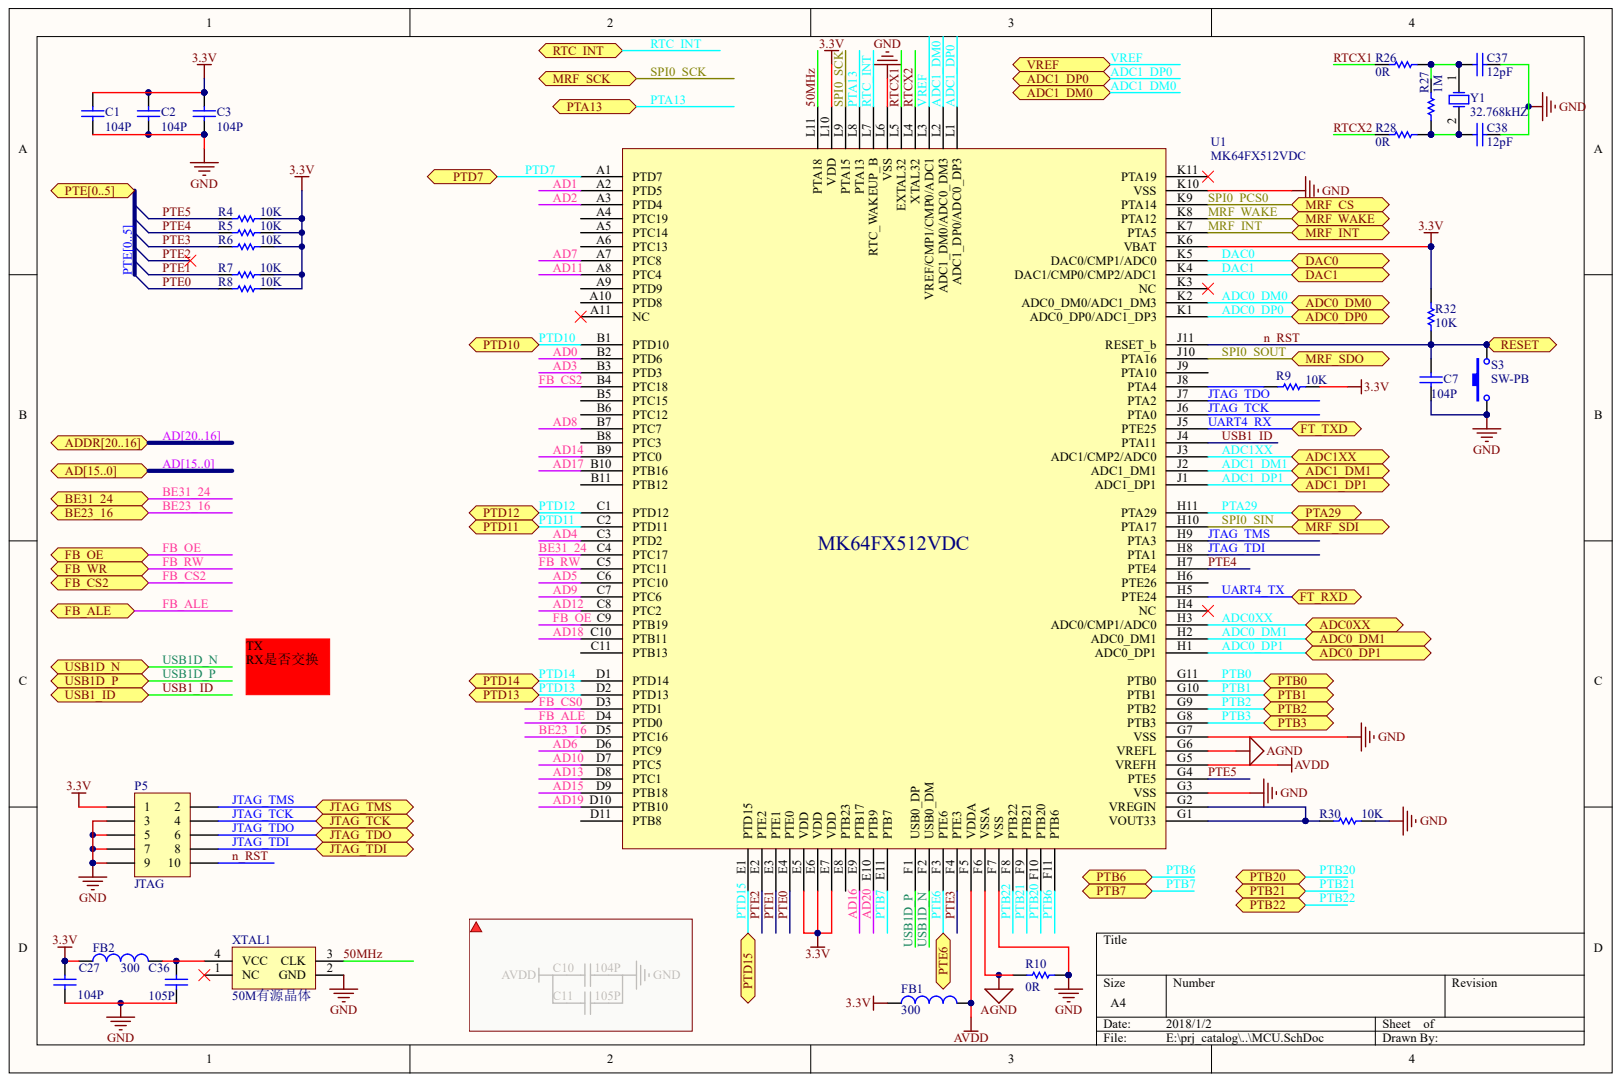
[picture p107: page 1]
