whutddk/MK64F-platform/PCB/pre-release-version/abort-version/1.6.1/RAM.PDF

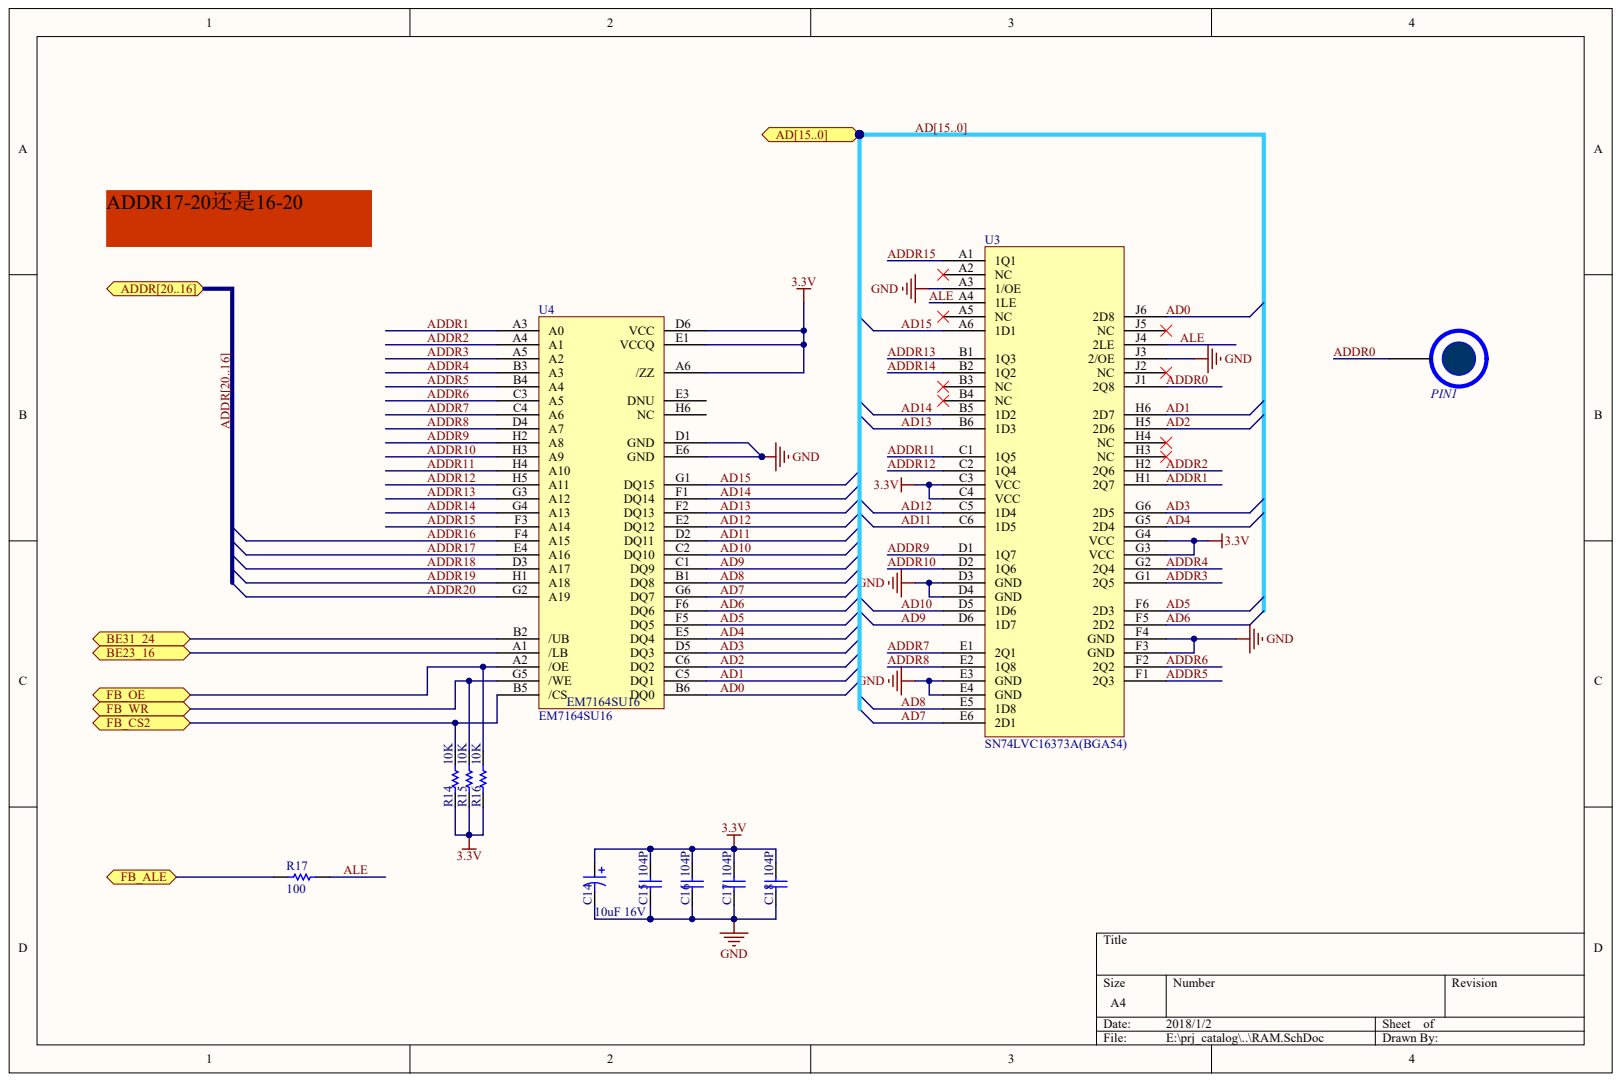
[picture p108: page 1]
