whutddk/MK64F-platform/PCB/pre-release-version/abort-version/1.6.1/USB.PDF

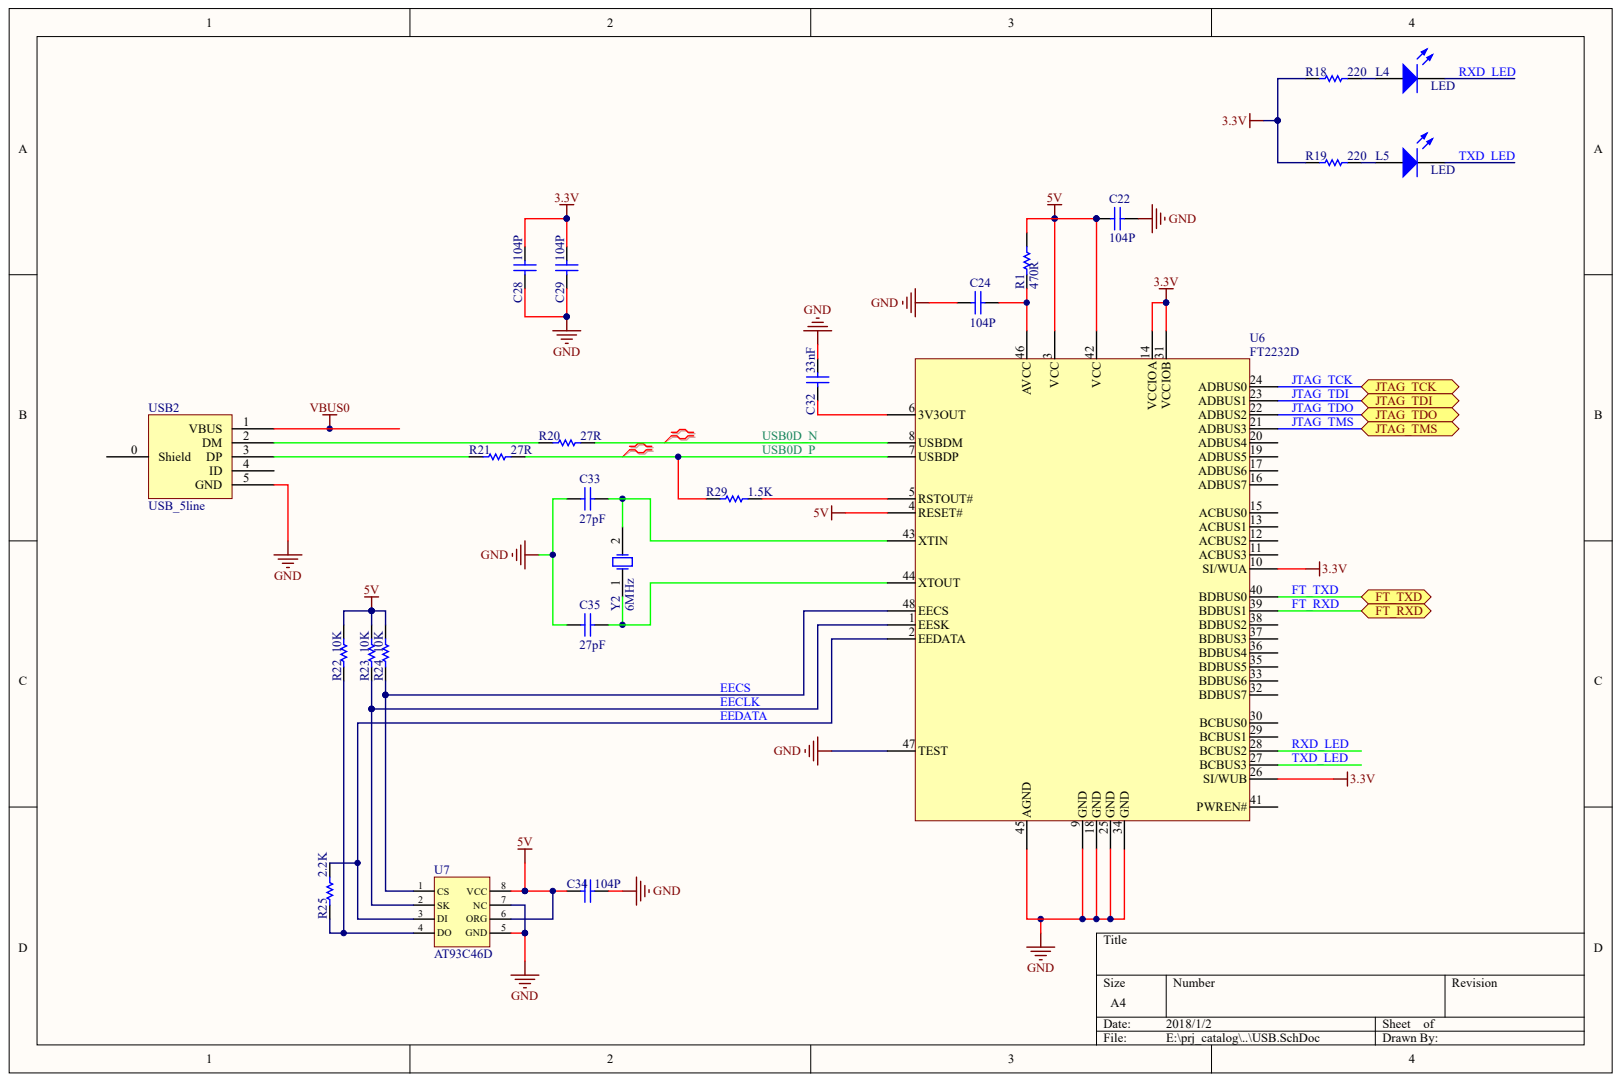
[picture p109: page 1]

EECS 48

EEDATA 2

EECLK
EEDATA
