whutddk/MK64F-platform/doc/referDoc/K64-tower/tower-mem/Freescale Tower/TWR-MEM (PWB RevB)/FAB-26248_B.pdf

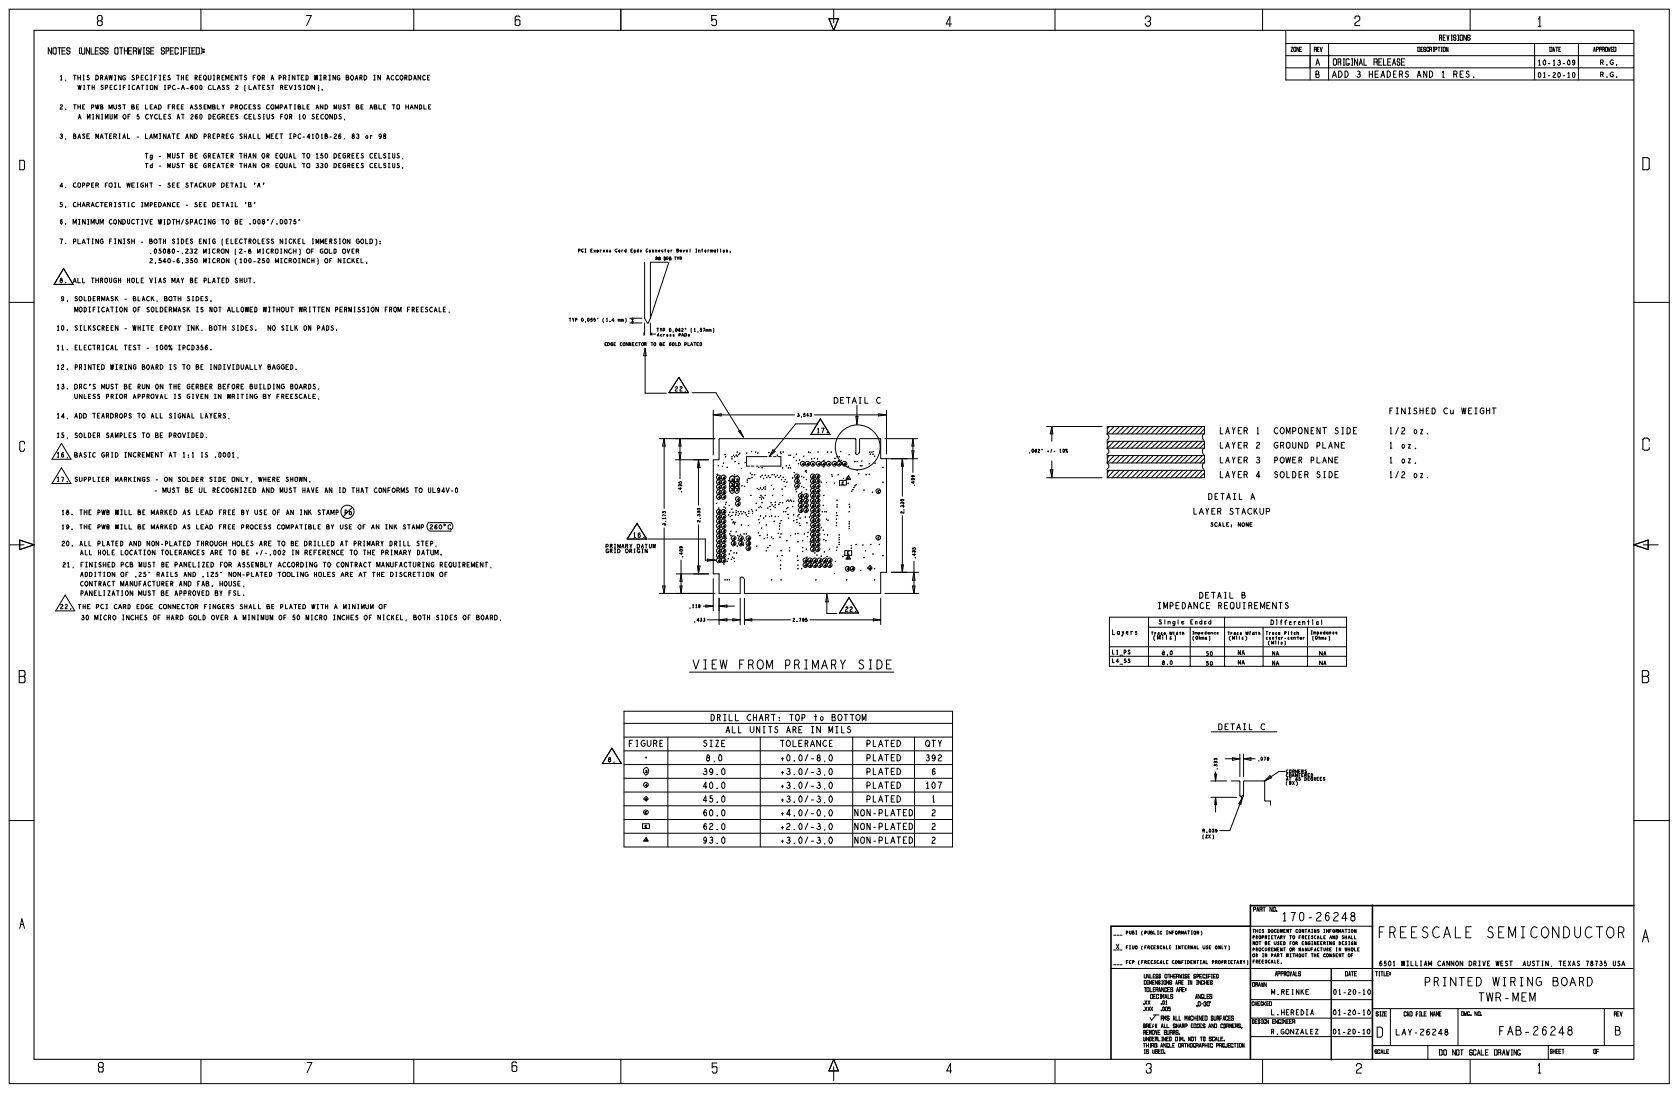
[picture p110: page 1]
